schmidtmt/openmotorbridge/docs/images/cad/cvo_25_anniversary_eagle_master.png

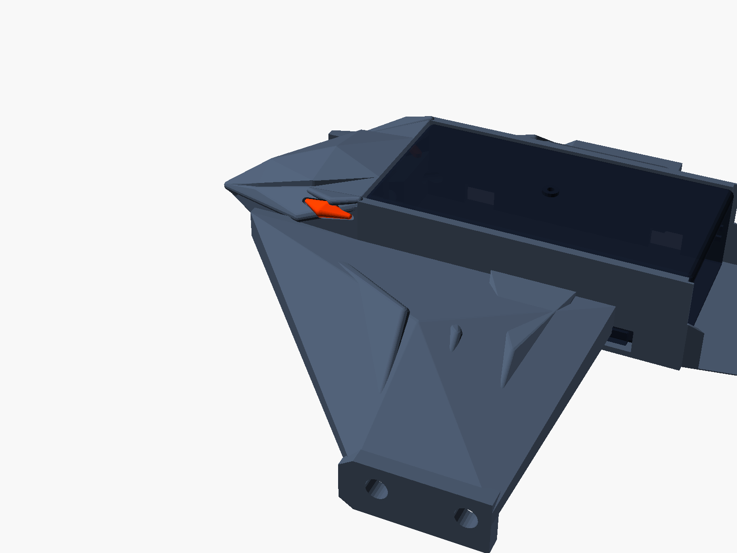
docs/images/cad/cvo_25_anniversary_eagle_master.png
