schmidtmt/openmotorbridge/docs/images/cad/cvo_st_telemetry_fin_cad.png

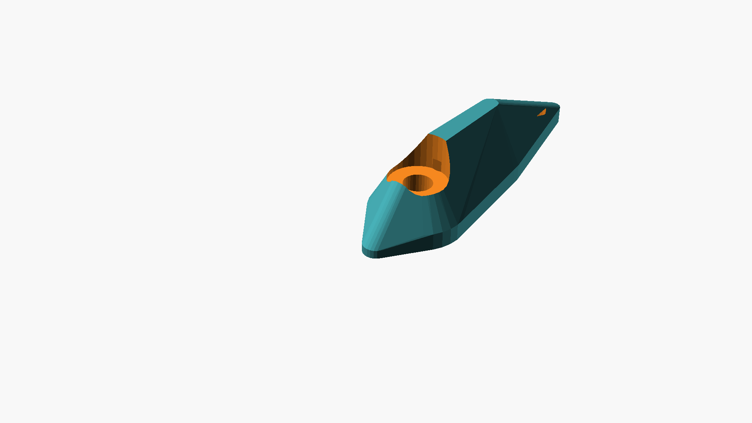
docs/images/cad/cvo_st_telemetry_fin_cad.png
