schmidtmt/openmotorbridge/docs/images/cad/cvo_st_undercowl_skeleton_dock_cad.png

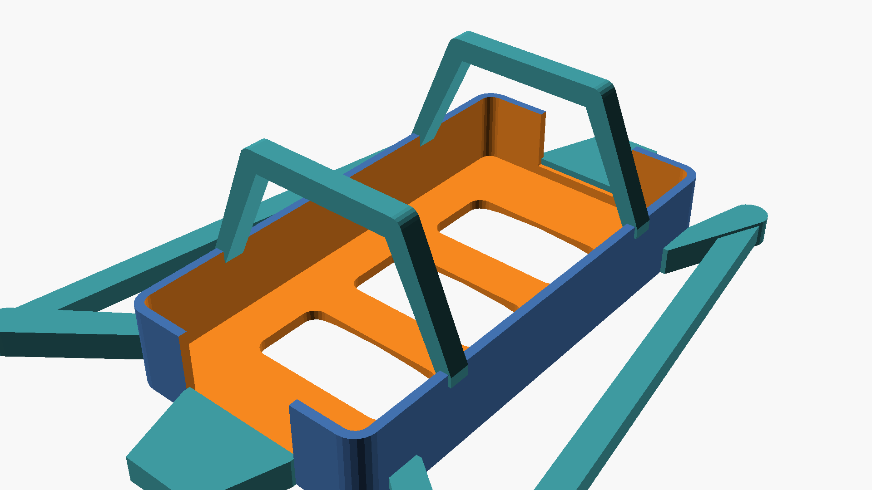
docs/images/cad/cvo_st_undercowl_skeleton_dock_cad.png
