schmidtmt/openmotorbridge/docs/images/cad/fender_curved_saddle_cad.png

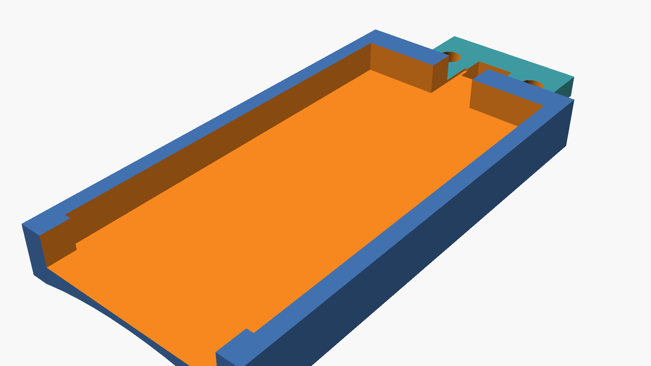
docs/images/cad/fender_curved_saddle_cad.png
