schmidtmt/openmotorbridge/docs/images/cad/front_node_3d_render_bottom.png

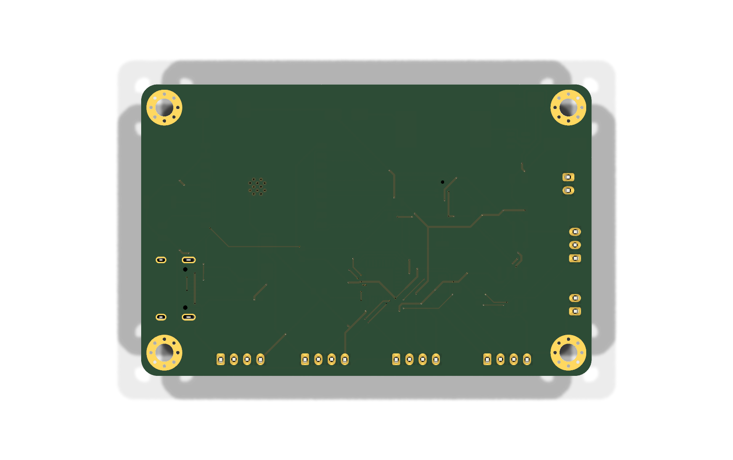
docs/images/cad/front_node_3d_render_bottom.png
