schmidtmt/openmotorbridge/docs/images/cad/front_node_3d_render_top.png

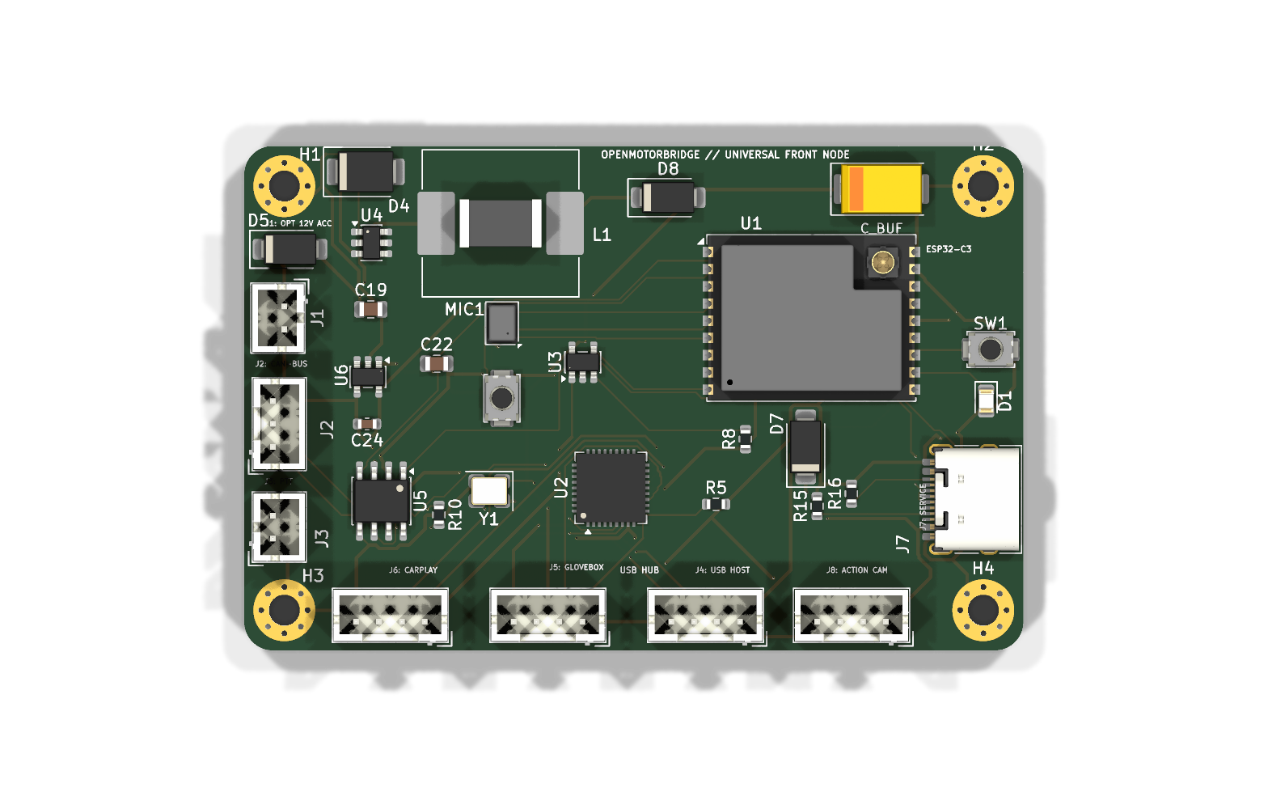
docs/images/cad/front_node_3d_render_top.png
