schmidtmt/openmotorbridge/docs/images/cad/main_board_pcb_top_down.png

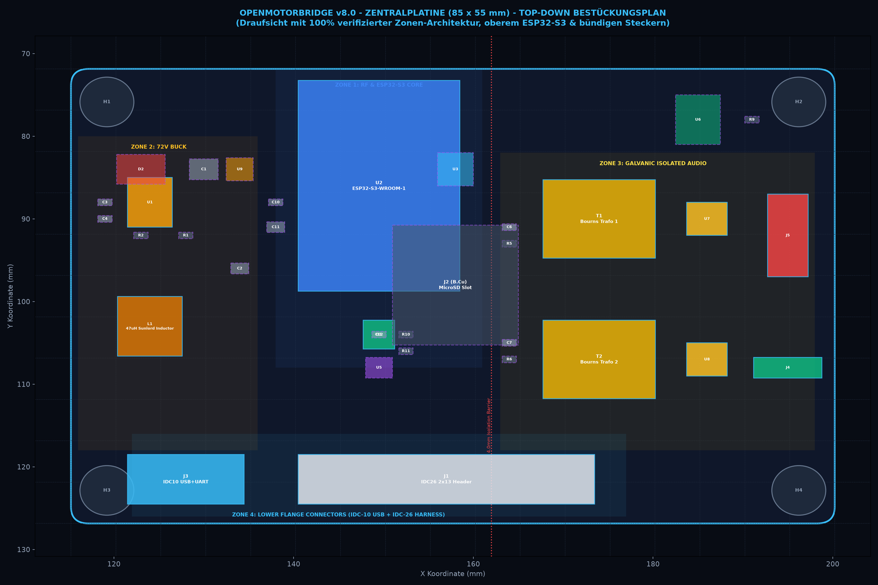
docs/images/cad/main_board_pcb_top_down.png
