schmidtmt/openmotorbridge/docs/images/cad/openmotorbridge_pod_exploded_view.png

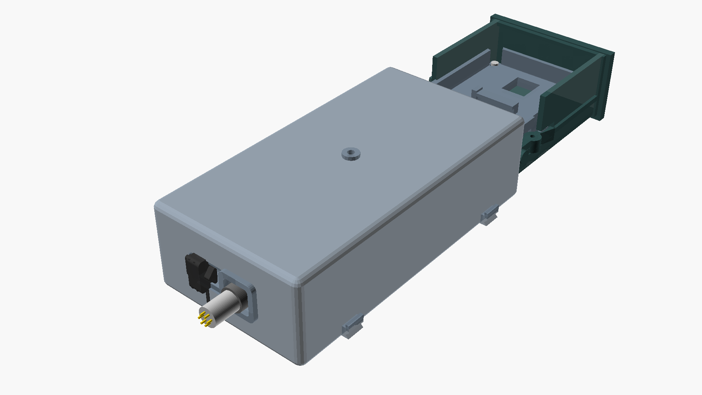
docs/images/cad/openmotorbridge_pod_exploded_view.png
