schmidtmt/openmotorbridge/docs/images/cad/pod3_fender_exploded_stack_3d.png

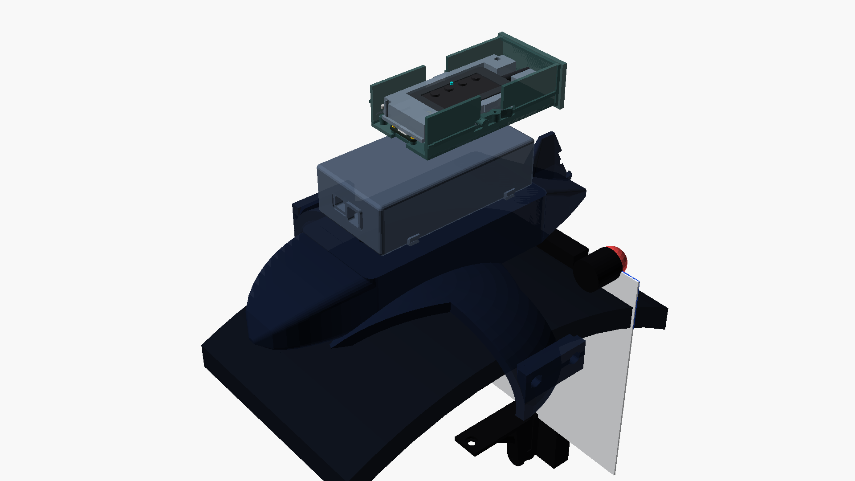
docs/images/cad/pod3_fender_exploded_stack_3d.png
