schmidtmt/openmotorbridge/docs/images/cad/pod3_radar_cutaway_3d.png

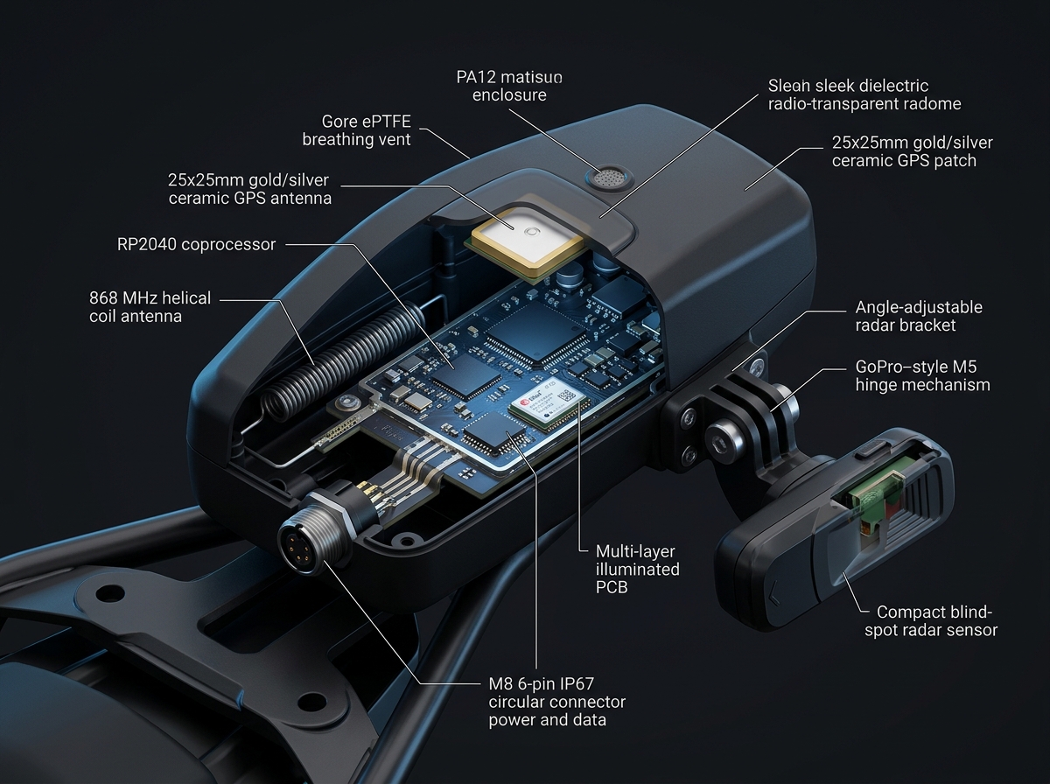
docs/images/cad/pod3_radar_cutaway_3d.png
