schmidtmt/openmotorbridge/docs/images/cad/pod3_st_aero_winglet_cad.png

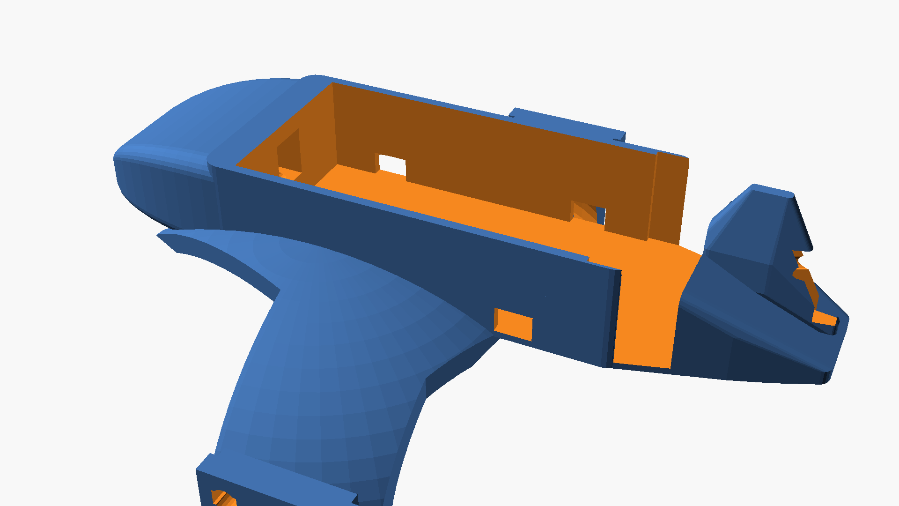
docs/images/cad/pod3_st_aero_winglet_cad.png
