schmidtmt/openmotorbridge/docs/images/cad/pod3_st_f117_stealth_nacelle.png

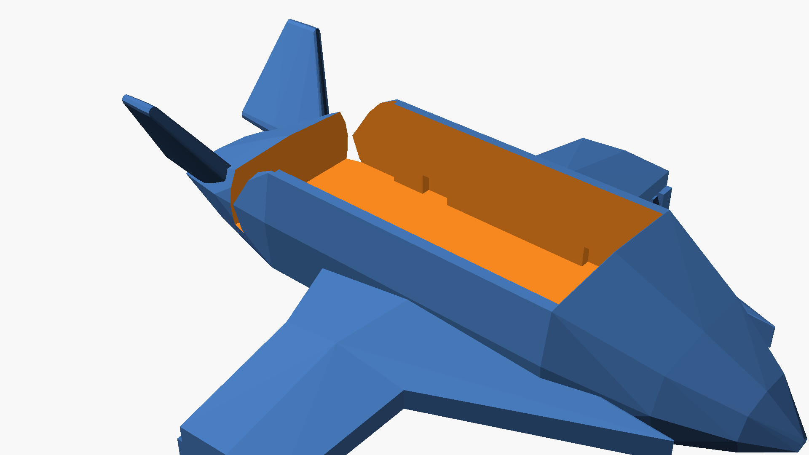
docs/images/cad/pod3_st_f117_stealth_nacelle.png
