schmidtmt/openmotorbridge/docs/images/cad/pod3_touring_fender_console.png

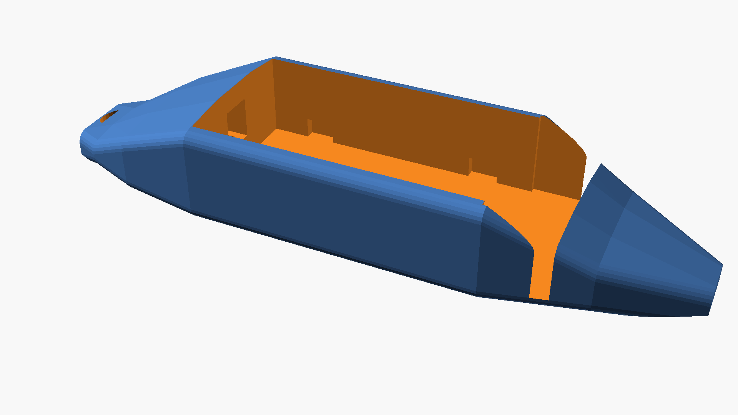
docs/images/cad/pod3_touring_fender_console.png
