schmidtmt/openmotorbridge/docs/images/cad/pod3_touring_fender_console_cad.png

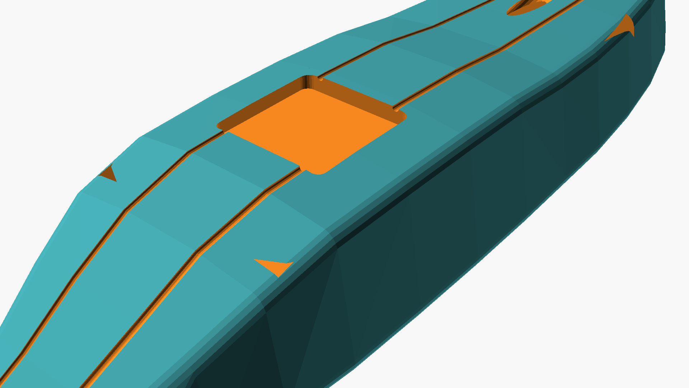
docs/images/cad/pod3_touring_fender_console_cad.png
