schmidtmt/openmotorbridge/docs/images/cad/pod3_touring_stealth_cad.png

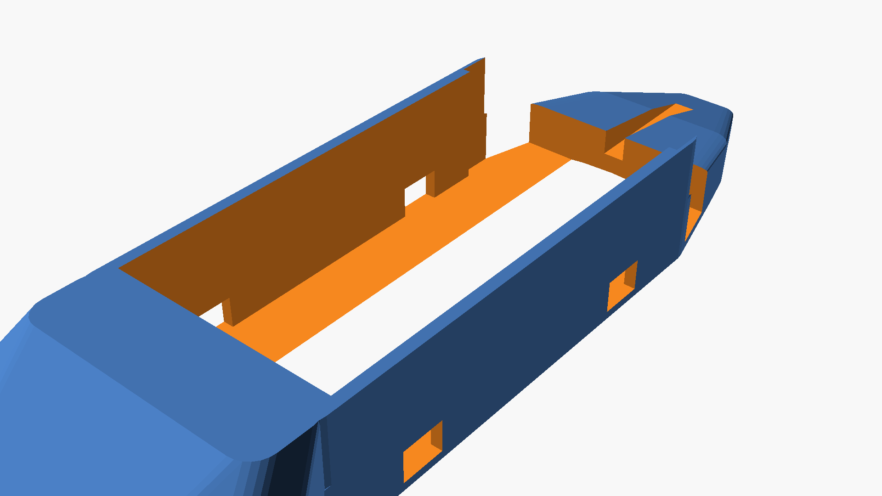
docs/images/cad/pod3_touring_stealth_cad.png
