schmidtmt/openmotorbridge/docs/images/cad/pod_base_rear_dual_port_cad.png

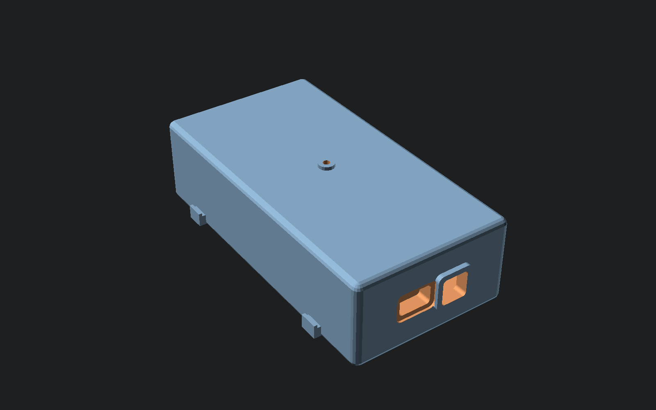
docs/images/cad/pod_base_rear_dual_port_cad.png
