schmidtmt/openmotorbridge/docs/images/cad/rack_tail_mount_cad.png

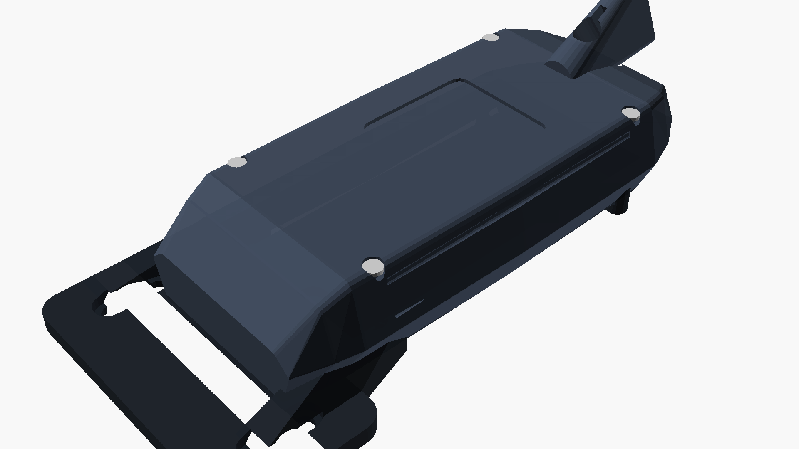
docs/images/cad/rack_tail_mount_cad.png
