schmidtmt/openmotorbridge/docs/images/cad/rack_tail_mount_side_cross_section.png

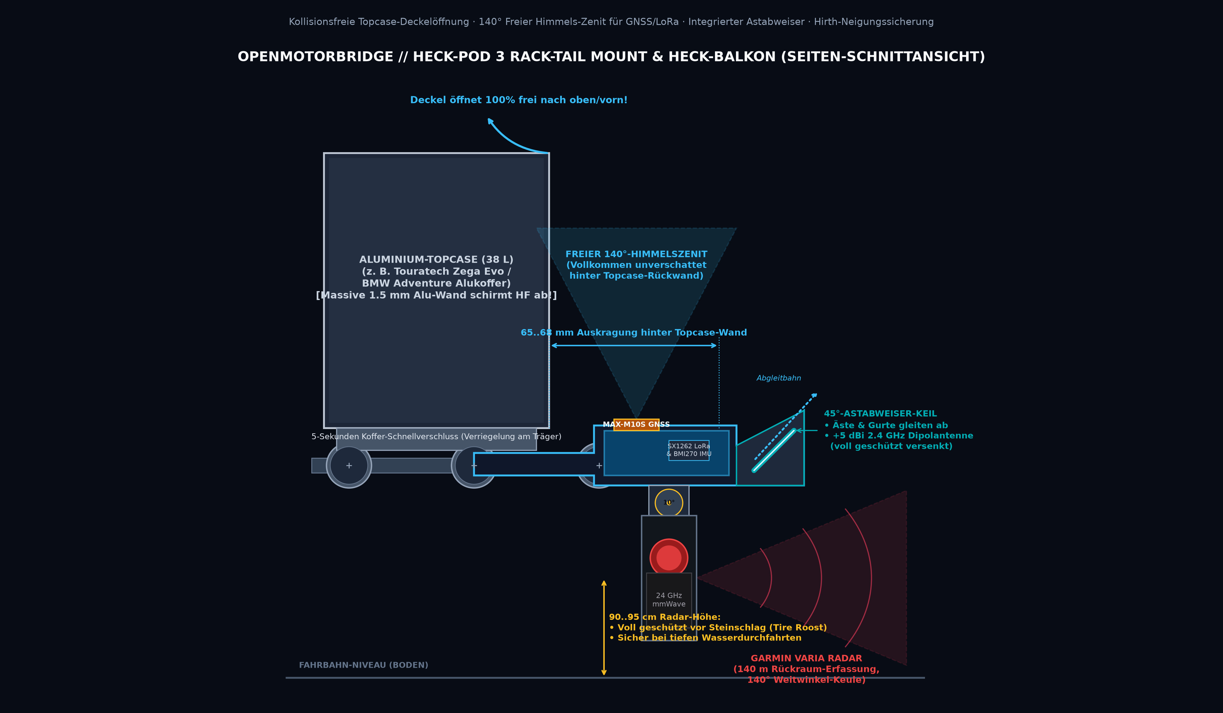
docs/images/cad/rack_tail_mount_side_cross_section.png
