schmidtmt/openmotorbridge/docs/images/cad/rack_tail_mount_top_view.png

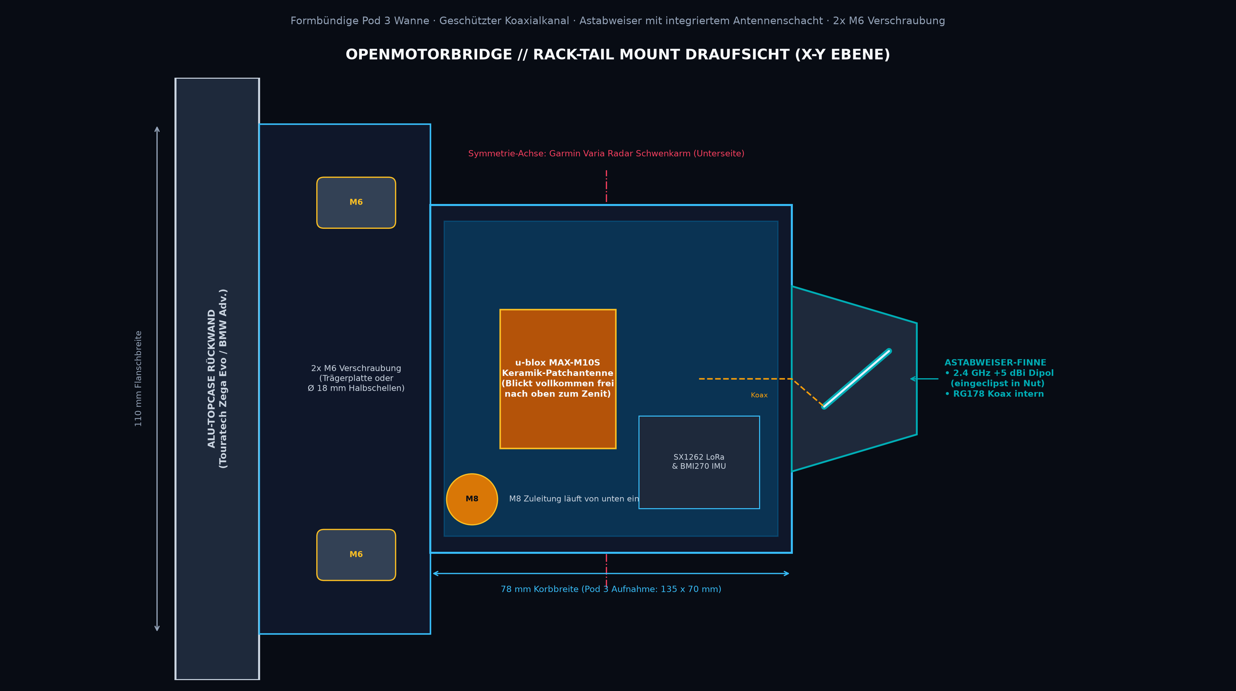
docs/images/cad/rack_tail_mount_top_view.png
