schmidtmt/openmotorbridge/docs/images/cad/radar_hirth_lock_dock_cad.png

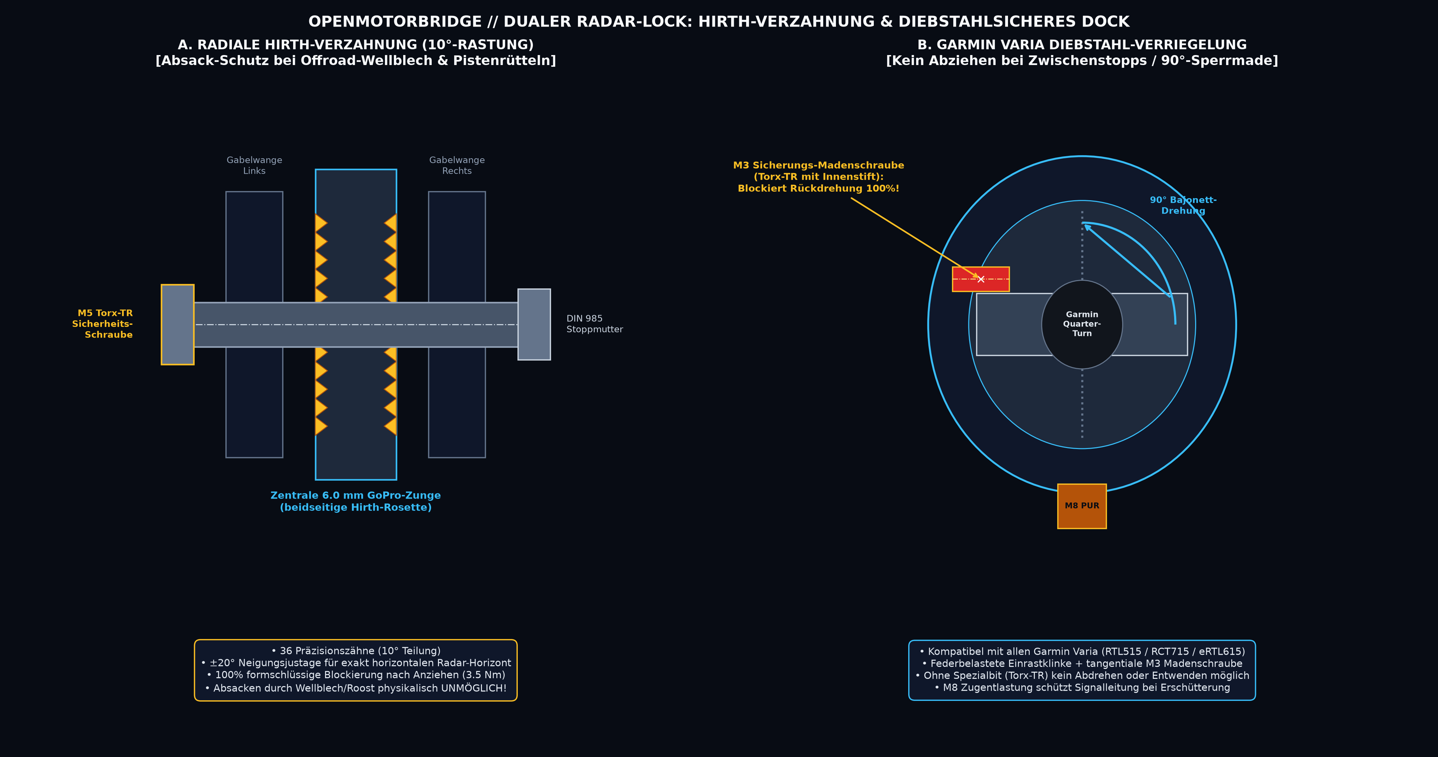
docs/images/cad/radar_hirth_lock_dock_cad.png
