schmidtmt/openmotorbridge/docs/images/pcba/pcba01_central_box_top.png

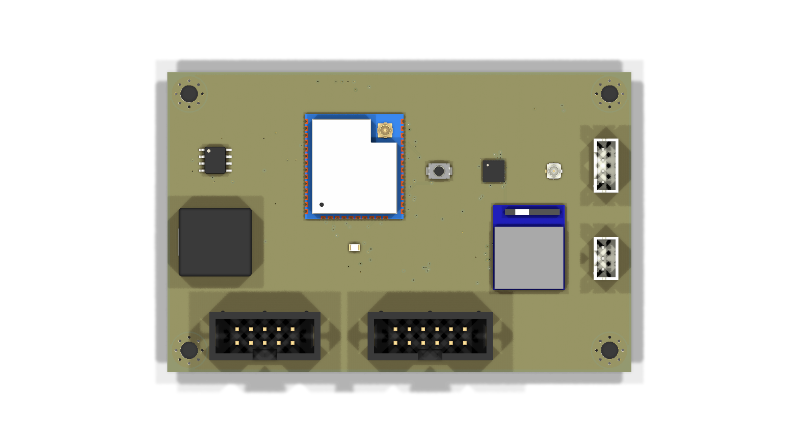
docs/images/pcba/pcba01_central_box_top.png
