schmidtmt/openmotorbridge/docs/images/pcba/pcba02_pod_base_3d.png

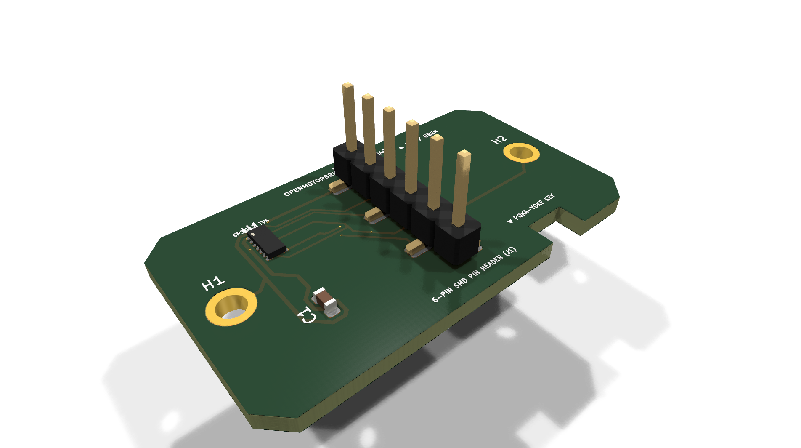
docs/images/pcba/pcba02_pod_base_3d.png
