schmidtmt/openmotorbridge/docs/images/pcba/pcba03_pod_cartridge_top.png

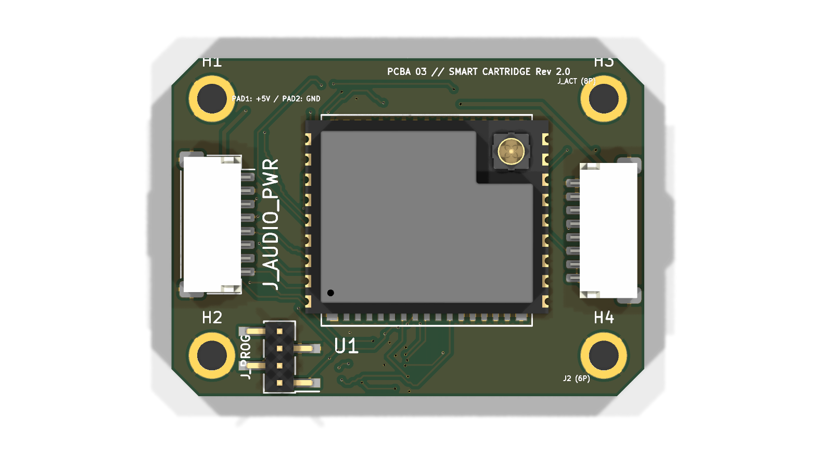
docs/images/pcba/pcba03_pod_cartridge_top.png
