schmidtmt/openmotorbridge/docs/images/pcba/pcba04_rear_pod3_3d.png

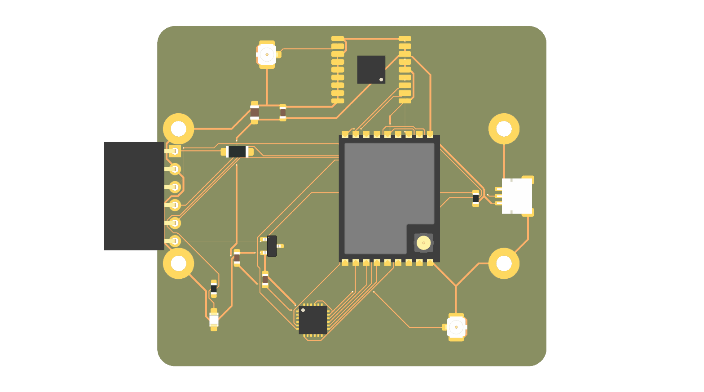
docs/images/pcba/pcba04_rear_pod3_3d.png
