schmidtmt/openmotorbridge/docs/images/pcba/pcba05_front_node_top.png

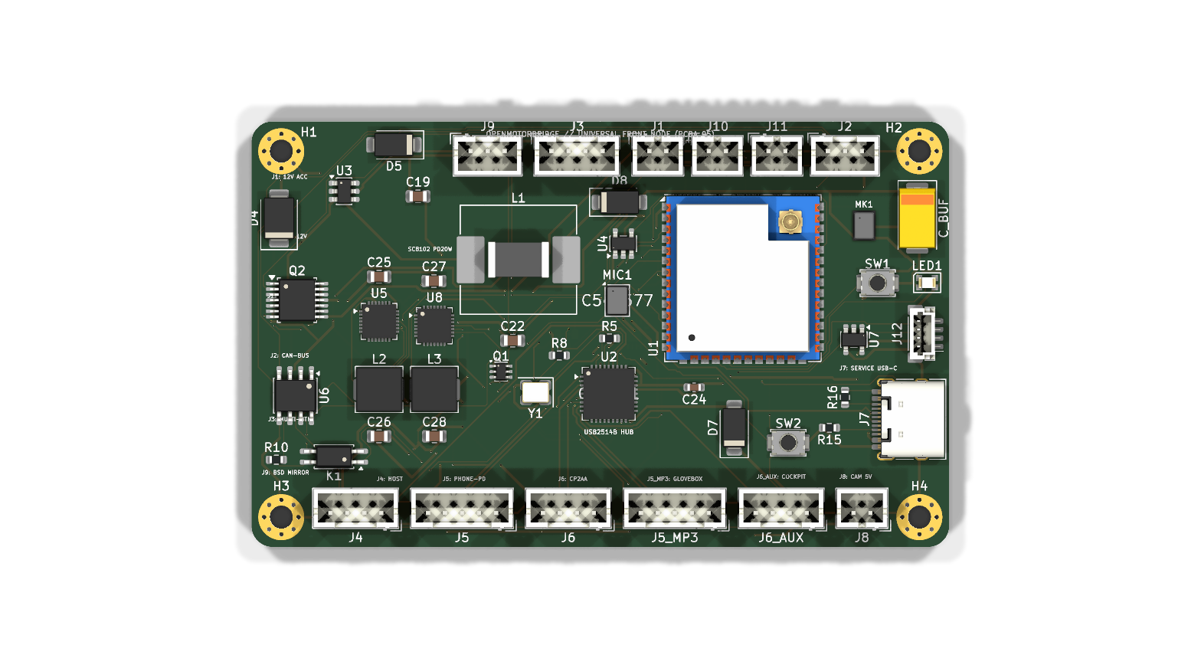
docs/images/pcba/pcba05_front_node_top.png
