schmidtmt/openmotorbridge/docs/images/pcba/pcba06_magsafe_dock_bottom_3d.png

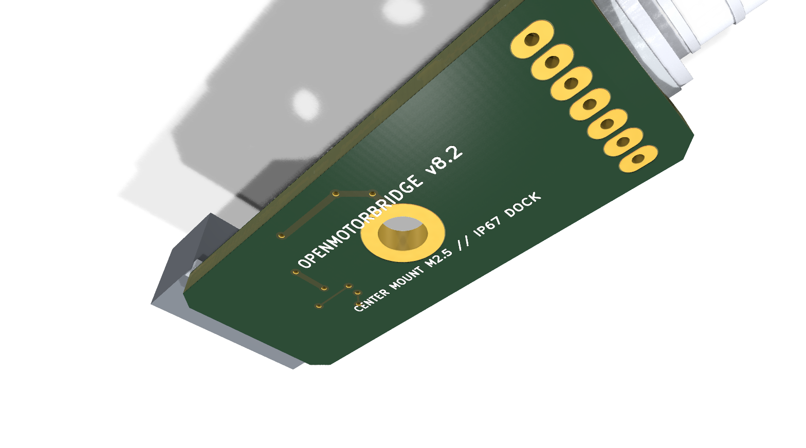
docs/images/pcba/pcba06_magsafe_dock_bottom_3d.png
