schmidtmt/openmotorbridge/docs/images/pcba/pcba06_magsafe_dock_top.png

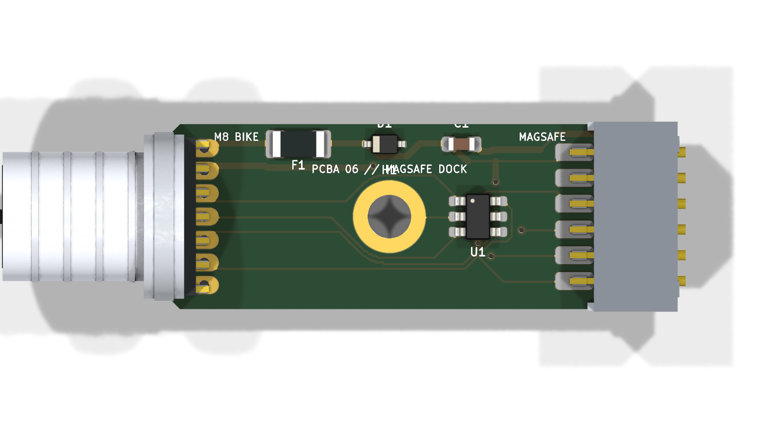
docs/images/pcba/pcba06_magsafe_dock_top.png
