schmidtmt/openmotorbridge/docs/images/pcba/pcba07_smart_keyfob_top.png

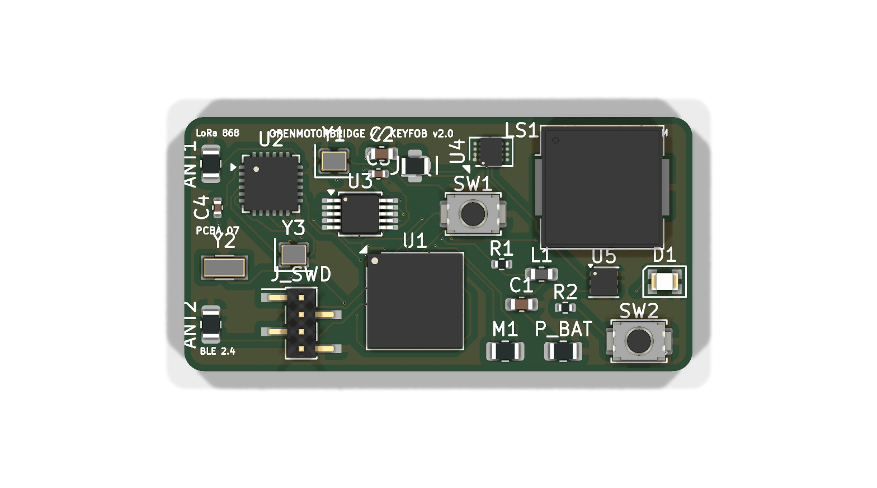
docs/images/pcba/pcba07_smart_keyfob_top.png
