schmidtmt/openmotorbridge/docs/images/pcba/pcba08_radar_submcu_bottom_3d.png

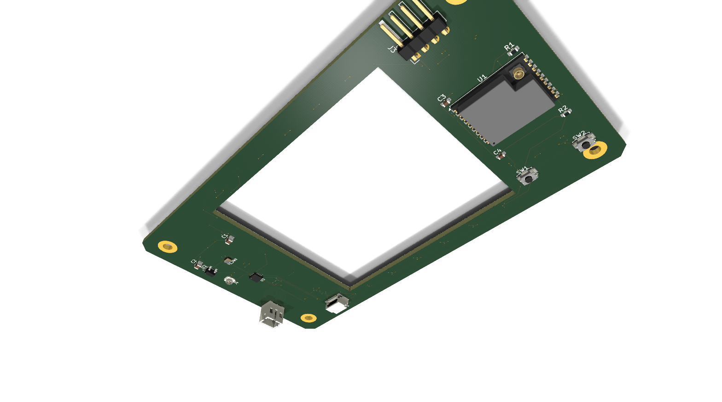
docs/images/pcba/pcba08_radar_submcu_bottom_3d.png
