schmidtmt/openmotorbridge/docs/images/pcba/pcba09_omm_intercom_bottom.png

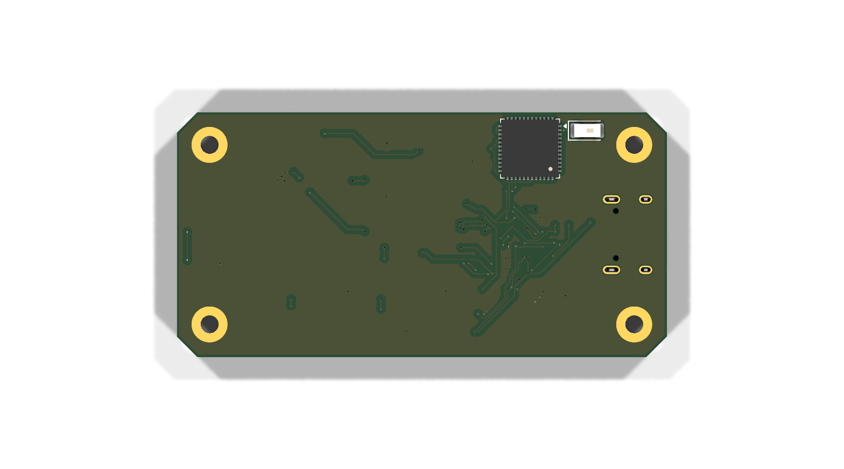
docs/images/pcba/pcba09_omm_intercom_bottom.png
