schmidtmt/openmotorbridge/docs/images/pcba/pcba09_omm_intercom_top.png

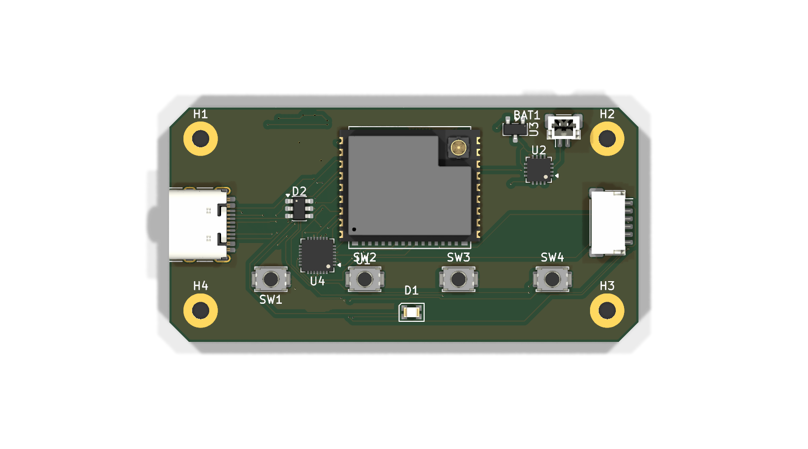
docs/images/pcba/pcba09_omm_intercom_top.png
