schmidtmt/openmotorbridge/docs/images/pcba/pcba10_omm446_intercom_bottom.png

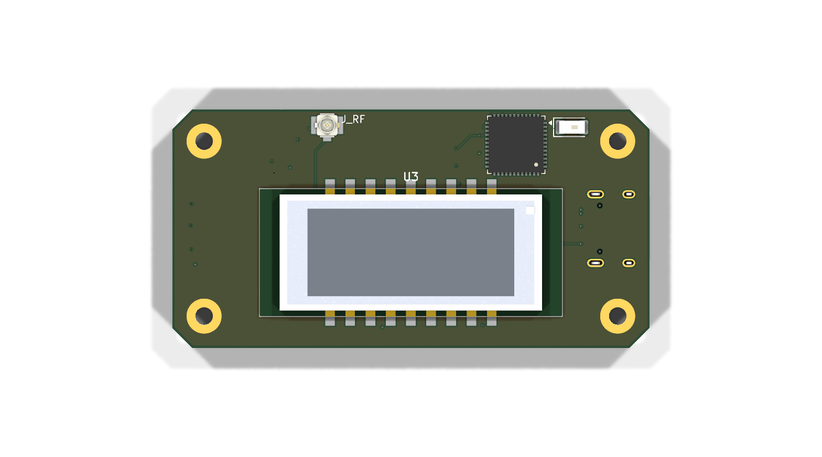
docs/images/pcba/pcba10_omm446_intercom_bottom.png
