schmidtmt/openmotorbridge/docs/images/pwa/pwa_tab1_cockpit_radar_hud.png

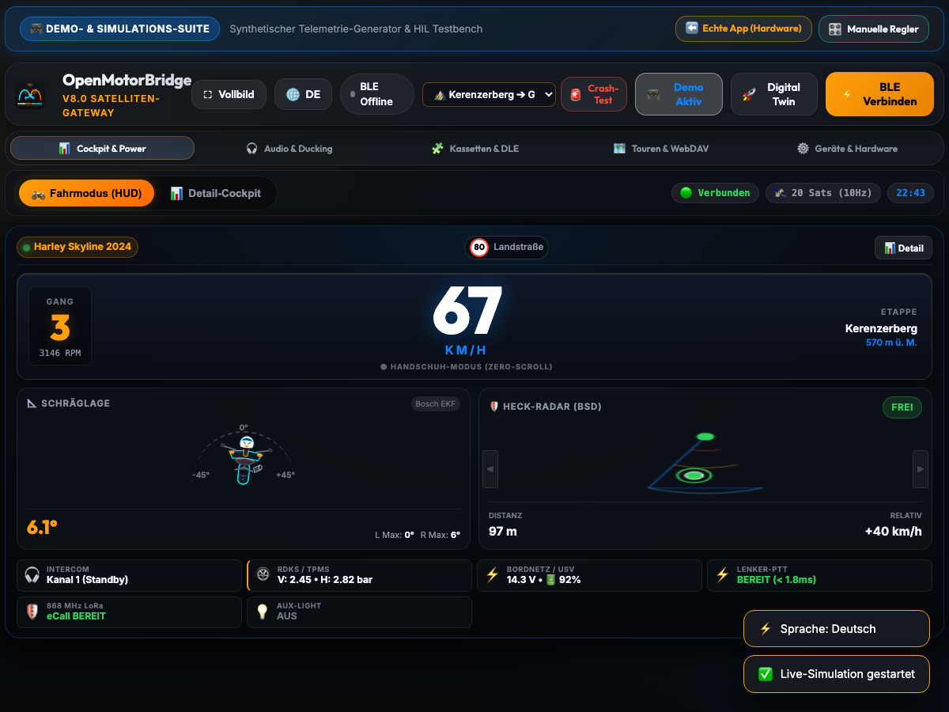
docs/images/pwa/pwa_tab1_cockpit_radar_hud.png
