schmidtmt/openmotorbridge/docs/images/pwa/pwa_tab2_audio_smart_cartridge.png

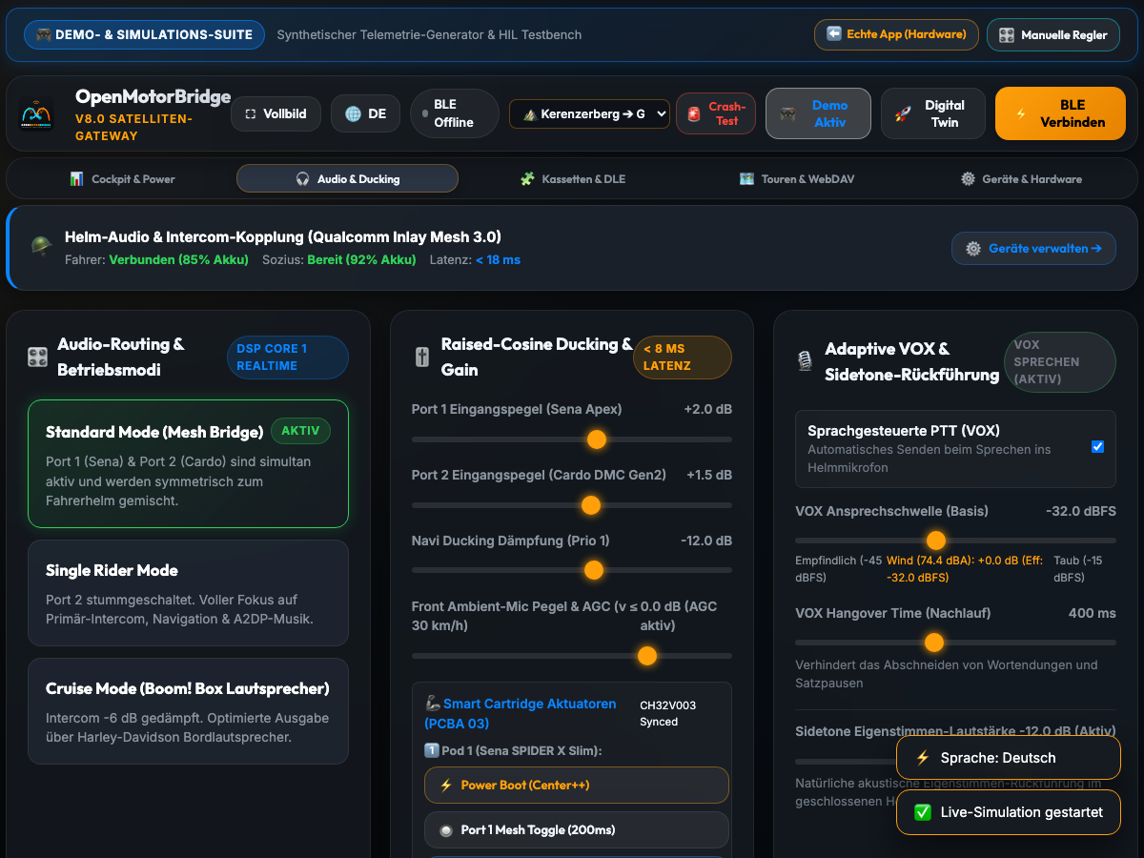
docs/images/pwa/pwa_tab2_audio_smart_cartridge.png
