schmidtmt/openmotorbridge/docs/images/pwa/pwa_tab3_cartridges_dle_status.png

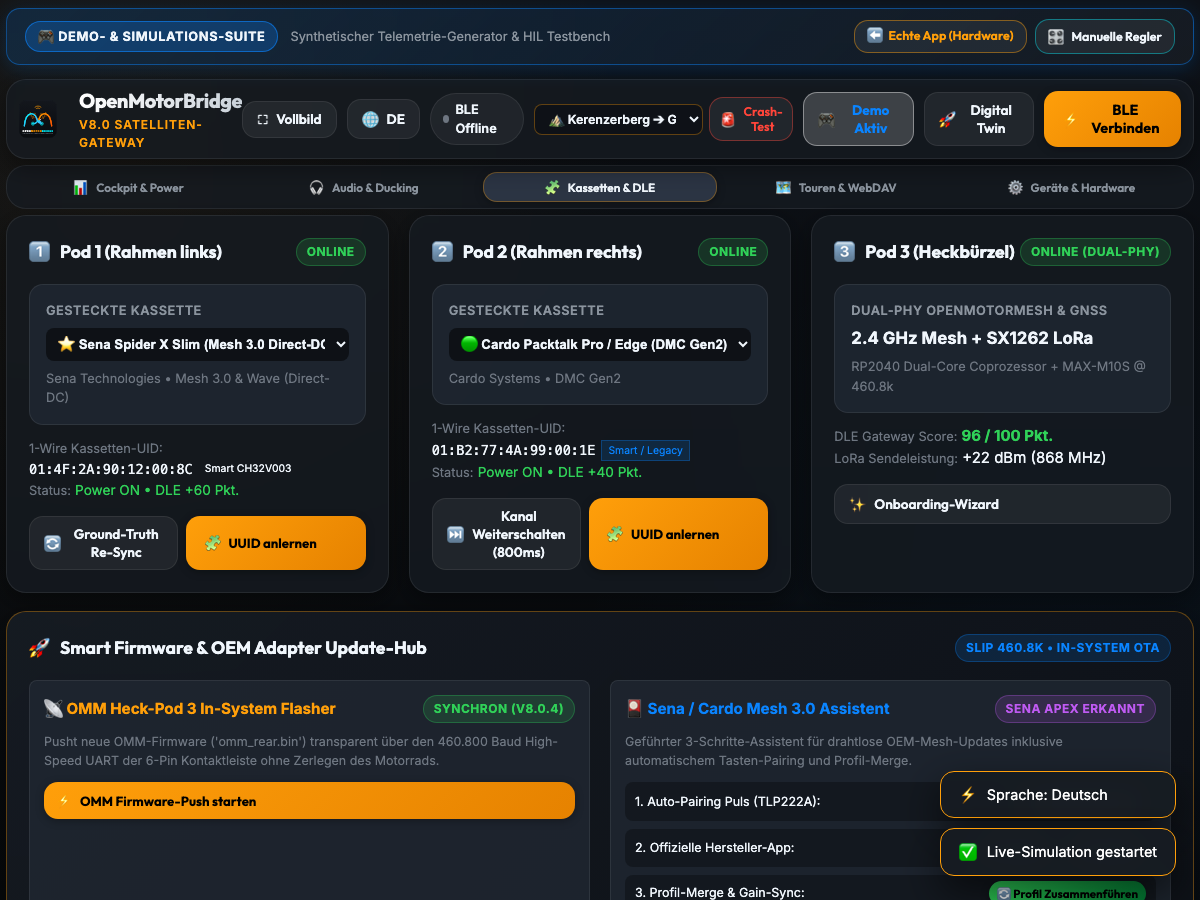
docs/images/pwa/pwa_tab3_cartridges_dle_status.png
