schmidtmt/openmotorbridge/docs/images/pwa/pwa_tab4_tours_gpx_export.png

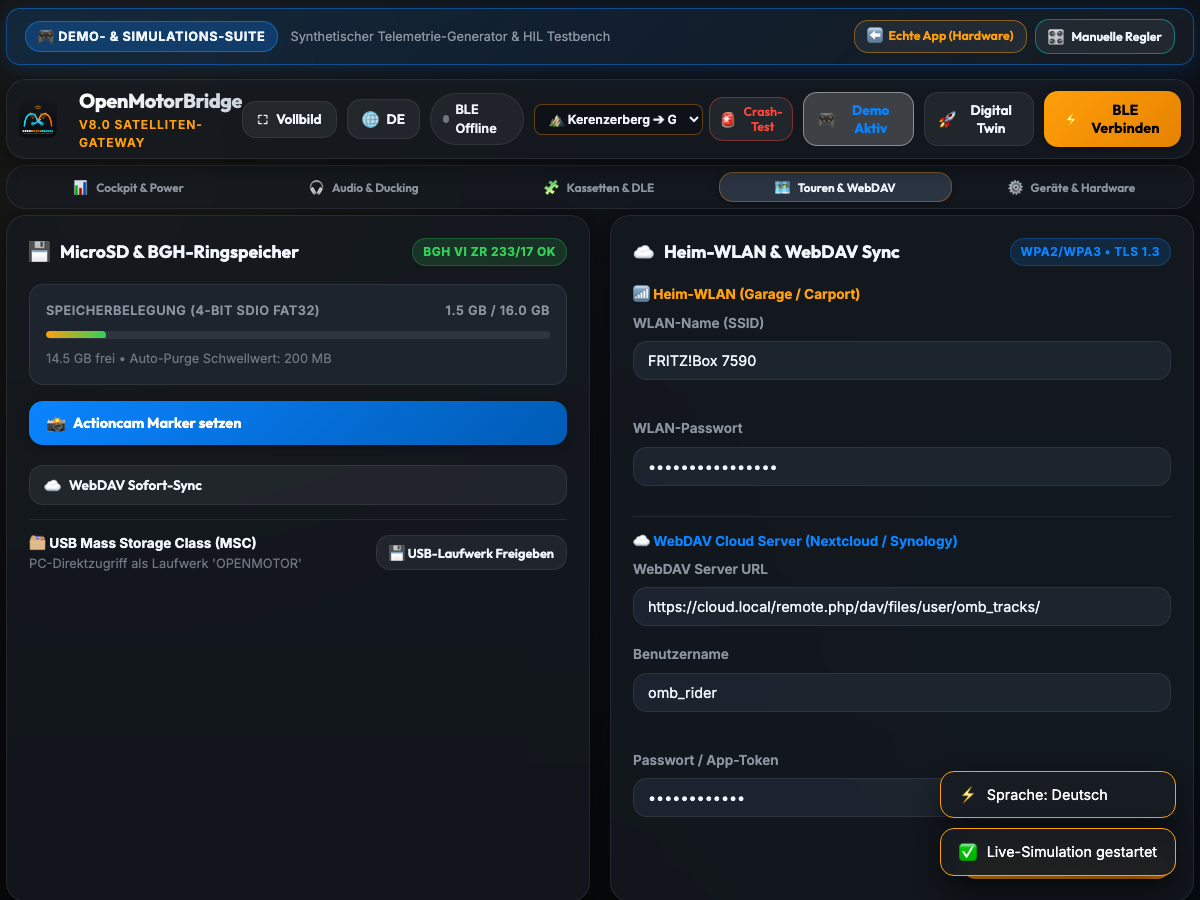
docs/images/pwa/pwa_tab4_tours_gpx_export.png
