schmidtmt/openmotorbridge/docs/images/pwa/pwa_tab5_device_hub_keyfob.png

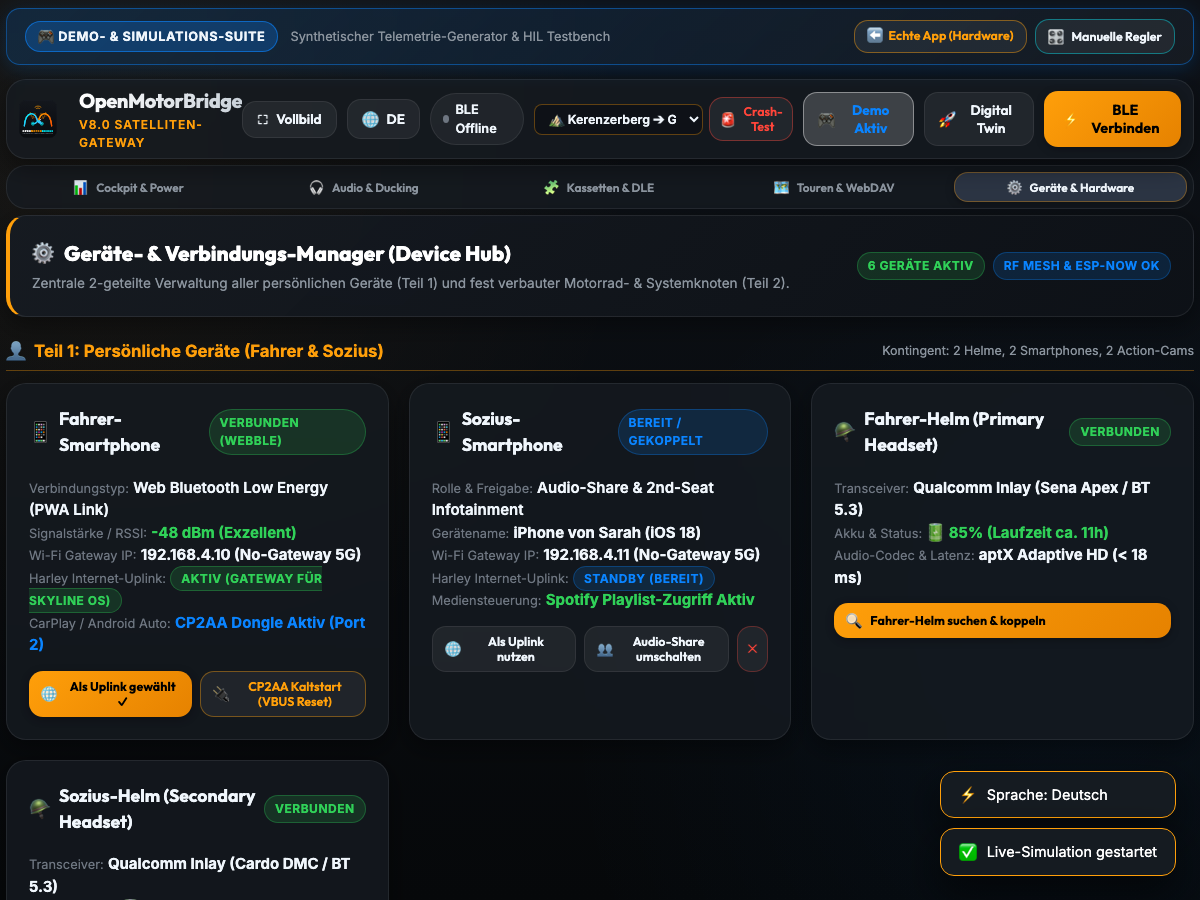
docs/images/pwa/pwa_tab5_device_hub_keyfob.png
