schmidtmt/openmotorbridge/hardware/cad/cartridge_variants_trio.png

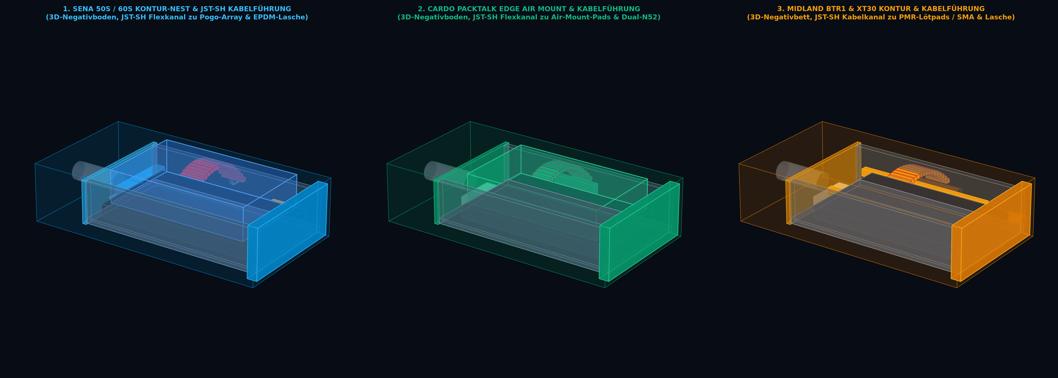
hardware/cad/cartridge_variants_trio.png
