schmidtmt/openmotorbridge/hardware/cad/dummy_cartridge_cad.png

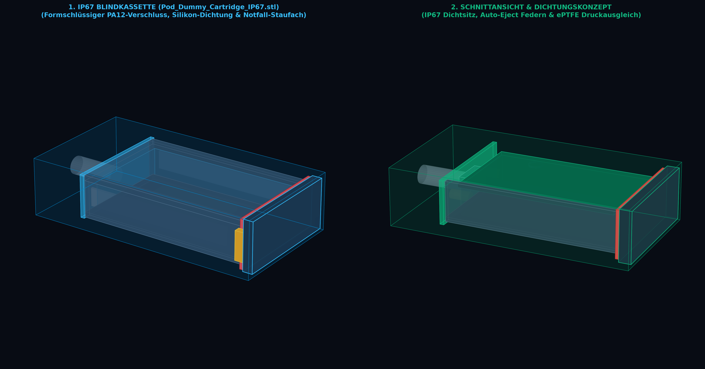
hardware/cad/dummy_cartridge_cad.png
