schmidtmt/openmotorbridge/hardware/cad/pod3_st_aero_winglet_cad.png

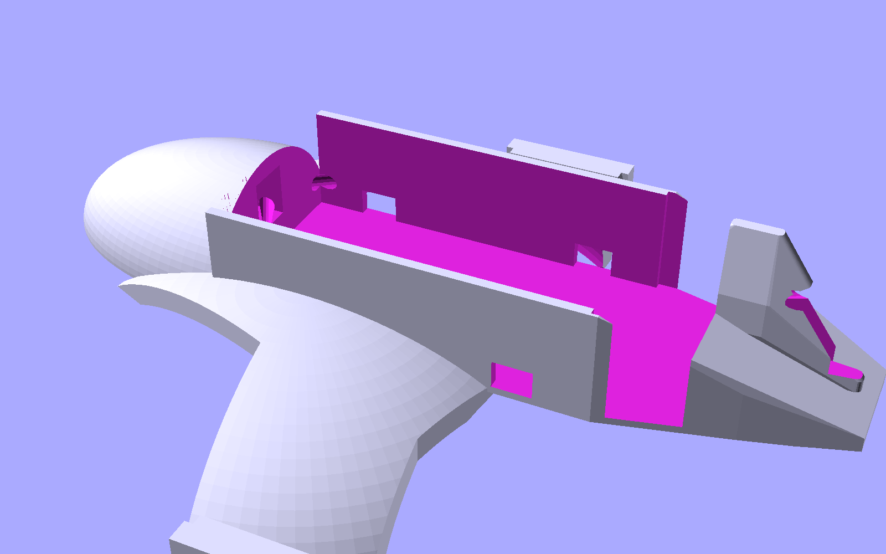
hardware/cad/pod3_st_aero_winglet_cad.png
