schmidtmt/openmotorbridge/hardware/kicad_pod_base/kicad_3d_render.png

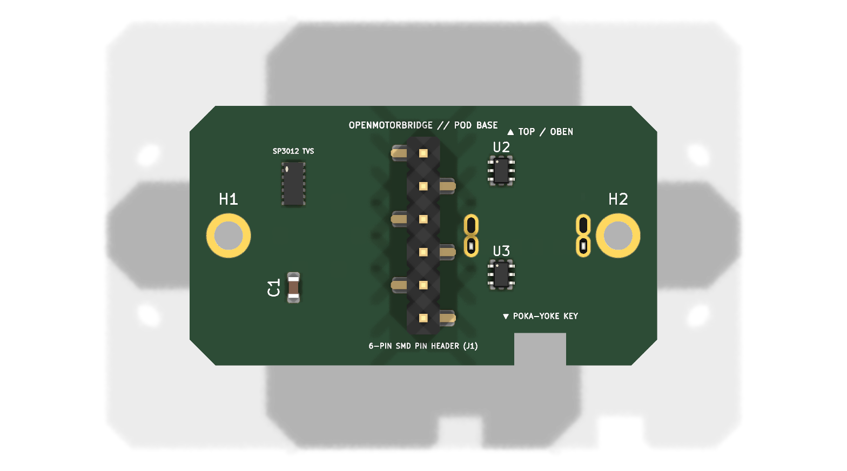
hardware/kicad_pod_base/kicad_3d_render.png
