schmidtmt/openmotorbridge/hardware/kicad_pod_base/kicad_3d_render_bottom.png

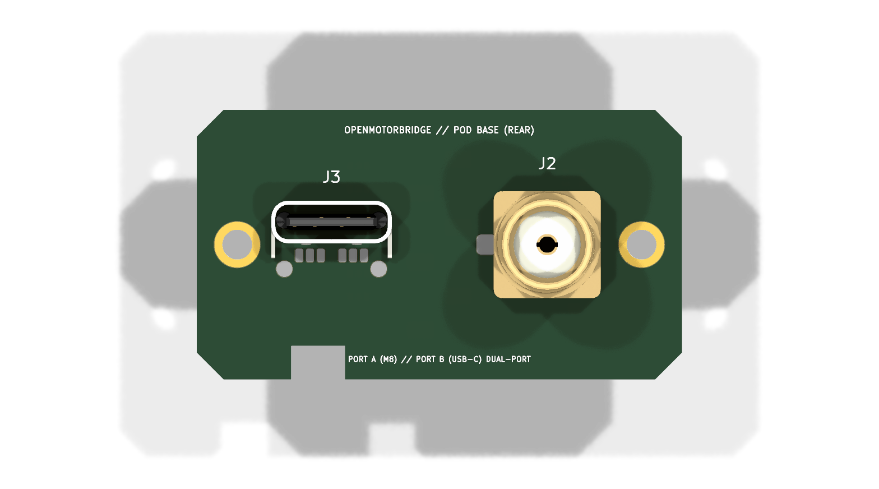
hardware/kicad_pod_base/kicad_3d_render_bottom.png
