schmidtmt/openmotorbridge/hardware/kicad_pod_base/pod_base_3d_iso_bottom.png

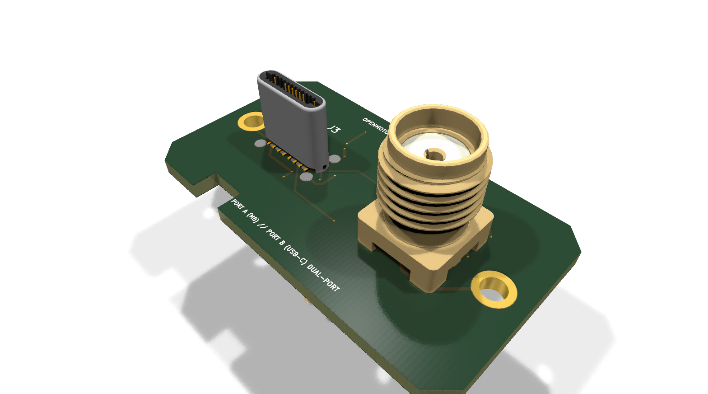
hardware/kicad_pod_base/pod_base_3d_iso_bottom.png
