schmidtmt/openmotorbridge/hardware/kicad_pod_base/pod_base_3d_render_top.png

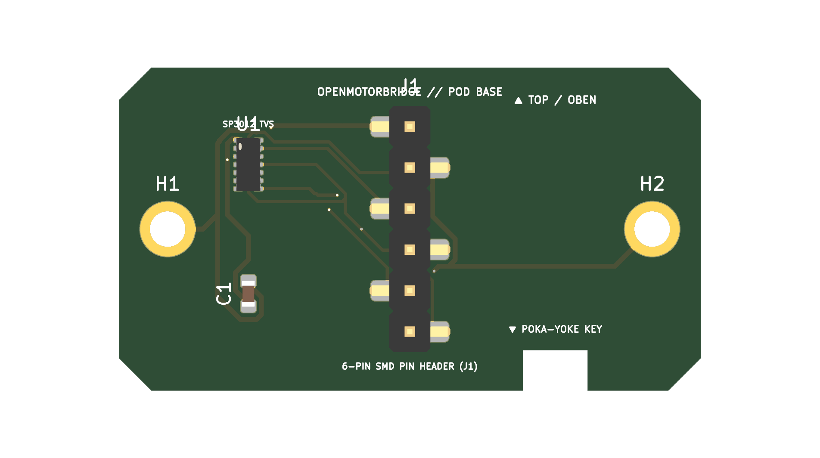
hardware/kicad_pod_base/pod_base_3d_render_top.png
