schmidtmt/openmotorbridge/hardware/kicad_pod_base/pod_base_smd_render_bottom.png

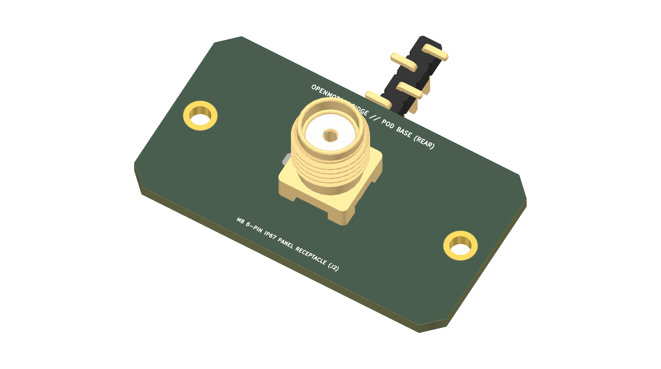
hardware/kicad_pod_base/pod_base_smd_render_bottom.png
