schmidtmt/openmotorbridge/hardware/kicad_pod_base/pod_base_vertical_bottom.png

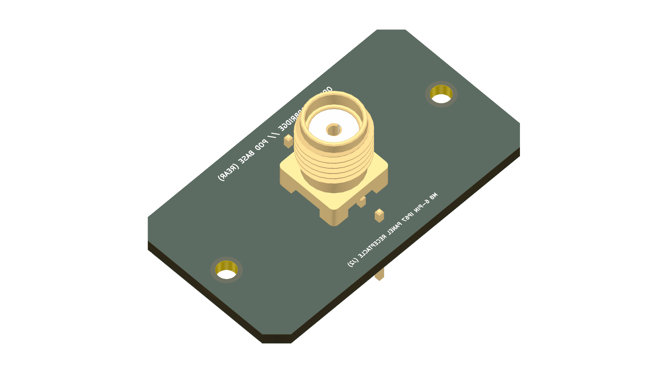
hardware/kicad_pod_base/pod_base_vertical_bottom.png
