schmidtmt/openmotorbridge/hardware/kicad_pod_base/pod_base_vertical_top.png

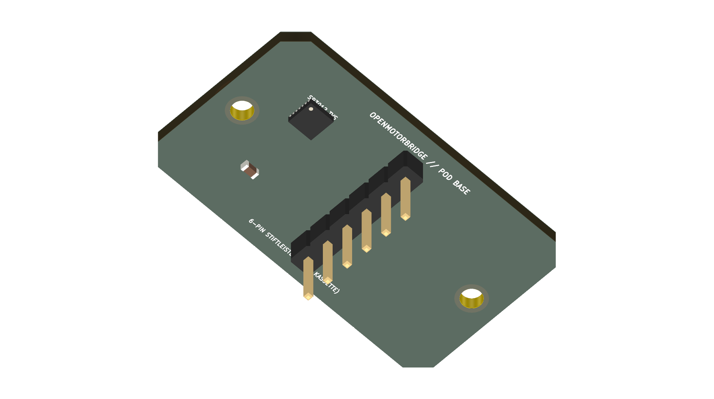
hardware/kicad_pod_base/pod_base_vertical_top.png
