schmidtmt/openmotorbridge/hardware/kicad_rear_pod3/kicad_3d_render.png

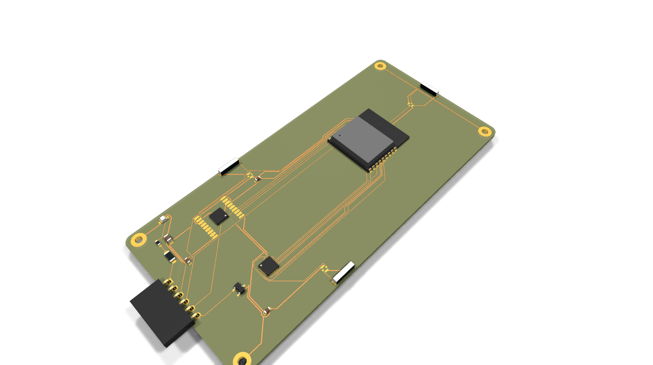
hardware/kicad_rear_pod3/kicad_3d_render.png
