schmidtmt/openmotorbridge/hardware/kicad_rear_pod3/rear_pod3_3d_render_bottom.png

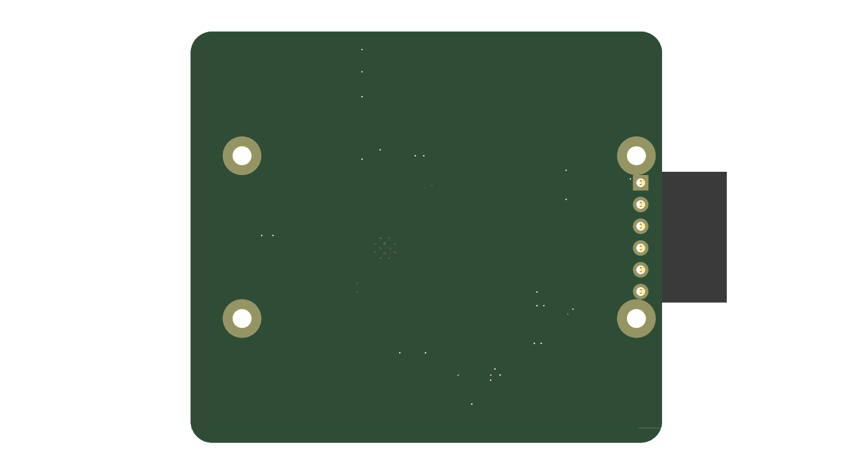
hardware/kicad_rear_pod3/rear_pod3_3d_render_bottom.png
