schmidtmt/openmotorbridge/hardware/kicad_rear_pod3/rear_pod3_final_routed_bottom.png

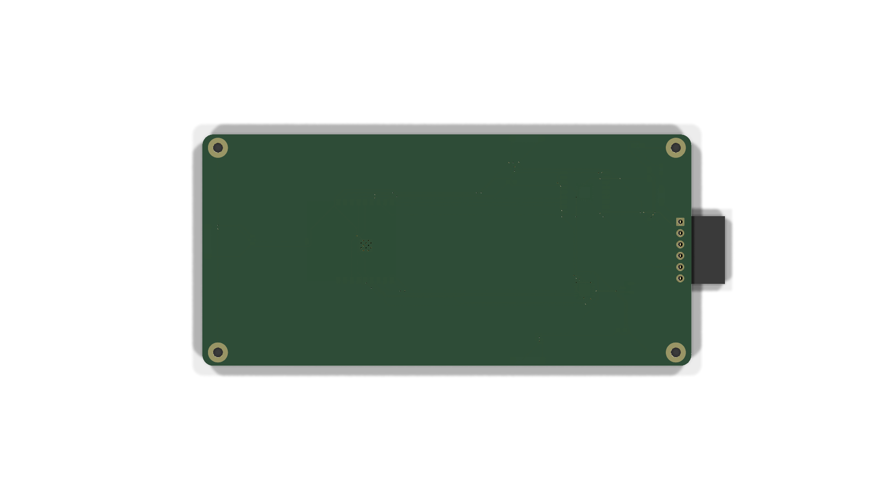
hardware/kicad_rear_pod3/rear_pod3_final_routed_bottom.png
