schmidtmt/openmotorbridge/hardware/kicad_rear_pod3/rear_pod3_final_routed_top.png

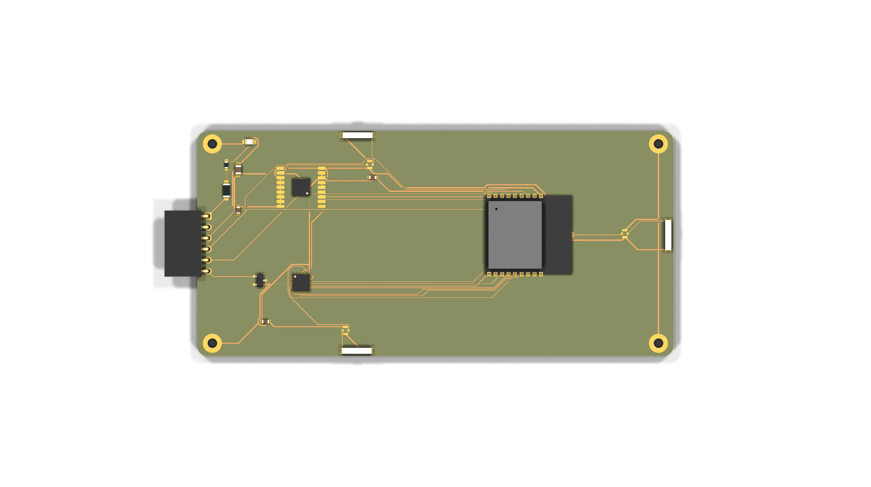
hardware/kicad_rear_pod3/rear_pod3_final_routed_top.png
