schmidtmt/openmotorbridge/hardware/jlcpcb_bom_cpl/BOM_Main_Box_JLCPCB.csv

Designator | Comment | Footprint | LCSC Part # | Quantity
ANT1 | Taoglas_FXP895_868MHz_Lid | U.FL_Hirose_U.FL-R-SMT-1_Vertical | C2834595 | 1
ANT2 | Taoglas_FXUWB10_6.5GHz_Ch5_Floor | U.FL_Hirose_U.FL-R-SMT-1_Vertical | C2834595 | 1
C1 | 10uF_100V | Capacitor_SMD:C_0805_2012Metric |  | 1
C10 | 100nF_MCU | Capacitor_SMD:C_0603_1608Metric |  | 1
C11 | 10uF_MCU | Capacitor_SMD:C_0805_2012Metric |  | 1
C12 | 100nF_IMU | Capacitor_SMD:C_0603_1608Metric |  | 1
C2 | 22uF_16V | Capacitor_SMD:C_0805_2012Metric |  | 1
C3 | 100nF_BST | Capacitor_SMD:C_0603_1608Metric |  | 1
C4 | 100nF_VCC | Capacitor_SMD:C_0603_1608Metric |  | 1
C6 | 1uF_POD1 | Capacitor_SMD:C_0603_1608Metric |  | 1
C7 | 1uF_POD2 | Capacitor_SMD:C_0603_1608Metric |  | 1
D1 | WS2812B_RGB | LED_SMD:LED_WS2812B-2020 |  | 1
D2 | SMBJ33CA_TVS | Diode_SMD:D_SMB |  | 1
H1, H2, H3, H4 |  | MountingHole:MountingHole_3.2mm_M3_Pad_Via |  | 4
J1 | DEUTSCH_DTM12_HEADER | Connector_IDC:IDC-Header_2x13_P2.54mm_Vertical | C2934175 | 1
J2 | MicroSD_Card | Connector_Card:microSD_HC_Molex_47571-0001 |  | 1
J3 | USB2_IDC_HEADER_9PIN | Connector_IDC:IDC-Header_2x05_P2.54mm_Vertical |  | 1
J4 | RGB_LED_3PIN | Connector_JST:JST_PH_B3B-PH-K_1x03_P2.00mm_Vertical |  | 1
J5 | PWR_BAT_NTC_4PIN | Connector_JST:JST_PH_B4B-PH-K_1x04_P2.00mm_Vertical |  | 1
L1 | 47uH_Inductor | Inductor_SMD:L_Sunlord_MWSA1206S-470 |  | 1
R1 | 100k_EN | Resistor_SMD:R_0603_1608Metric |  | 1
R10 | 4k7_SDA | Resistor_SMD:R_0603_1608Metric |  | 1
R11 | 4k7_SCL | Resistor_SMD:R_0603_1608Metric |  | 1
R2 | 10k_EN | Resistor_SMD:R_0603_1608Metric |  | 1
R5 | 600R_POD1 | Resistor_SMD:R_0603_1608Metric |  | 1
R6 | 600R_POD2 | Resistor_SMD:R_0603_1608Metric |  | 1
R9 | 120R_CAN | Resistor_SMD:R_0603_1608Metric |  | 1
SW1 | SW_PAIR_RESET | SW_Push_SPST_NO_Alps_SKRK | C318884 | 1
U1 | LM5164-Q1 | Package_SO:SOIC-8-1EP_3.9x4.9mm_P1.27mm_EP2.41x3.3mm |  | 1
U2 | ESP32-S3-WROOM-1U-N16R8 | ESP32-S3-WROOM-1U |  | 1
U3 | ES8388_Codec | Package_DFN_QFN:QFN-28-1EP_4x4mm_P0.4mm_EP2.4x2.4mm |  | 1
U5 | BMI270_IMU | Package_LGA:LGA-14_2.5x3mm_P0.5mm |  | 1
U6 | TCAN334G | Package_SO:SOIC-8_3.9x4.9mm_P1.27mm |  | 1
U7 | SX1262IMLTRT | QFN-24-1EP_4x4mm_P0.5mm_EP2.8x2.8mm | C190184 | 1
U8 | DW3110 | QFN-16-1EP_3x3mm_P0.5mm_EP1.7x1.7mm_ThermalVias | C2934600 | 1
U9 | TPS7A0533_LDO | Package_TO_SOT_SMD:SOT-23-5 |  | 1
