schmidtmt/openmotorbridge/hardware/production_packages/10_omm446_ucs_pcba/10_omm446_ucs_pcba_bom_jlcpcb.csv

Designator | Comment | Footprint | LCSC Part # | Quantity
ANT1 | 2.45GHz_Chip_Antenna | RF_Antenna:Johanson_2450AT18x100 | C2909988 | 1
BAT1 | JST_2P_LiPo_600mAh | JST_SH_BM02B-SRSS-TB_1x02-1MP_P1.00mm_Vertical | C2902341 | 1
D1 | WS2812B-2020 | LED_WS2812B-2020_PLCC4_2.0x2.0mm | C2843785 | 1
D2 | USBLC6-2SC6 | SOT-23-6 | C7519 | 1
J1 | TYPE-C-31-M-12_IP67 | USB_C_Receptacle_HRO_TYPE-C-31-M-12 | C2765186 | 1
J_HELMET | HELMET_AUDIO_6P | JST_SH_SM06B-SRSS-TB_1x06-1MP_P1.00mm_Horizontal | C136657 | 1
J_RF | U.FL-R-SMT-1 | U.FL_Hirose_U.FL-R-SMT-1_Vertical | C14899 | 1
PAD_ANT | Contact_Spring_Helix | TestPoint_Pad_D3.0mm |  | 1
SW1 | BTN_PTT | SW_Push_SPST_NO_Alps_SKRK | C318884 | 1
SW2 | BTN_MODE | SW_Push_SPST_NO_Alps_SKRK | C318884 | 1
SW3 | BTN_CH_UP | SW_Push_SPST_NO_Alps_SKRK | C318884 | 1
SW4 | BTN_CH_DOWN | SW_Push_SPST_NO_Alps_SKRK | C318884 | 1
U1 | ESP32-C6-MINI-1U | ESP32-S2-MINI-1U | C5267233 | 1
U2 | BQ24075RGTR | VQFN-16-1EP_3x3mm_P0.5mm_EP1.8x1.8mm | C96825 | 1
U3 | SA818-DMR | NiceRF_SA818-DMR_SMD_38x16mm | C2839211 | 1
U4 | ES8388 | QFN-28-1EP_4x4mm_P0.4mm_EP2.4x2.4mm | C365736 | 1
U5 | ME6211C33M5G | SOT-23 | C82942 | 1
U6 | ESP32-PICO-V3-02 | Package_DFN_QFN:QFN-48-1EP_7x7mm_P0.5mm_EP5.3x5.3mm | C2686884 | 1
