schmidtmt/openmotorbridge/hardware/production_packages/02_pod_base_pcba/02_pod_base_pcba_bom_jlcpcb.csv

Designator | Comment | Footprint | LCSC Part # | Quantity
C1 | 100nF_50V | Capacitor_SMD:C_0603_1608Metric |  | 1
H1, H2 | M2_MountingHole | MountingHole:MountingHole_2.2mm_M2_Pad |  | 2
J1 | MILL_MAX_824_SMD_6P | Connector_PinHeader_2.54mm:PinHeader_1x06_P2.54mm_Vertical_SMD_Pin1Left |  | 1
J2 | PORT_A_M8_6PIN | Connector_M8:M8_6Pin_IP67_Receptacle_Socketed |  | 1
J3 | PORT_B_USBC_VERTICAL | Connector_USB:USB_C_Receptacle_Vertical_6P |  | 1
U1 | SP3012-06UTG | Package_DFN_QFN:DFN-14_1.35x3.5mm_P0.5mm |  | 1
U2 | LM66100_PORTA | Package_TO_SOT_SMD:SOT-363_SC-70-6 |  | 1
U3 | LM66100_PORTB | Package_TO_SOT_SMD:SOT-363_SC-70-6 |  | 1
