schmidtmt/openmotorbridge/hardware/kicad_pod_base/openmotorbridge_pod_base.step

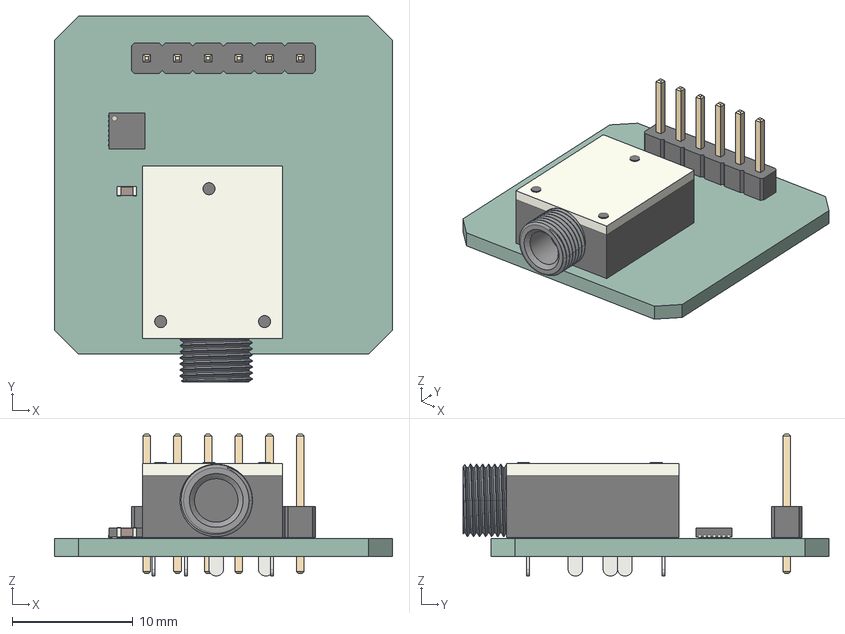
[picture p127: CAD file, 2026-08-24]
hardware/kicad_pod_base/openmotorbridge_pod_base.step
28.0 x 30.3 x 11.7 mm
DFN_14_1EP_3x3mm_Pitch04mm
Jack_3.5mm_Ledino_KB3SPRS_Horizontal
PinHeader_1x06_P254mm_Vertical
C_0603_1608Metric
openmotorbridge_pod_base_PCB
