schmidtmt/openmotorbridge/hardware/kicad_pod_cartridge/openmotorbridge_pod_cartridge.step

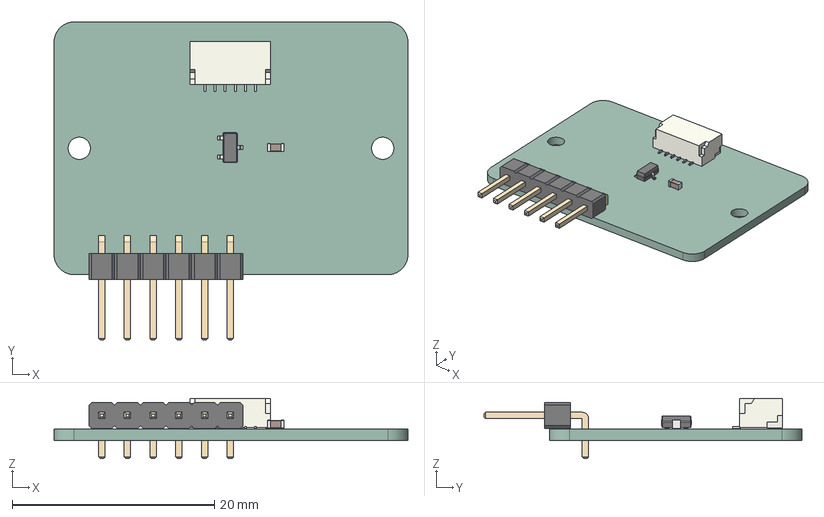
[picture p128: CAD file, 2026-08-24]
hardware/kicad_pod_cartridge/openmotorbridge_pod_cartridge.step
35.0 x 31.5 x 5.96 mm
C_0603_1608Metric
PinHeader_1x06_P254mm_Horizontal
JST_SH_SM06B-SRSS-TB_1x06-1MP_P1.00mm_Horizontal
SOT-23
openmotorbridge_pod_cartridge_PCB
