schmidtmt/openmotorbridge/hardware/cad/stl/02_pod_base/components/cots_magnetic_frame_dock_body.stl

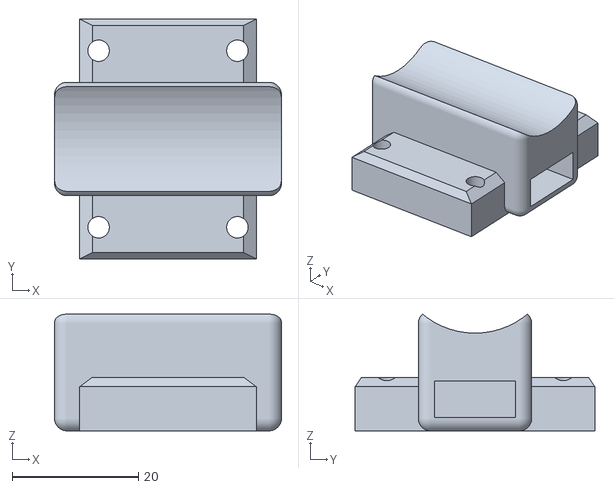
[picture p130: CAD file, 2026-10-10]
hardware/cad/stl/02_pod_base/components/cots_magnetic_frame_dock_body.stl
36.0 x 38.0 x 18.5
