schmidtmt/openmotorbridge/hardware/cad/stl/02_pod_base/design_studies/pod3_touring_stealth_console.stl

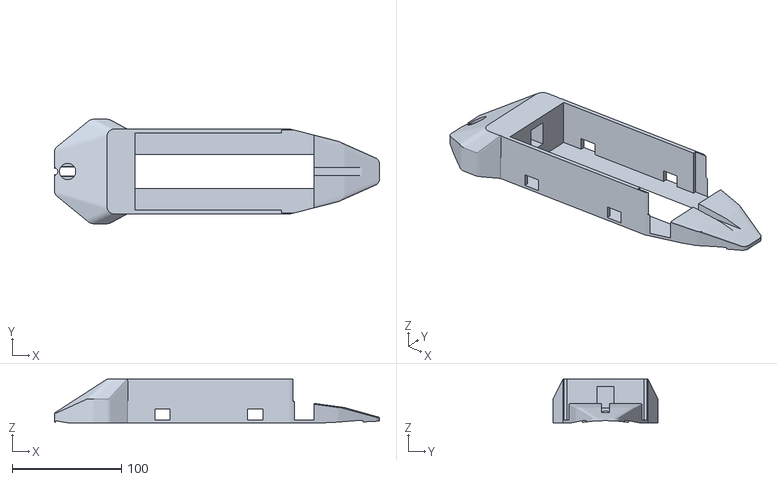
[picture p131: CAD file, 2026-09-05]
hardware/cad/stl/02_pod_base/design_studies/pod3_touring_stealth_console.stl
298.0 x 96.0 x 40.0
