schmidtmt/openmotorbridge/hardware/cad/stl/02_pod_base/pod_base_housing.stl

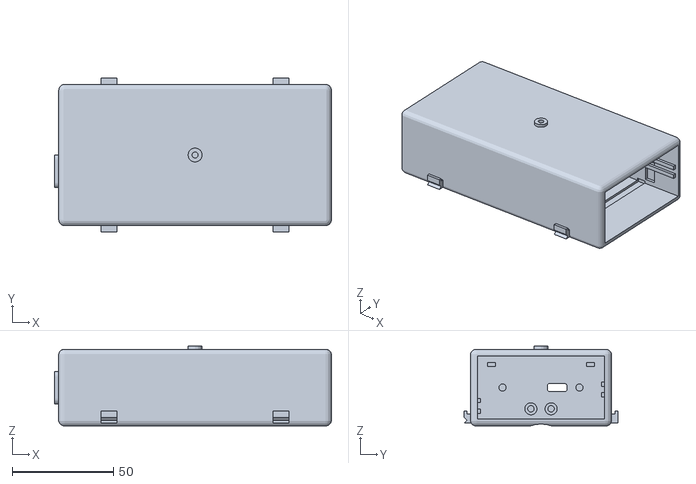
[picture p132: CAD file, 2026-10-01]
hardware/cad/stl/02_pod_base/pod_base_housing.stl
136.9 x 76.0 x 39.4
