schmidtmt/openmotorbridge/hardware/cad/stl/03_pod_cartridges/components/dummy_omm_transceiver_pcb.stl

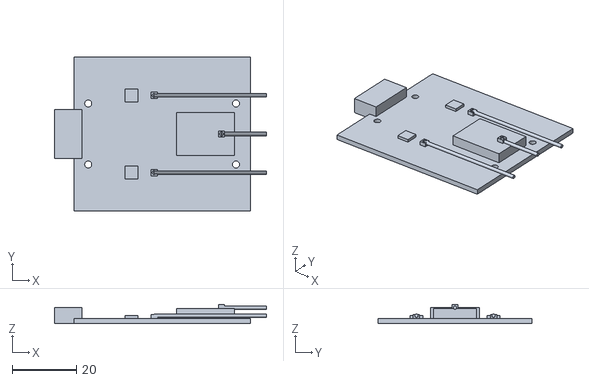
[picture p133: CAD file, 2026-09-06]
hardware/cad/stl/03_pod_cartridges/components/dummy_omm_transceiver_pcb.stl
66.0 x 48.0 x 6.03
