schmidtmt/openmotorbridge/hardware/cad/stl/03_pod_cartridges/omm_ucs_top_shell.stl

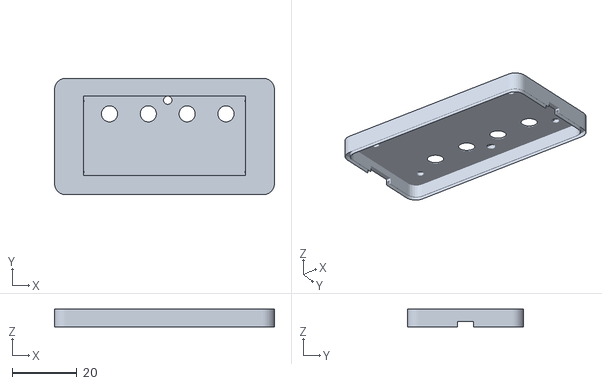
[picture p134: CAD file, 2026-10-09]
hardware/cad/stl/03_pod_cartridges/omm_ucs_top_shell.stl
68.0 x 36.0 x 5.50
