schmidtmt/openmotorbridge/hardware/cad/stl/04_front_node/components/02_pcb_standoffs.stl

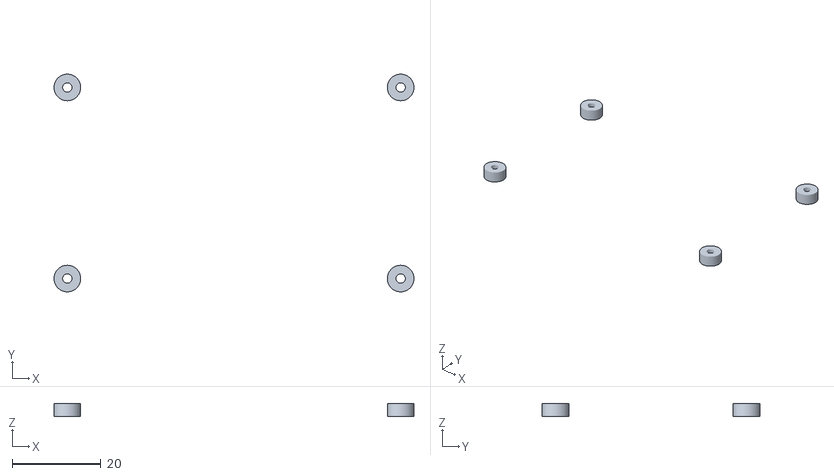
[picture p135: CAD file, 2026-09-16]
hardware/cad/stl/04_front_node/components/02_pcb_standoffs.stl
81.0 x 49.0 x 3.00
