schmidtmt/openmotorbridge/hardware/cad/stl/04_front_node/front_node_fairing_tube_clamp.stl

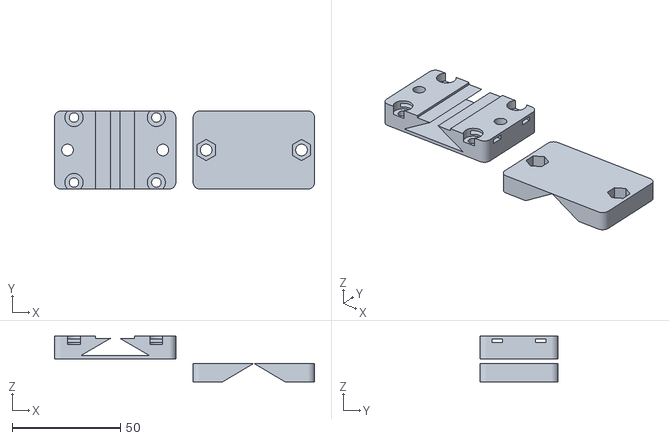
[picture p136: CAD file, 2026-10-09]
hardware/cad/stl/04_front_node/front_node_fairing_tube_clamp.stl
120.0 x 36.0 x 21.0
