schmidtmt/openmotorbridge/hardware/cad/stl/05_accessories/car_dashboard_wedge_dock.stl

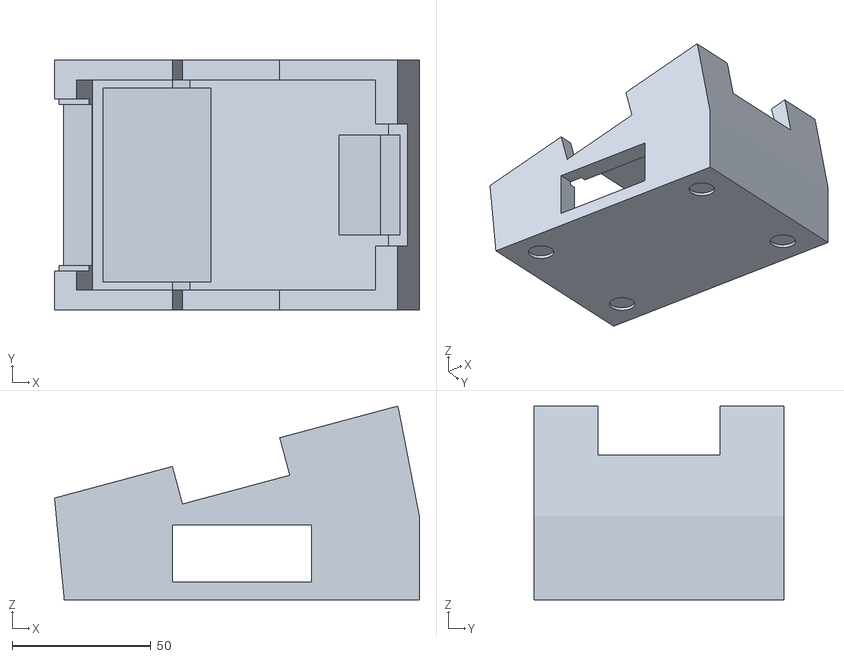
[picture p137: CAD file, 2026-10-01]
hardware/cad/stl/05_accessories/car_dashboard_wedge_dock.stl
131.5 x 90.0 x 69.8
