schmidtmt/openmotorbridge/hardware/kicad_rear_pod3/openmotorbridge_rear_pod3_board.step

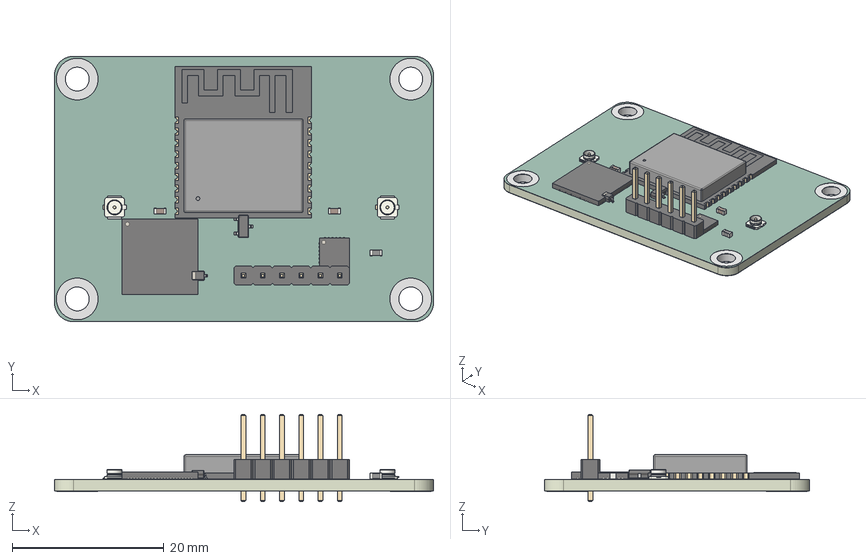
[picture p139: CAD file, 2026-08-24]
hardware/kicad_rear_pod3/openmotorbridge_rear_pod3_board.step
50.0 x 35.0 x 11.5 mm
ESP32-C3-WROOM-02
L_0603_1608Metric
U.FL_Hirose_U.FL-R-SMT-1_Vertical x 2
C_0603_1608Metric x 3
ArtInChip_QFN-88-1EP_10x10mm_P0.4mm_EP6.74x6.74mm
SOT-23
D_SOD-323
C_0805_2012Metric
QFN-24-1EP_4x4mm_Pitch0.5mm
PinHeader_1x06_P254mm_Vertical
openmotorbridge_rear_pod3_pad
openmotorbridge_rear_pod3_soldermask x 2
openmotorbridge_rear_pod3_PCB
