schmidtmt/openmotorbridge/hardware/cad/stl/02_pod_base/components/cots_magnetic_frame_clamp.stl

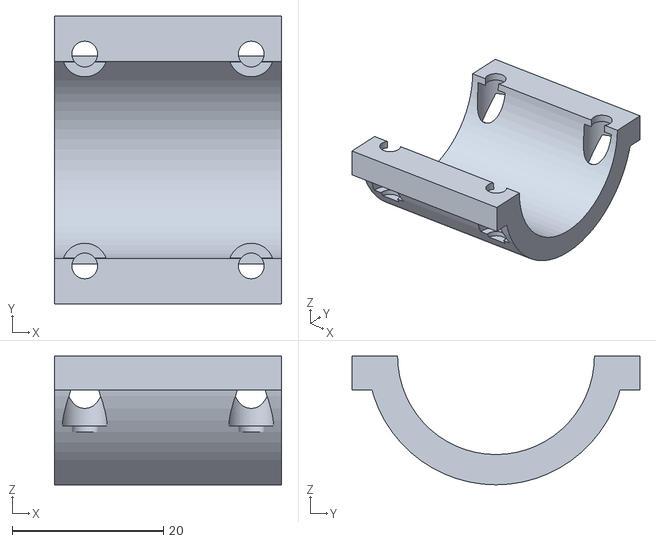
[picture p140: CAD file, 2026-10-09]
hardware/cad/stl/02_pod_base/components/cots_magnetic_frame_clamp.stl
30.0 x 38.0 x 17.0
