schmidtmt/openmotorbridge/hardware/cad/stl/02_pod_base/design_studies/pod3_st_performance_heatsink.stl

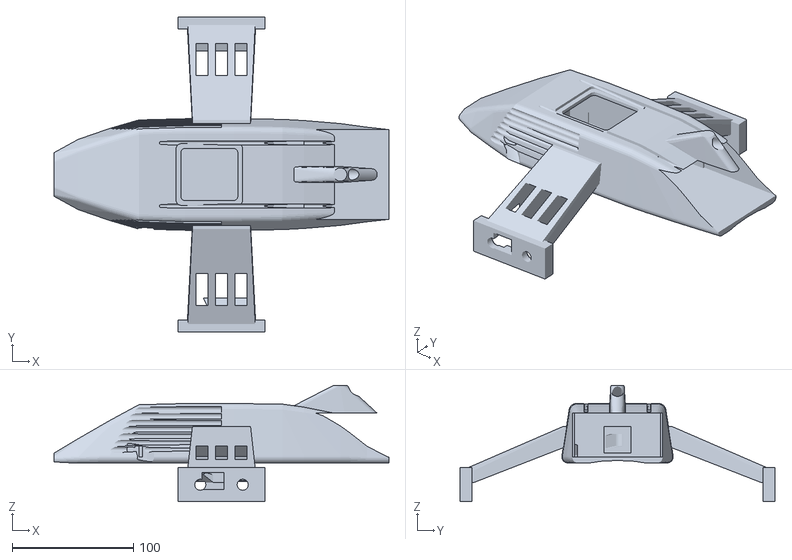
[picture p141: CAD file, 2026-09-05]
hardware/cad/stl/02_pod_base/design_studies/pod3_st_performance_heatsink.stl
276.4 x 260.0 x 96.0
