schmidtmt/openmotorbridge/hardware/cad/stl/02_pod_base/radar_license_plate_bracket.stl

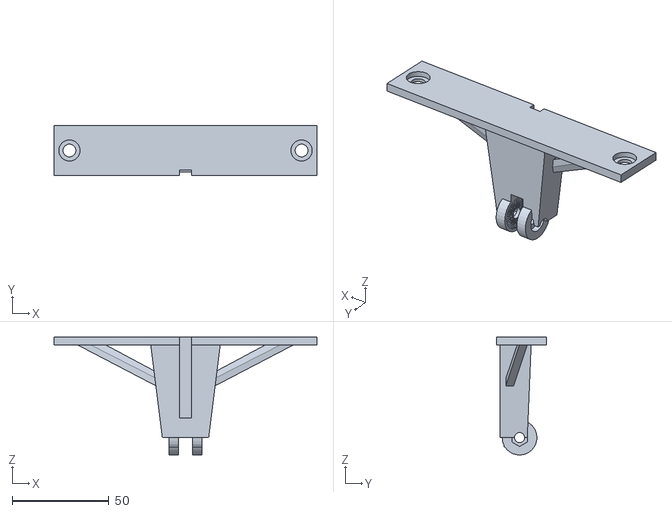
[picture p142: CAD file, 2026-10-01]
hardware/cad/stl/02_pod_base/radar_license_plate_bracket.stl
136.0 x 26.0 x 61.0
