schmidtmt/openmotorbridge/hardware/cad/stl/03_pod_cartridges/omm_ucs_silicone_keypad.stl

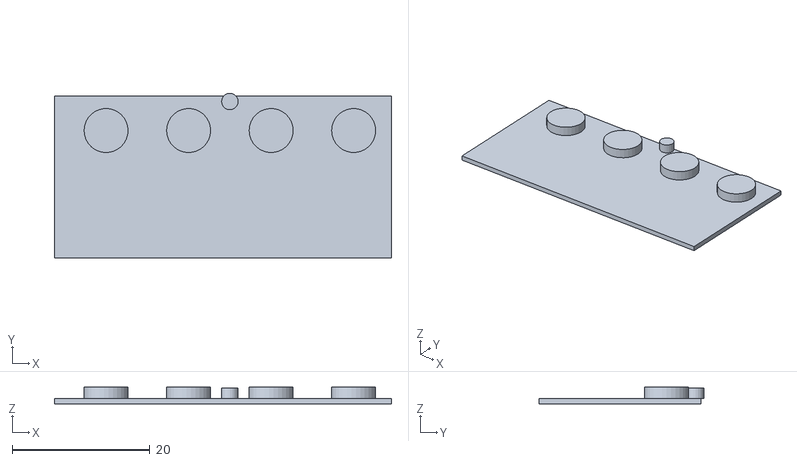
[picture p143: CAD file, 2026-10-09]
hardware/cad/stl/03_pod_cartridges/omm_ucs_silicone_keypad.stl
49.0 x 23.9 x 2.40
