schmidtmt/openmotorbridge/hardware/cad/stl/04_front_node/components/03_mounting_ears.stl

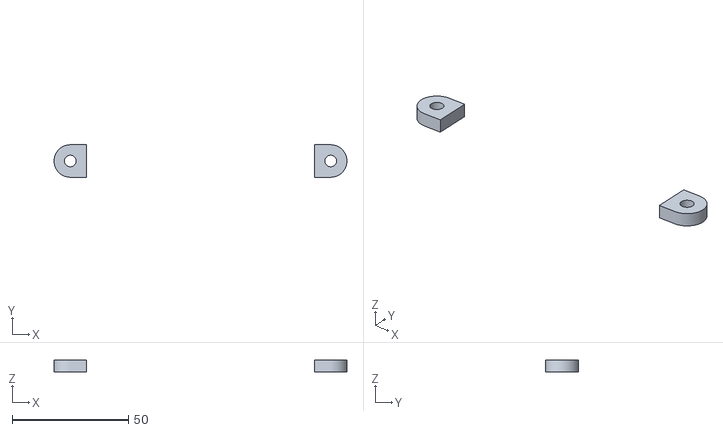
[picture p144: CAD file, 2026-09-13]
hardware/cad/stl/04_front_node/components/03_mounting_ears.stl
126.0 x 14.0 x 5.00
