schmidtmt/openmotorbridge/hardware/cad/stl/04_front_node/front_node_lower_tub.stl

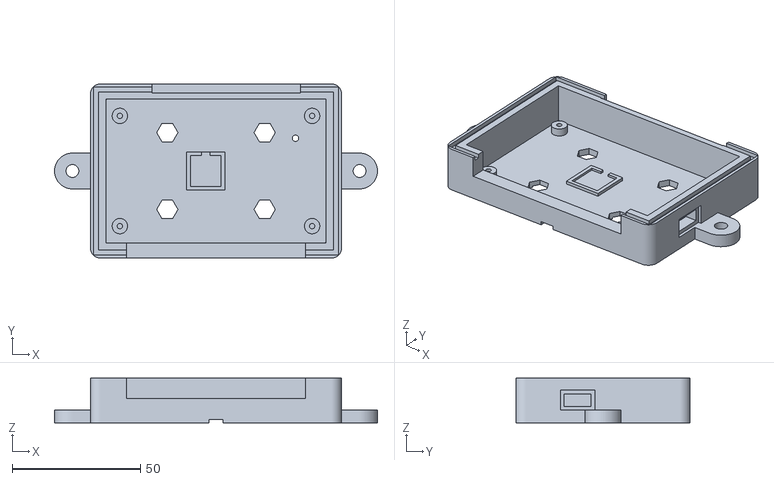
[picture p145: CAD file, 2026-10-09]
hardware/cad/stl/04_front_node/front_node_lower_tub.stl
126.0 x 68.0 x 17.5
