schmidtmt/openmotorbridge/hardware/cad/stl/05_accessories/radar_mr20_radome.stl

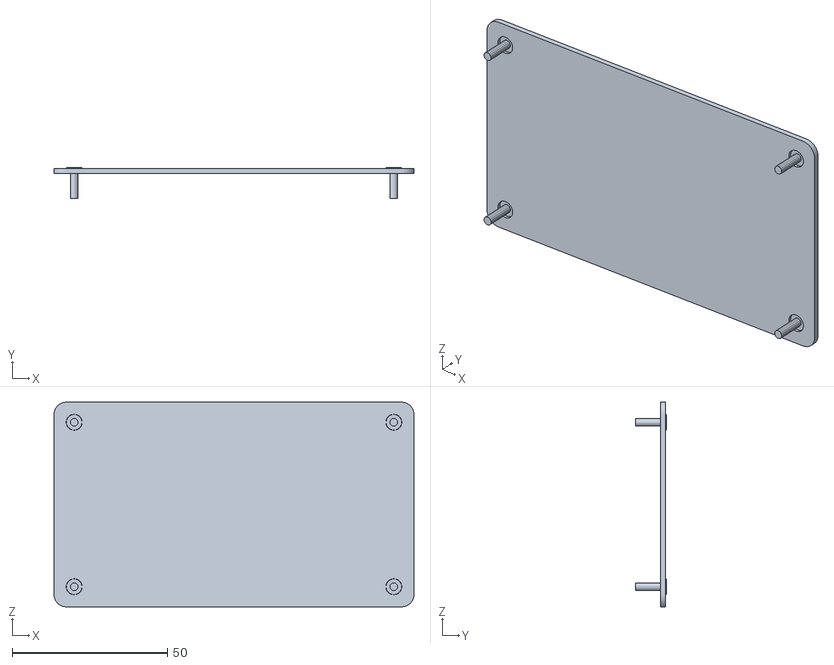
[picture p146: CAD file, 2026-10-01]
hardware/cad/stl/05_accessories/radar_mr20_radome.stl
116.0 x 10.00 x 66.0
