schmidtmt/openmotorbridge/hardware/cad/stl/02_pod_base/components/03_pod_bulkhead_partition.stl

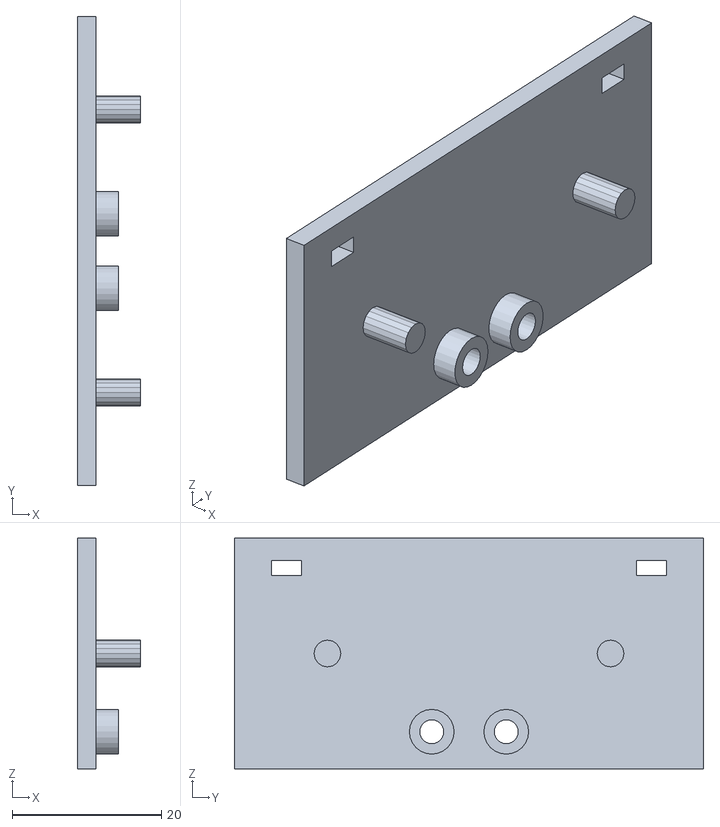
[picture p147: CAD file, 2026-10-01]
hardware/cad/stl/02_pod_base/components/03_pod_bulkhead_partition.stl
8.50 x 63.0 x 31.0
