schmidtmt/openmotorbridge/hardware/cad/stl/02_pod_base/design_studies/pod3_st_aero_winglet_football_ascii.stl

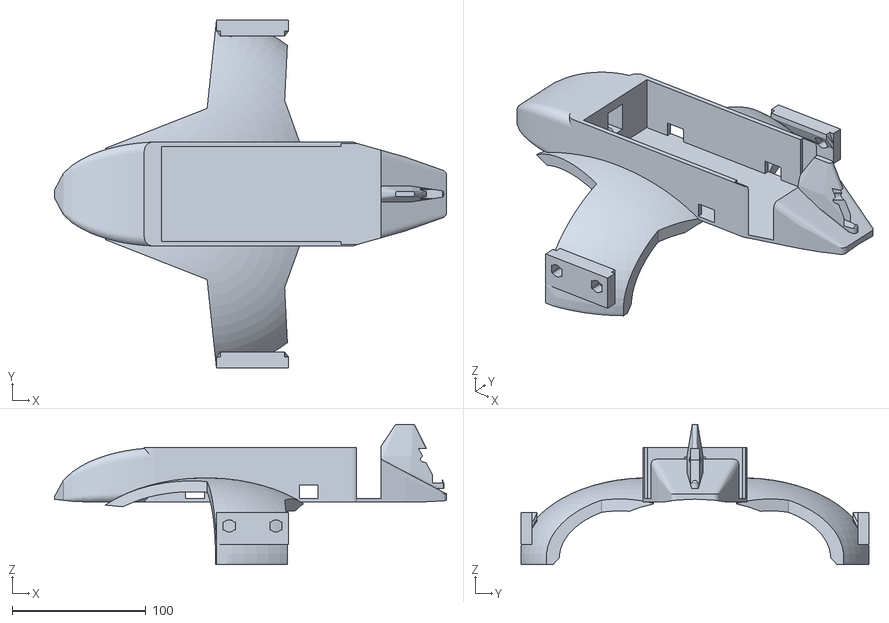
[picture p148: CAD file, 2026-09-05]
hardware/cad/stl/02_pod_base/design_studies/pod3_st_aero_winglet_football_ascii.stl
293.1 x 260.0 x 105.0
