schmidtmt/openmotorbridge/hardware/cad/stl/02_pod_base/saddlebag_lid_dock.stl

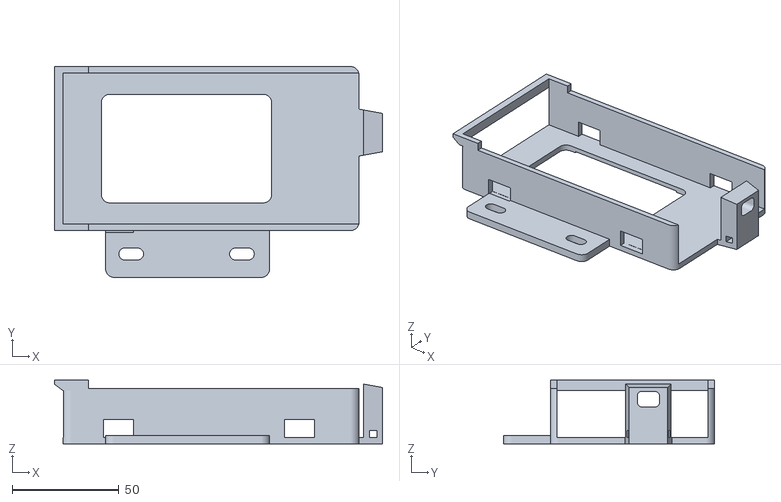
[picture p149: CAD file, 2026-10-01]
hardware/cad/stl/02_pod_base/saddlebag_lid_dock.stl
154.0 x 99.0 x 30.0
