schmidtmt/openmotorbridge/hardware/cad/stl/03_pod_cartridges/cartridge_universal_actuator_rails.stl

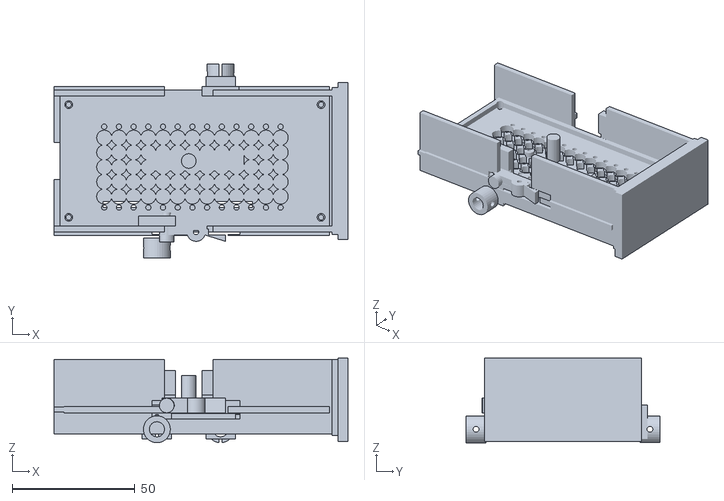
[picture p150: CAD file, 2026-10-01]
hardware/cad/stl/03_pod_cartridges/cartridge_universal_actuator_rails.stl
120.0 x 79.0 x 34.5
