schmidtmt/openmotorbridge/hardware/cad/stl/04_front_node/components/01_front_node_base_tub.stl

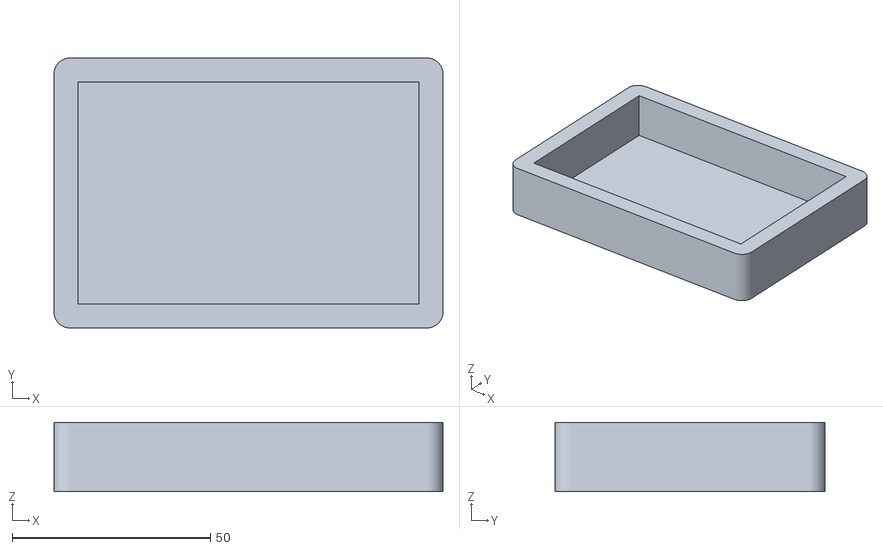
[picture p151: CAD file, 2026-09-13]
hardware/cad/stl/04_front_node/components/01_front_node_base_tub.stl
98.0 x 68.0 x 17.5
