schmidtmt/openmotorbridge/hardware/cad/stl/04_front_node/front_node_fairing_tube_clamp_cap.stl

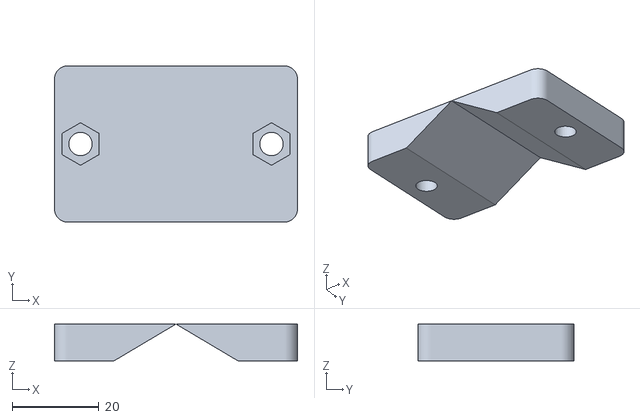
[picture p152: CAD file, 2026-10-09]
hardware/cad/stl/04_front_node/front_node_fairing_tube_clamp_cap.stl
56.0 x 36.0 x 8.50
