schmidtmt/openmotorbridge/hardware/cad/stl/05_accessories/radar_mr20_housing.stl

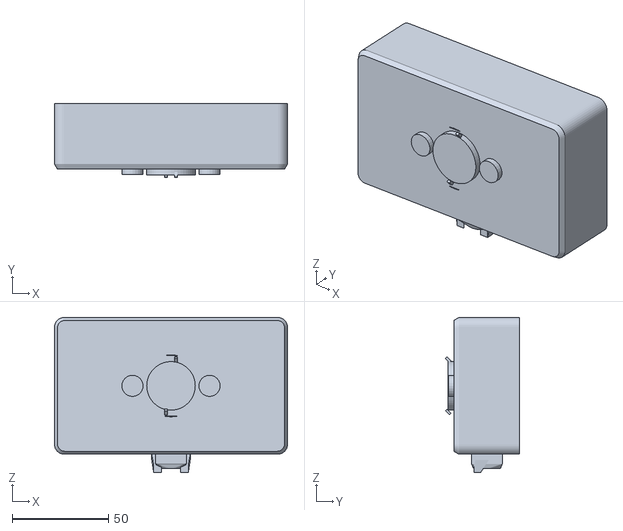
[picture p153: CAD file, 2026-10-01]
hardware/cad/stl/05_accessories/radar_mr20_housing.stl
121.0 x 38.6 x 80.5
