schmidtmt/openmotorbridge/hardware/cad/stl/01_main_box/components/07_mid_partition_floor.stl

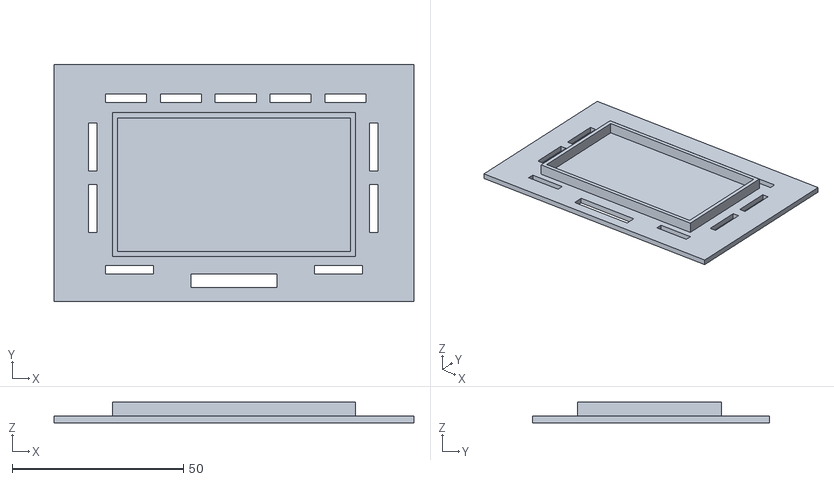
[picture p154: CAD file, 2026-09-15]
hardware/cad/stl/01_main_box/components/07_mid_partition_floor.stl
105.0 x 69.0 x 6.00
