schmidtmt/openmotorbridge/hardware/cad/stl/02_pod_base/components/010_saddlebag_hole_grommet_split.stl

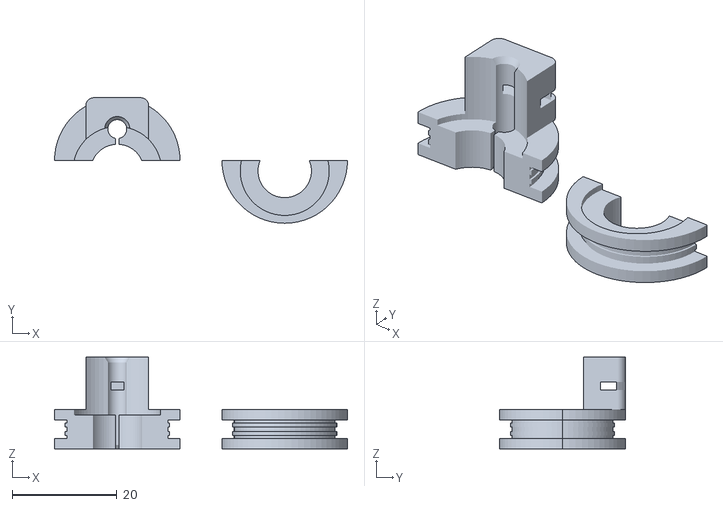
[picture p156: CAD file, 2026-10-01]
hardware/cad/stl/02_pod_base/components/010_saddlebag_hole_grommet_split.stl
56.0 x 24.0 x 17.5
