schmidtmt/openmotorbridge/hardware/cad/stl/02_pod_base/design_studies/pod3_st_performance_hybrid_wing_covers.stl

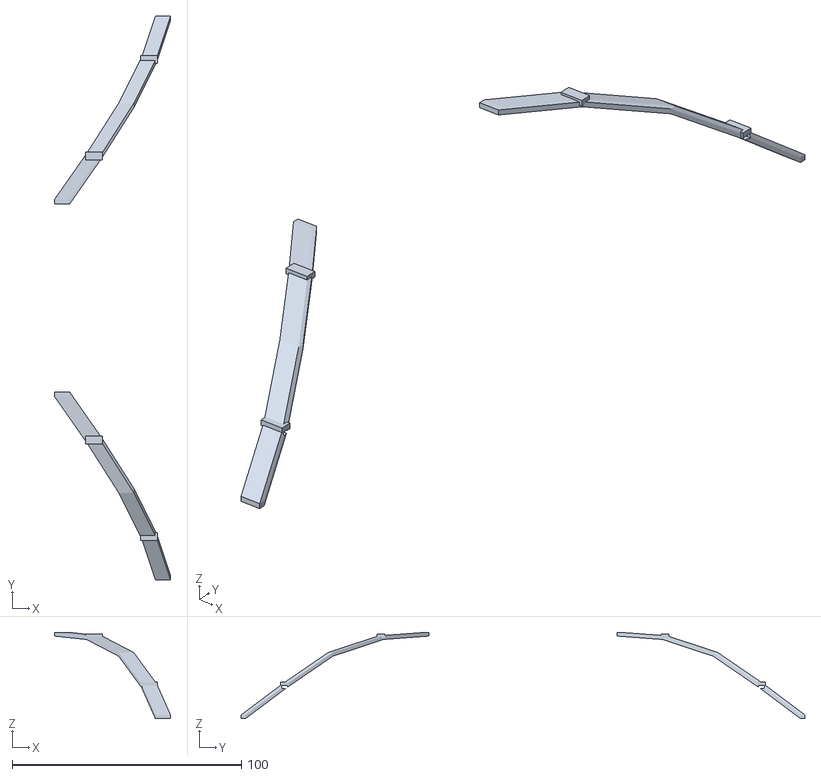
[picture p157: CAD file, 2026-09-05]
hardware/cad/stl/02_pod_base/design_studies/pod3_st_performance_hybrid_wing_covers.stl
50.6 x 246.0 x 37.6
