schmidtmt/openmotorbridge/hardware/cad/stl/03_pod_cartridges/cartridge_antenna_bracket_omm.stl

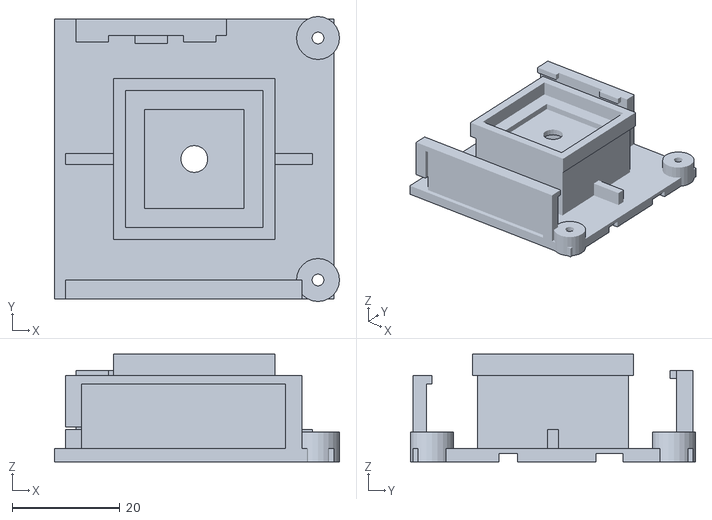
[picture p158: CAD file, 2026-10-01]
hardware/cad/stl/03_pod_cartridges/cartridge_antenna_bracket_omm.stl
53.0 x 53.0 x 20.0
