schmidtmt/openmotorbridge/hardware/cad/stl/04_front_node/front_node_cable_glands_tpu.stl

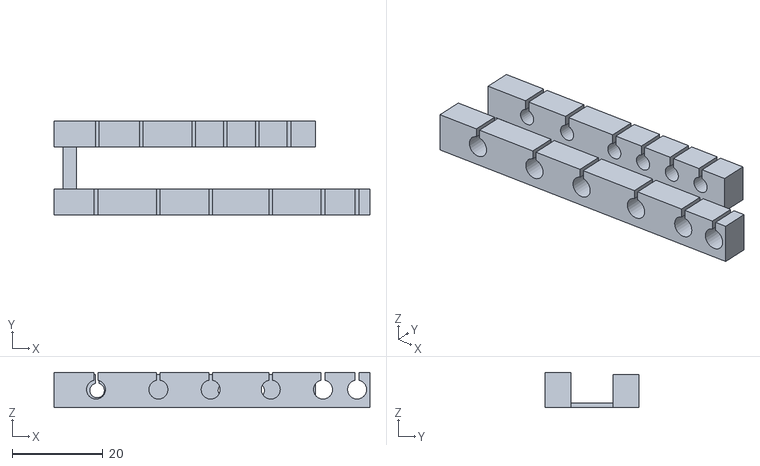
[picture p159: CAD file, 2026-09-13]
hardware/cad/stl/04_front_node/front_node_cable_glands_tpu.stl
69.6 x 20.7 x 7.80
