schmidtmt/openmotorbridge/hardware/cad/stl/05_accessories/car_sun_visor_pod3_clip.stl

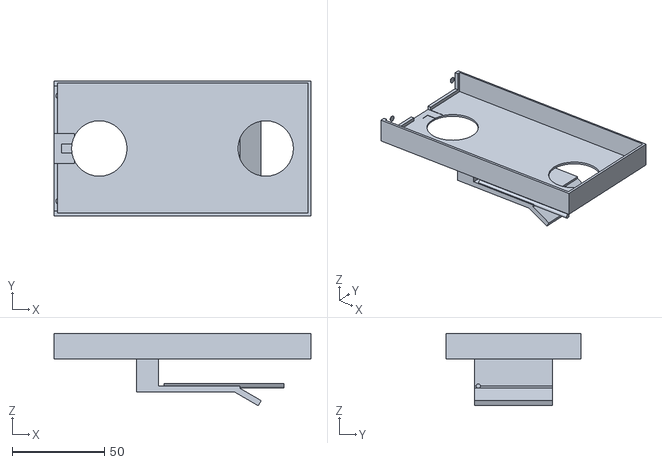
[picture p160: CAD file, 2026-10-01]
hardware/cad/stl/05_accessories/car_sun_visor_pod3_clip.stl
139.0 x 73.0 x 39.2
