schmidtmt/openmotorbridge/hardware/cad/stl/01_main_box/components/dummy_lipo_battery.stl

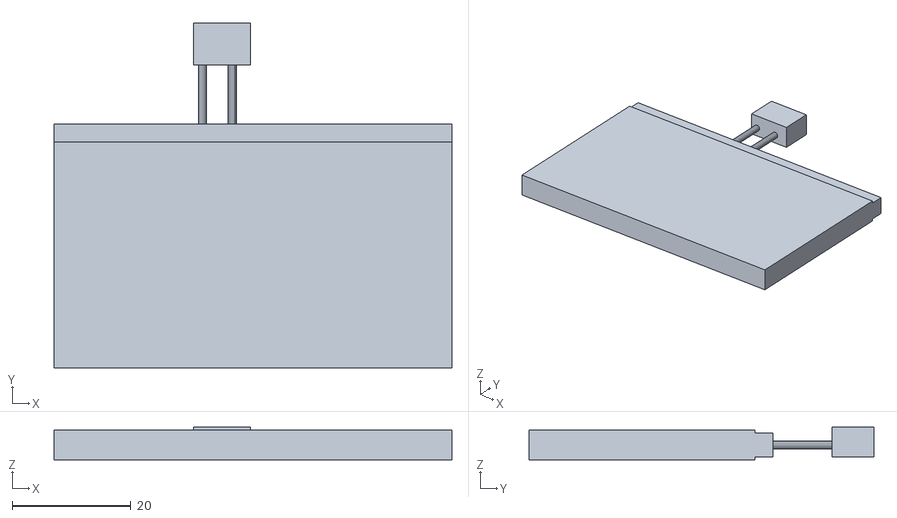
[picture p161: CAD file, 2026-09-15]
hardware/cad/stl/01_main_box/components/dummy_lipo_battery.stl
67.0 x 58.0 x 5.50
