schmidtmt/openmotorbridge/hardware/cad/stl/02_pod_base/components/009_magsafe_frame_dock.stl

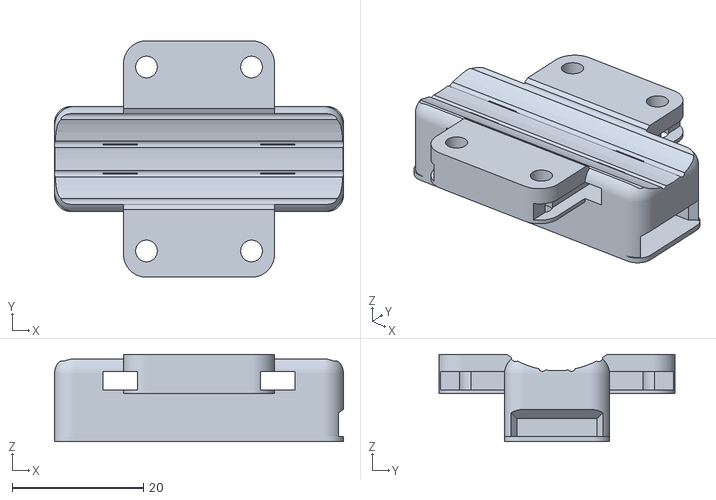
[picture p162: CAD file, 2026-09-16]
hardware/cad/stl/02_pod_base/components/009_magsafe_frame_dock.stl
44.0 x 36.0 x 13.3
