schmidtmt/openmotorbridge/hardware/cad/stl/02_pod_base/design_studies/pod3_st_f117_stealth_nacelle.stl

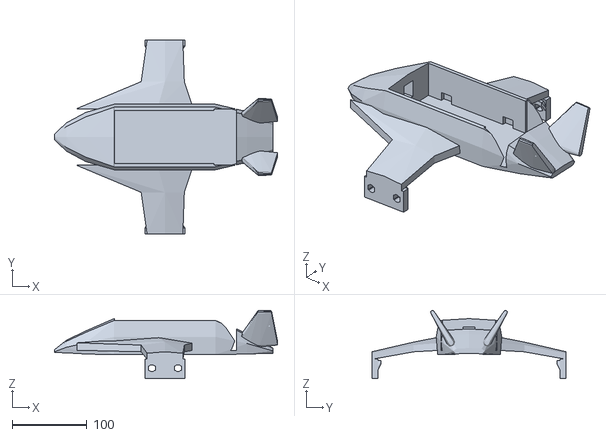
[picture p163: CAD file, 2026-09-05]
hardware/cad/stl/02_pod_base/design_studies/pod3_st_f117_stealth_nacelle.stl
299.2 x 260.5 x 91.5
