schmidtmt/openmotorbridge/hardware/cad/stl/02_pod_base/pod3_touring_fender_console.stl

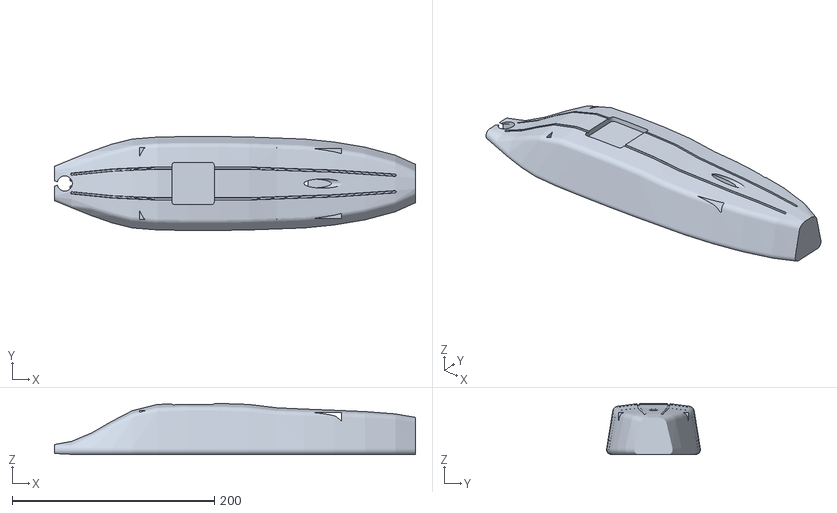
[picture p164: CAD file, 2026-10-01]
hardware/cad/stl/02_pod_base/pod3_touring_fender_console.stl
357.4 x 93.0 x 50.7
