schmidtmt/openmotorbridge/hardware/cad/stl/03_pod_cartridges/cartridge_base_sled.stl

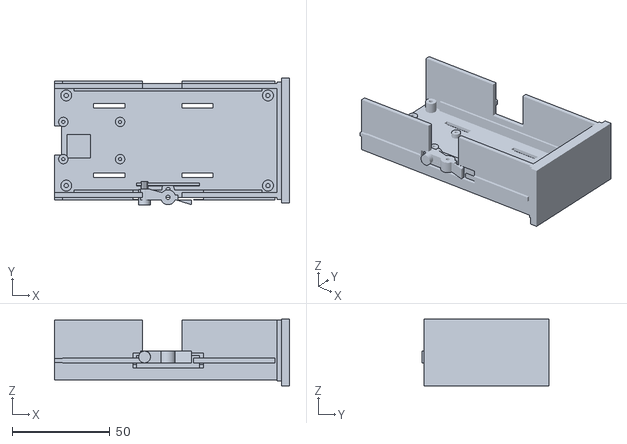
[picture p165: CAD file, 2026-10-01]
hardware/cad/stl/03_pod_cartridges/cartridge_base_sled.stl
120.0 x 65.0 x 34.0
