schmidtmt/openmotorbridge/hardware/cad/stl/04_front_node/front_node_upper_lid.stl

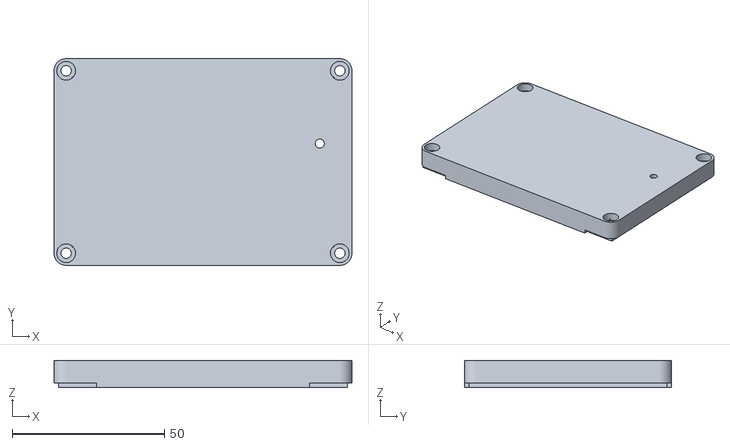
[picture p166: CAD file, 2026-09-13]
hardware/cad/stl/04_front_node/front_node_upper_lid.stl
98.0 x 68.0 x 9.00
