schmidtmt/openmotorbridge/hardware/cad/stl/05_accessories/road_glide_inductive_cam_dock.stl

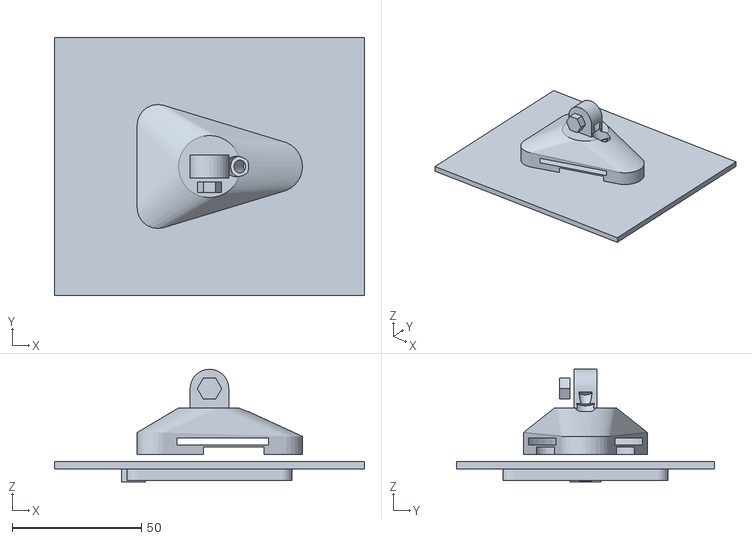
[picture p167: CAD file, 2026-09-23]
hardware/cad/stl/05_accessories/road_glide_inductive_cam_dock.stl
120.0 x 100.0 x 43.6
