schmidtmt/openmotorbridge/hardware/cad/stl/01_main_box/components/05_sealing_groove.stl

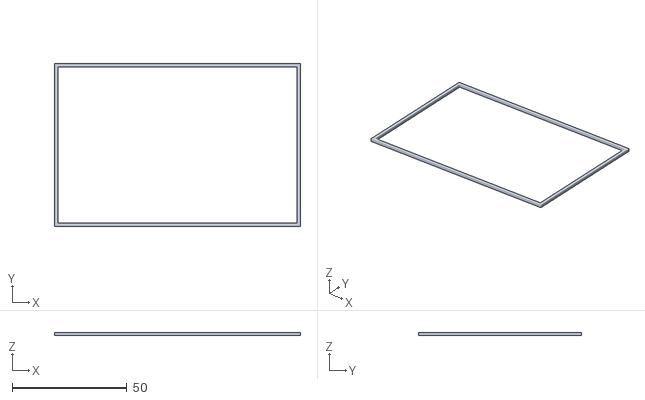
[picture p168: CAD file, 2026-09-06]
hardware/cad/stl/01_main_box/components/05_sealing_groove.stl
107.2 x 71.2 x 1.50
