schmidtmt/openmotorbridge/hardware/cad/stl/02_pod_base/adventure_gsa_clamp_cap.stl

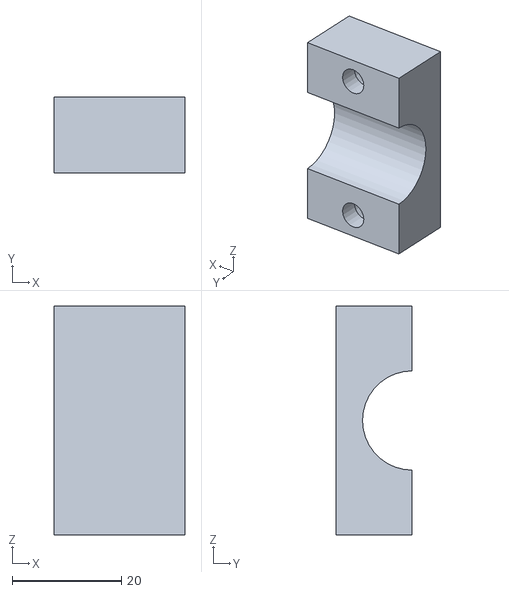
[picture p169: CAD file, 2026-10-01]
hardware/cad/stl/02_pod_base/adventure_gsa_clamp_cap.stl
24.0 x 14.0 x 42.0
