schmidtmt/openmotorbridge/hardware/cad/stl/02_pod_base/components/011_gopro_hirth_lock.stl

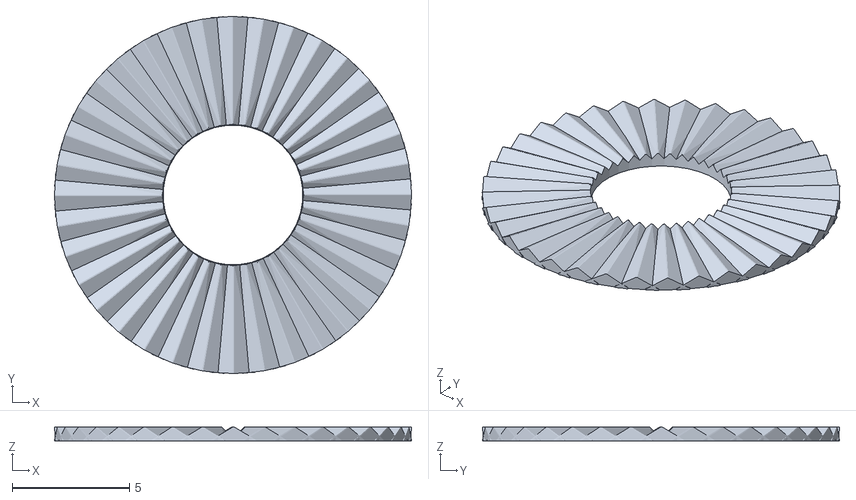
[picture p170: CAD file, 2026-09-10]
hardware/cad/stl/02_pod_base/components/011_gopro_hirth_lock.stl
15.2 x 15.2 x 0.6
