schmidtmt/openmotorbridge/hardware/cad/stl/02_pod_base/design_studies/pod3_st_performance_hybrid_cradle.stl

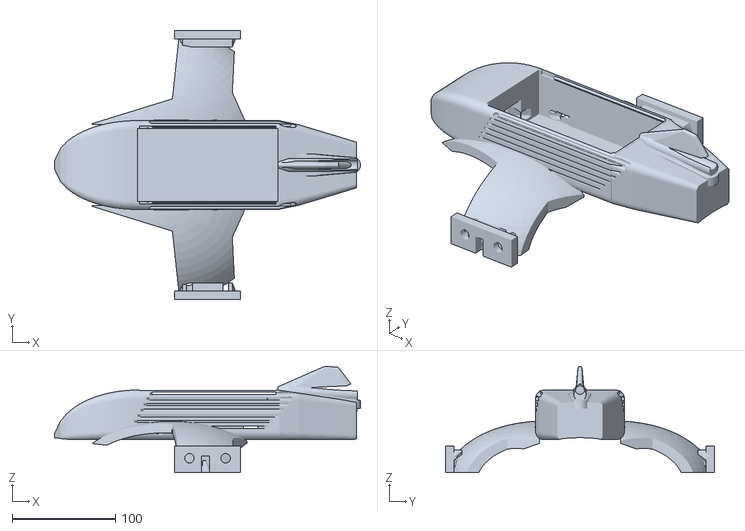
[picture p171: CAD file, 2026-09-05]
hardware/cad/stl/02_pod_base/design_studies/pod3_st_performance_hybrid_cradle.stl
296.1 x 260.0 x 103.0
