schmidtmt/openmotorbridge/hardware/cad/stl/03_pod_cartridges/cartridge_insert_omm_ucs.stl

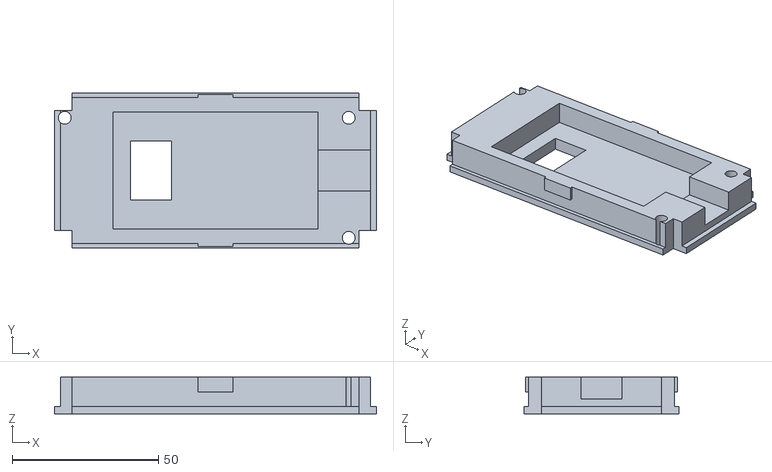
[picture p172: CAD file, 2026-10-01]
hardware/cad/stl/03_pod_cartridges/cartridge_insert_omm_ucs.stl
110.0 x 53.0 x 12.5
