schmidtmt/openmotorbridge/hardware/cad/stl/04_front_node/front_node_usbc_cap_tpu.stl

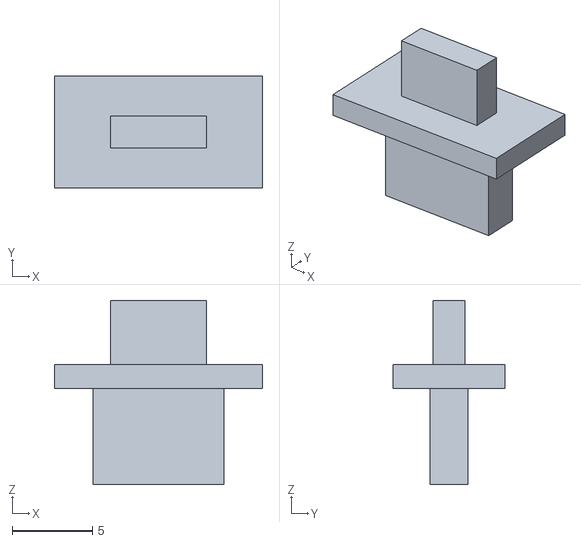
[picture p173: CAD file, 2026-09-06]
hardware/cad/stl/04_front_node/front_node_usbc_cap_tpu.stl
13.0 x 7.00 x 11.5
