schmidtmt/openmotorbridge/hardware/cad/stl/05_accessories/bsd_mirror_lower_clamp.stl

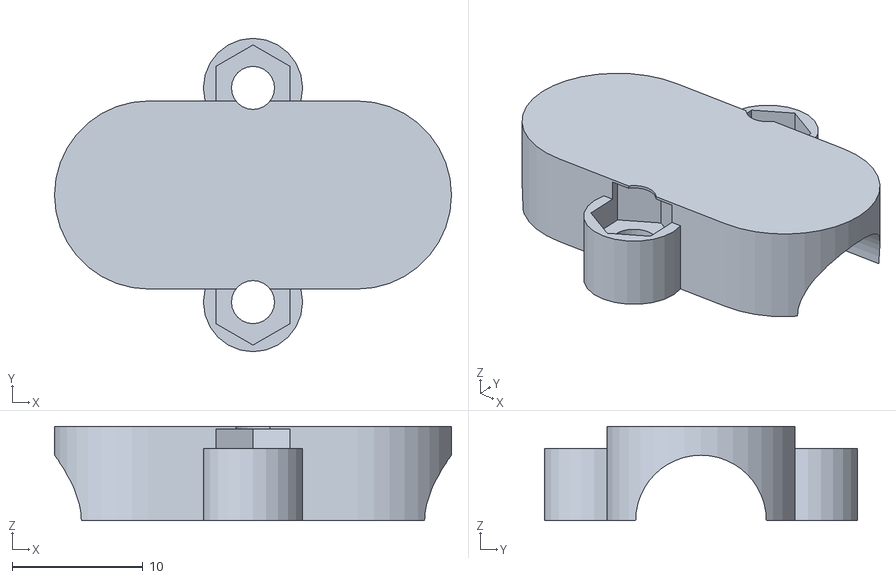
[picture p174: CAD file, 2026-09-17]
hardware/cad/stl/05_accessories/bsd_mirror_lower_clamp.stl
30.4 x 24.0 x 7.20
