schmidtmt/openmotorbridge/hardware/cad/stl/01_main_box/components/01_lower_tub_empty.stl

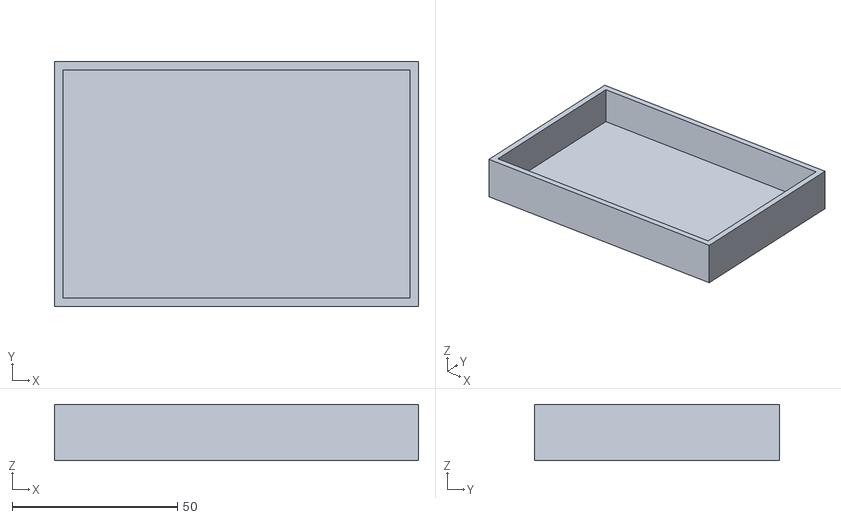
[picture p175: CAD file, 2026-09-06]
hardware/cad/stl/01_main_box/components/01_lower_tub_empty.stl
110.0 x 74.0 x 17.0
