schmidtmt/openmotorbridge/hardware/cad/stl/02_pod_base/components/06_fender_curved_saddle.stl

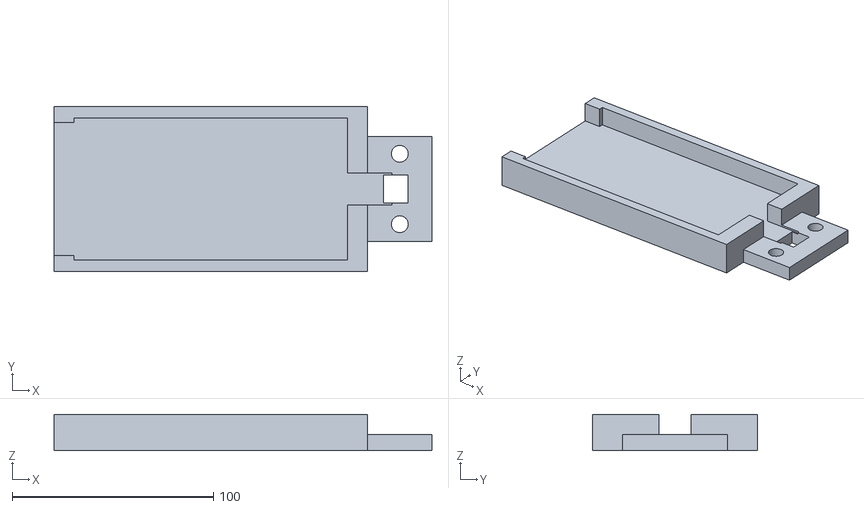
[picture p176: CAD file, 2026-09-06]
hardware/cad/stl/02_pod_base/components/06_fender_curved_saddle.stl
188.0 x 82.0 x 18.0
