schmidtmt/openmotorbridge/hardware/cad/stl/02_pod_base/radar_swivel_tilt_cradle.stl

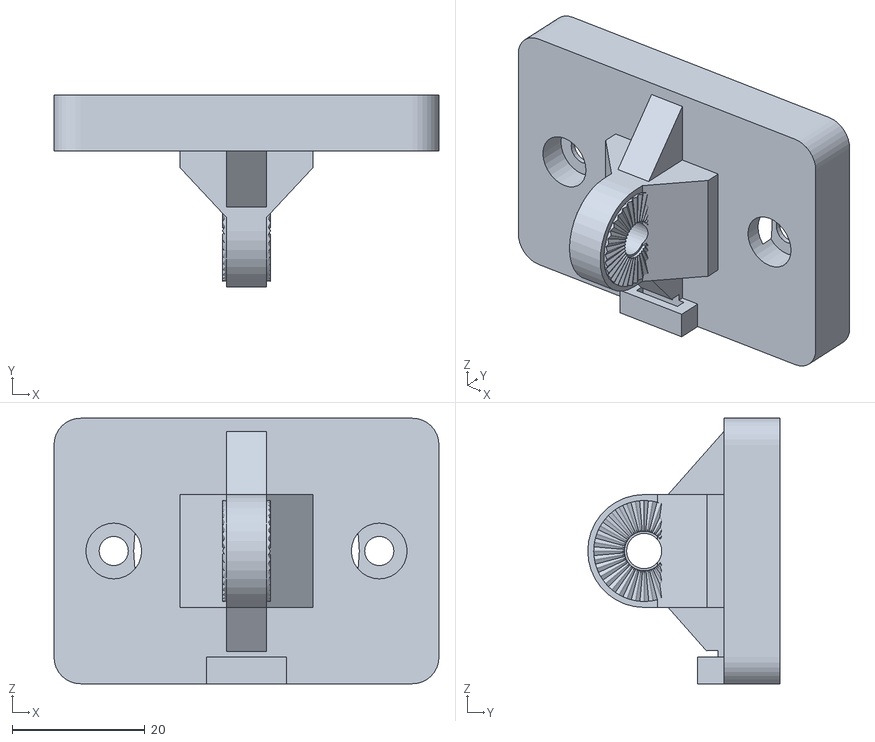
[picture p177: CAD file, 2026-10-01]
hardware/cad/stl/02_pod_base/radar_swivel_tilt_cradle.stl
58.0 x 29.0 x 40.0
