schmidtmt/openmotorbridge/hardware/cad/stl/03_pod_cartridges/cartridge_magnetic_lock_latch.stl

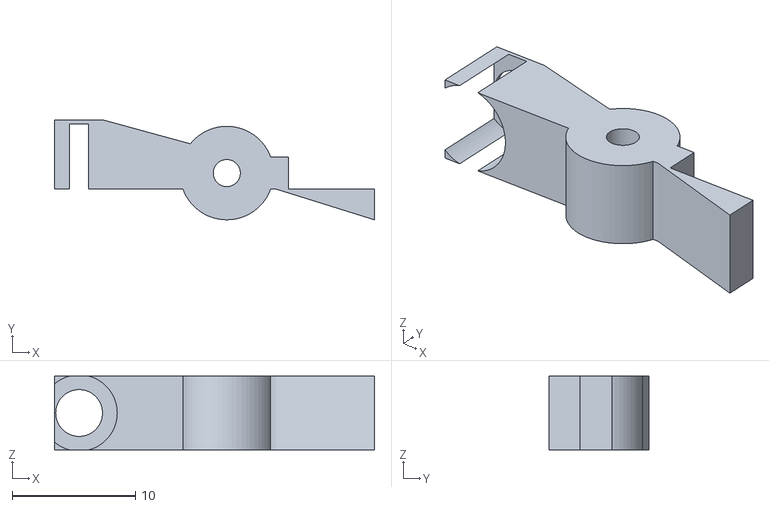
[picture p178: CAD file, 2026-09-10]
hardware/cad/stl/03_pod_cartridges/cartridge_magnetic_lock_latch.stl
26.0 x 8.10 x 6.00
