schmidtmt/openmotorbridge/hardware/cad/stl/05_accessories/under_perch_mirror_plate.stl

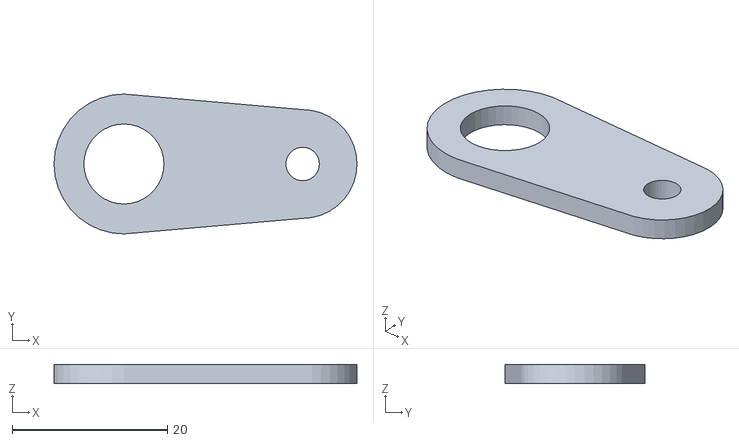
[picture p179: CAD file, 2026-09-17]
hardware/cad/stl/05_accessories/under_perch_mirror_plate.stl
39.0 x 18.0 x 2.50
