schmidtmt/openmotorbridge/hardware/cad/stl/01_main_box/components/06_mid_tray_frame.stl

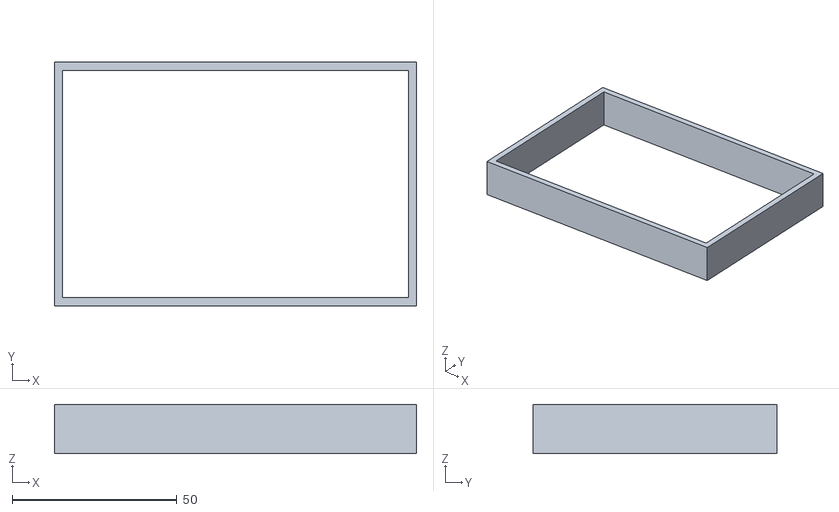
[picture p180: CAD file, 2026-09-06]
hardware/cad/stl/01_main_box/components/06_mid_tray_frame.stl
110.0 x 74.0 x 15.0
