schmidtmt/openmotorbridge/hardware/cad/stl/02_pod_base/adventure_transition_dock_base.stl

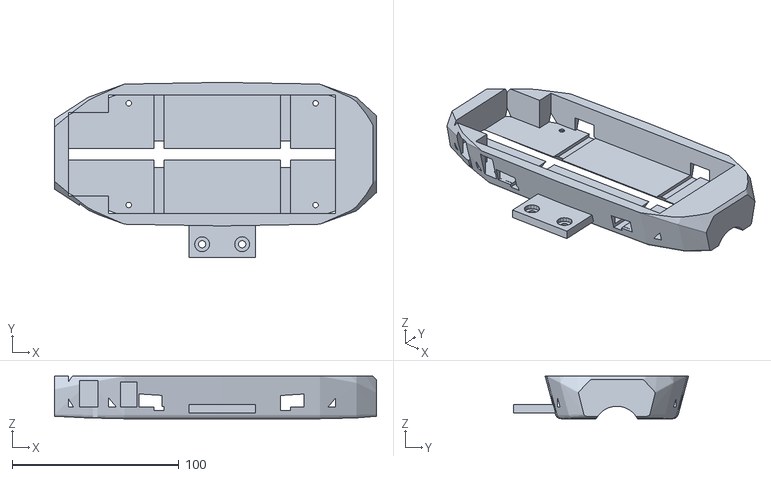
[picture p181: CAD file, 2026-10-01]
hardware/cad/stl/02_pod_base/adventure_transition_dock_base.stl
193.0 x 105.0 x 25.5
