schmidtmt/openmotorbridge/hardware/cad/stl/02_pod_base/components/009_magsafe_frame_clamp.stl

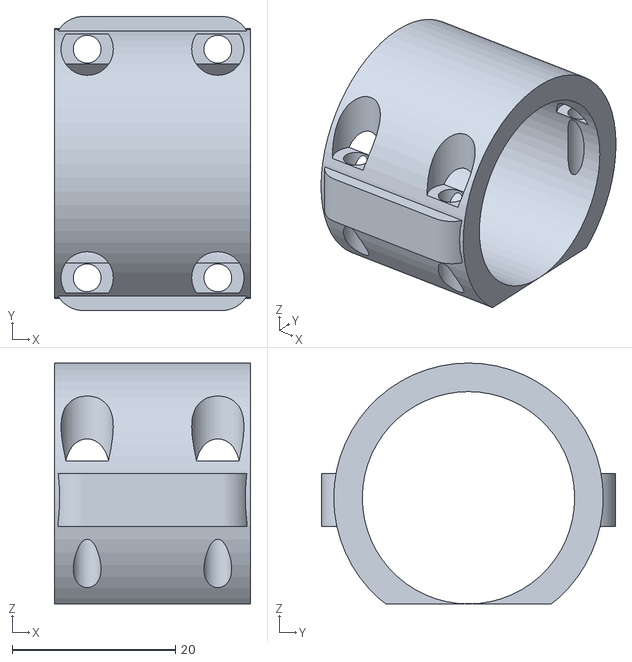
[picture p182: CAD file, 2026-09-06]
hardware/cad/stl/02_pod_base/components/009_magsafe_frame_clamp.stl
24.0 x 36.0 x 29.5
