schmidtmt/openmotorbridge/hardware/cad/stl/03_pod_cartridges/cartridge_insert_cardo.stl

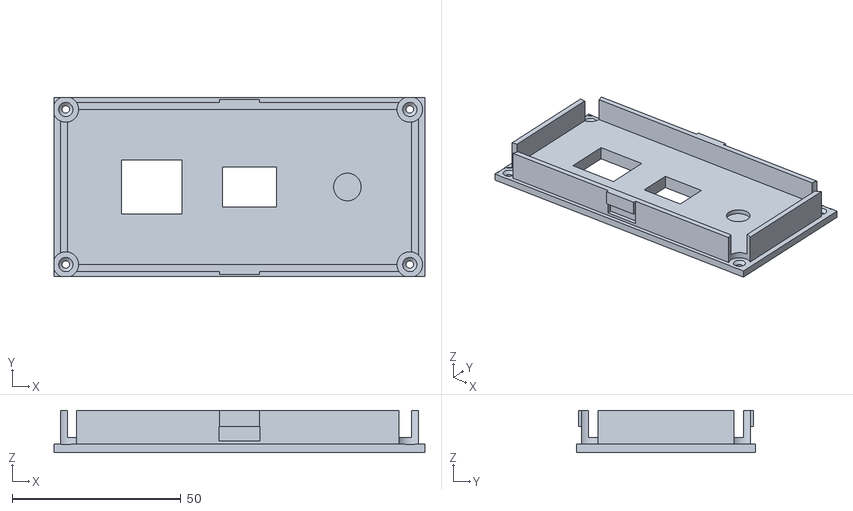
[picture p183: CAD file, 2026-09-06]
hardware/cad/stl/03_pod_cartridges/cartridge_insert_cardo.stl
110.0 x 53.0 x 12.5
