schmidtmt/openmotorbridge/hardware/cad/stl/05_accessories/under_perch_switch_bracket.stl

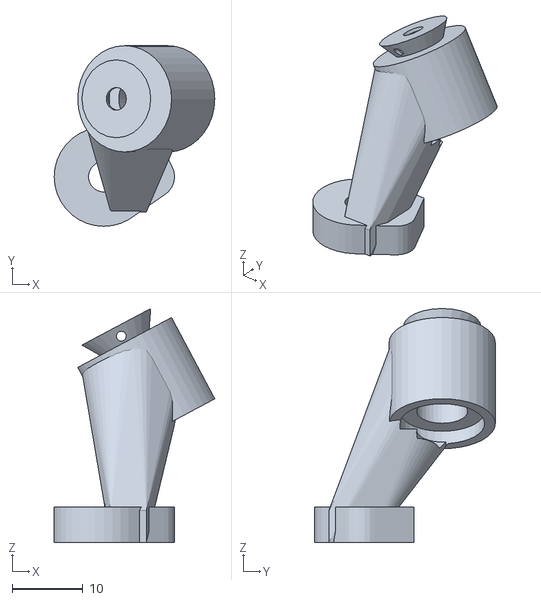
[picture p184: CAD file, 2026-09-17]
hardware/cad/stl/05_accessories/under_perch_switch_bracket.stl
22.7 x 25.5 x 33.0
