schmidtmt/openmotorbridge/hardware/cad/stl/01_main_box/components/04_mounting_ears.stl

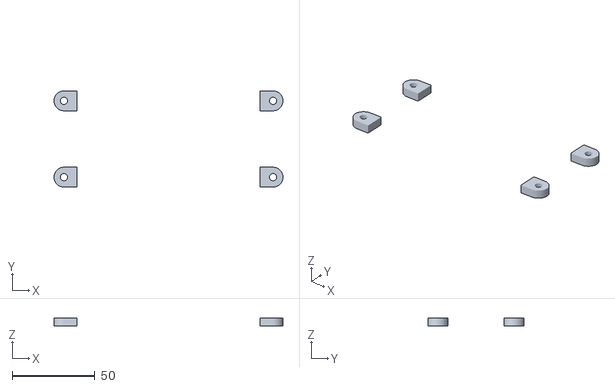
[picture p185: CAD file, 2026-09-06]
hardware/cad/stl/01_main_box/components/04_mounting_ears.stl
138.0 x 58.0 x 5.00
