schmidtmt/openmotorbridge/hardware/cad/stl/02_pod_base/adventure_rack_radar_clamp_cap.stl

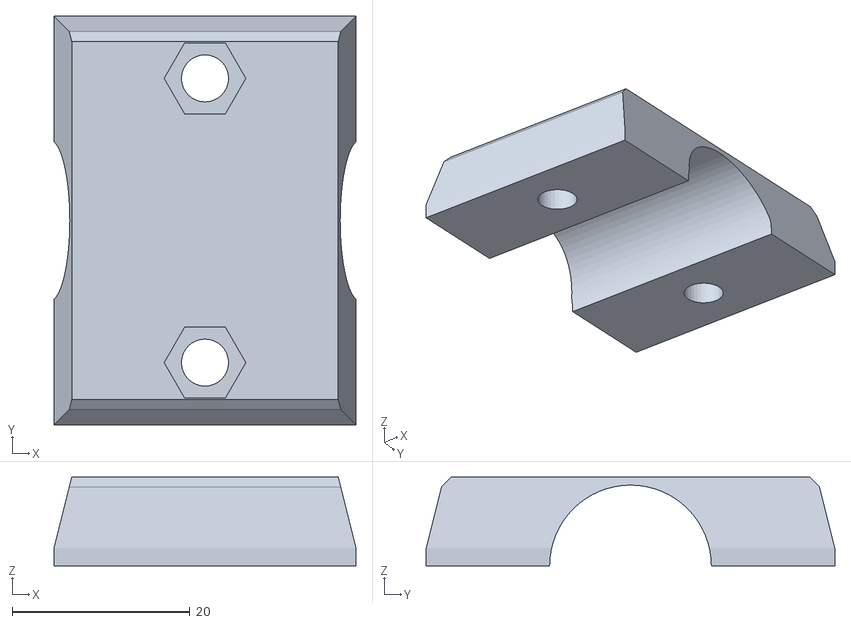
[picture p186: CAD file, 2026-10-01]
hardware/cad/stl/02_pod_base/adventure_rack_radar_clamp_cap.stl
34.0 x 46.0 x 10.0
