schmidtmt/openmotorbridge/hardware/cad/stl/02_pod_base/components/07_pod_slide_dock_core.stl

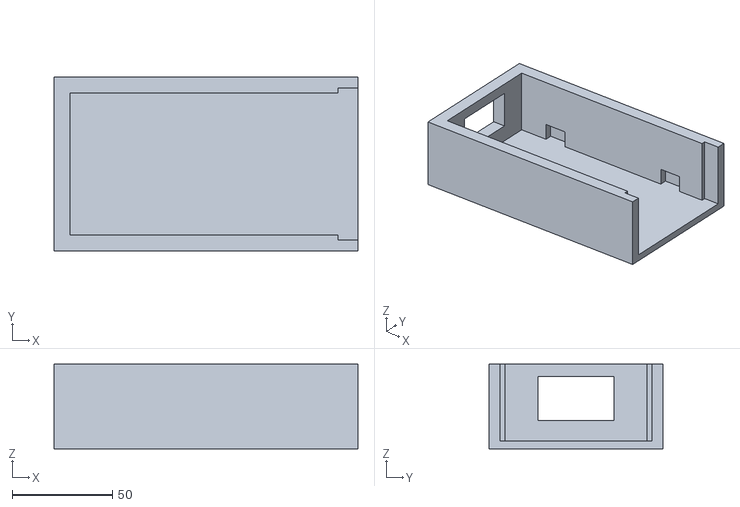
[picture p187: CAD file, 2026-09-06]
hardware/cad/stl/02_pod_base/components/07_pod_slide_dock_core.stl
151.6 x 86.6 x 42.2
