schmidtmt/openmotorbridge/hardware/cad/stl/03_pod_cartridges/cartridge_insert_blindkassette.stl

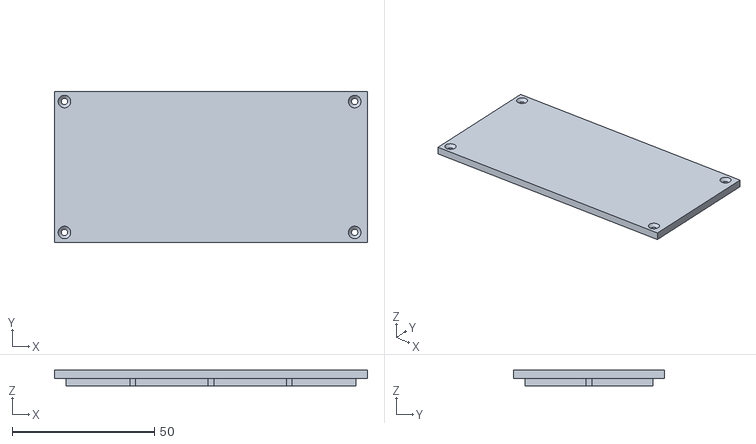
[picture p188: CAD file, 2026-09-06]
hardware/cad/stl/03_pod_cartridges/cartridge_insert_blindkassette.stl
110.0 x 53.0 x 5.50
