schmidtmt/openmotorbridge/hardware/cad/stl/05_accessories/bsd_mirror_upper_pod.stl

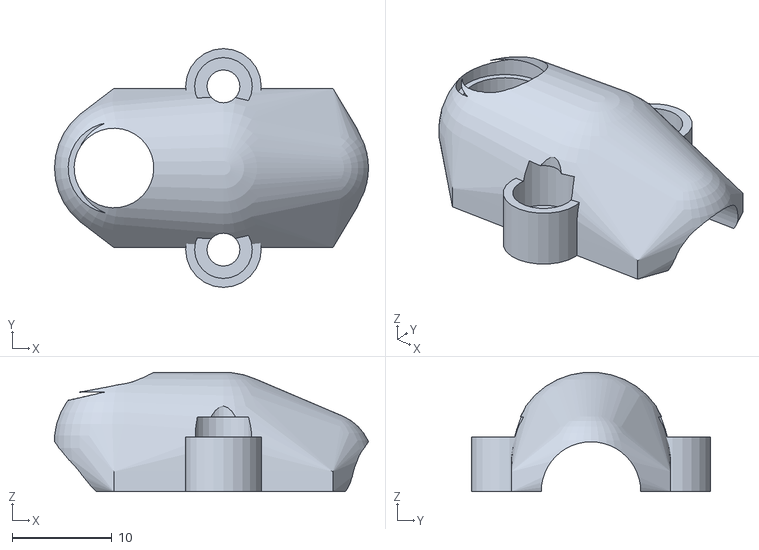
[picture p189: CAD file, 2026-09-17]
hardware/cad/stl/05_accessories/bsd_mirror_upper_pod.stl
31.5 x 24.0 x 12.0
