schmidtmt/openmotorbridge/hardware/cad/stl/02_pod_base/adventure_gsa_cage_dock_body.stl

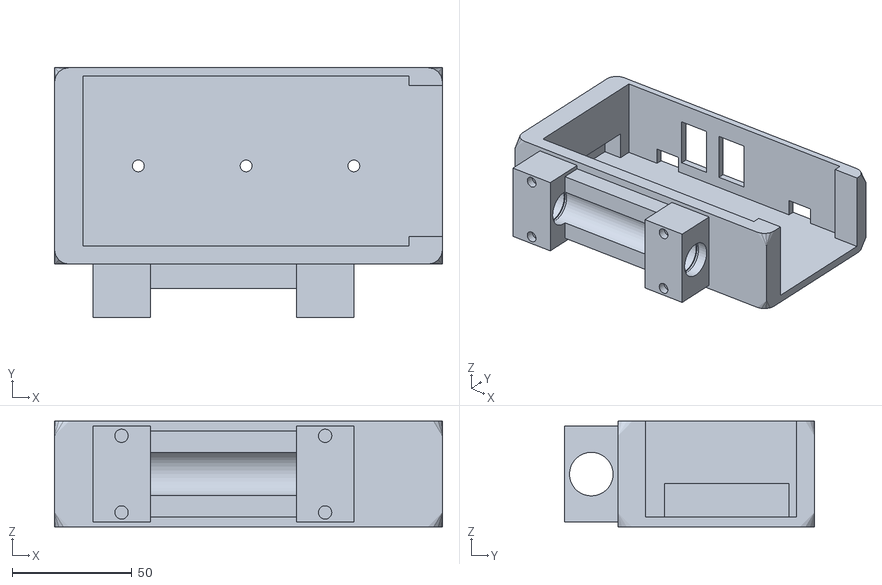
[picture p190: CAD file, 2026-10-01]
hardware/cad/stl/02_pod_base/adventure_gsa_cage_dock_body.stl
162.0 x 104.2 x 44.1
