schmidtmt/openmotorbridge/hardware/cad/stl/02_pod_base/components/dummy_m8_connector.stl

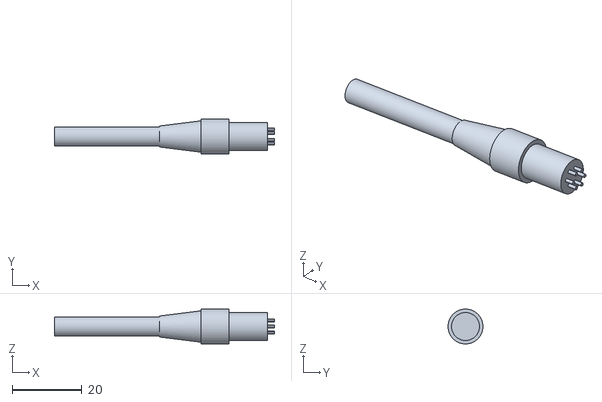
[picture p191: CAD file, 2026-09-06]
hardware/cad/stl/02_pod_base/components/dummy_m8_connector.stl
63.0 x 10.0 x 10.0
