schmidtmt/openmotorbridge/hardware/cad/stl/02_pod_base/design_studies/pod3_st_performance_hybrid_c.stl

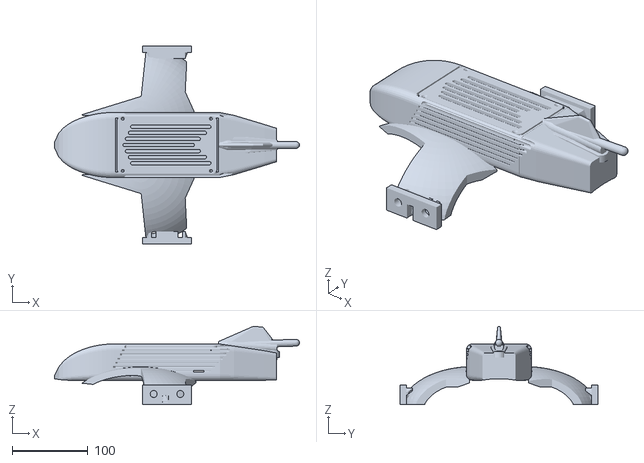
[picture p192: CAD file, 2026-09-05]
hardware/cad/stl/02_pod_base/design_studies/pod3_st_performance_hybrid_c.stl
322.5 x 260.0 x 103.0
