schmidtmt/openmotorbridge/hardware/cad/stl/05_accessories/bsd_mirror_lens.stl

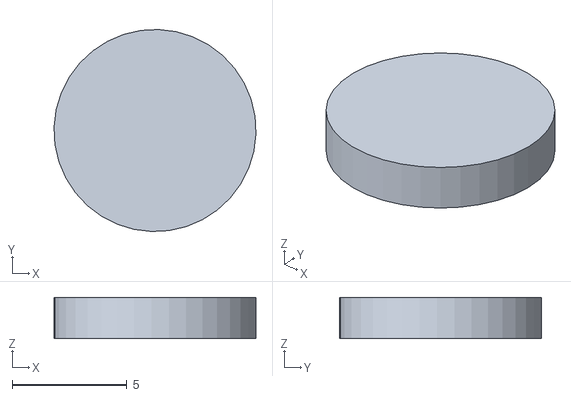
[picture p193: CAD file, 2026-09-17]
hardware/cad/stl/05_accessories/bsd_mirror_lens.stl
8.79 x 8.79 x 1.80
