schmidtmt/openmotorbridge/hardware/cad/stl/02_pod_base/components/01_pod_tunnel_base.stl

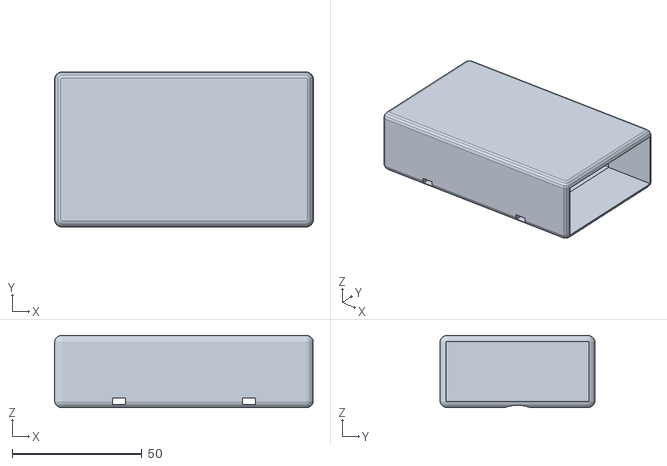
[picture p194: CAD file, 2026-09-06]
hardware/cad/stl/02_pod_base/components/01_pod_tunnel_base.stl
99.9 x 59.9 x 27.9
