schmidtmt/openmotorbridge/hardware/cad/stl/02_pod_base/design_studies/pod3_st_performance_hybrid_c_ascii.stl

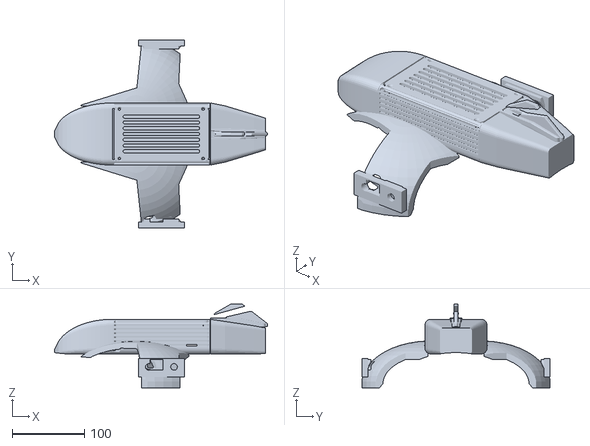
[picture p195: CAD file, 2026-09-05]
hardware/cad/stl/02_pod_base/design_studies/pod3_st_performance_hybrid_c_ascii.stl
295.1 x 260.0 x 116.0
