schmidtmt/openmotorbridge/hardware/cad/stl/02_pod_base/radar_center_underfender_mount.stl

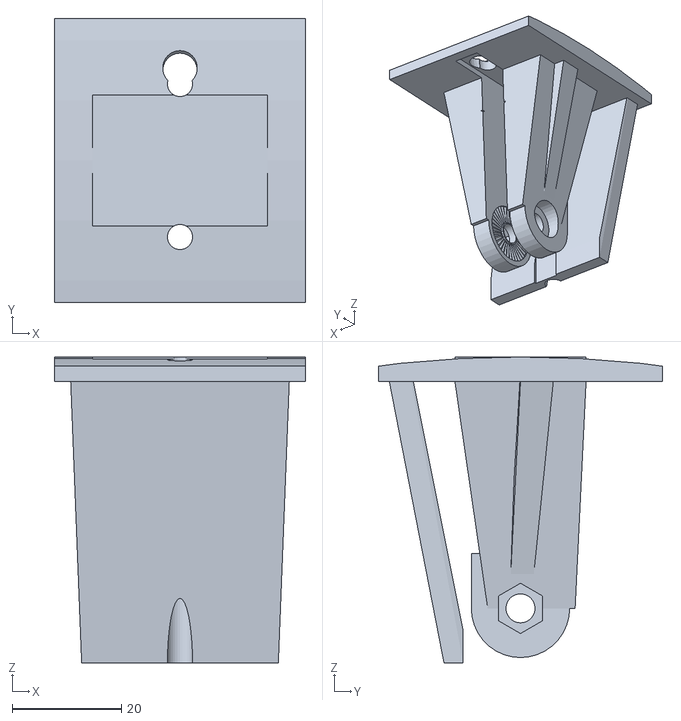
[picture p196: CAD file, 2026-10-01]
hardware/cad/stl/02_pod_base/radar_center_underfender_mount.stl
46.0 x 52.0 x 56.0
