schmidtmt/openmotorbridge/hardware/cad/stl/05_accessories/smart_keyfob_lower_shell.stl

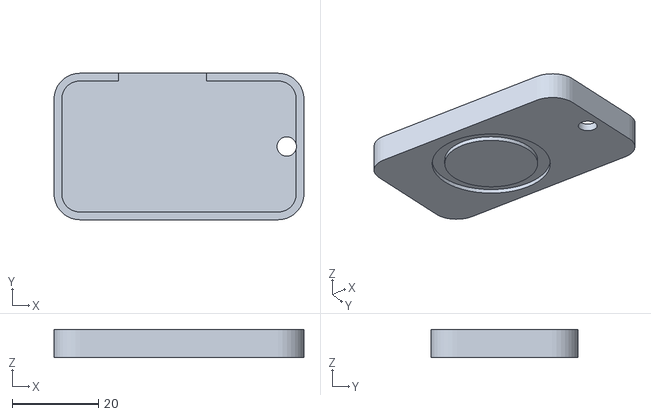
[picture p197: CAD file, 2026-09-15]
hardware/cad/stl/05_accessories/smart_keyfob_lower_shell.stl
58.0 x 34.0 x 6.50
