schmidtmt/openmotorbridge/hardware/cad/stl/02_pod_base/adventure_rack_tail_cowl.stl

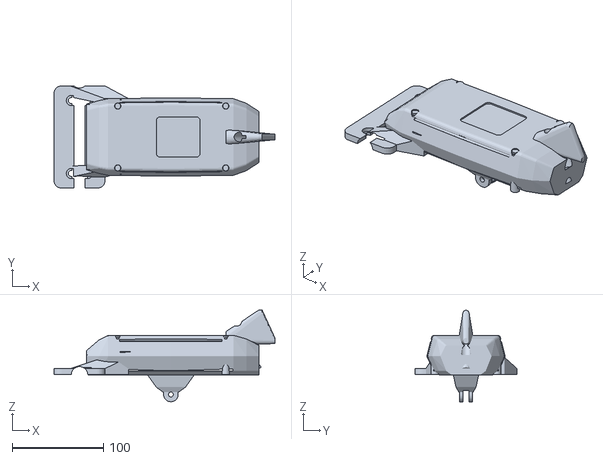
[picture p198: CAD file, 2026-09-17]
hardware/cad/stl/02_pod_base/adventure_rack_tail_cowl.stl
242.5 x 112.0 x 100.5
