schmidtmt/openmotorbridge/hardware/cad/stl/02_pod_base/components/02_pod_rear_m8_gland.stl

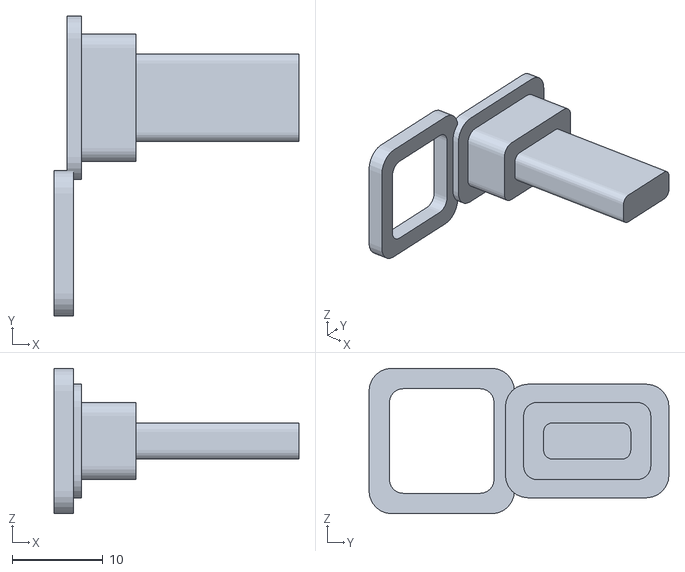
[picture p199: CAD file, 2026-09-06]
hardware/cad/stl/02_pod_base/components/02_pod_rear_m8_gland.stl
26.9 x 33.0 x 16.0
