schmidtmt/openmotorbridge/hardware/cad/stl/05_accessories/smart_keyfob_upper_shell.stl

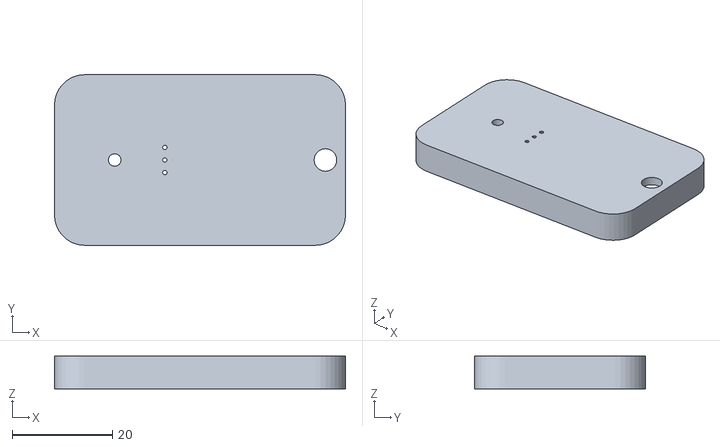
[picture p200: CAD file, 2026-09-14]
hardware/cad/stl/05_accessories/smart_keyfob_upper_shell.stl
58.0 x 34.0 x 6.50
