schmidtmt/openmotorbridge/hardware/cad/stl/02_pod_base/components/04_pod_guide_grooves.stl

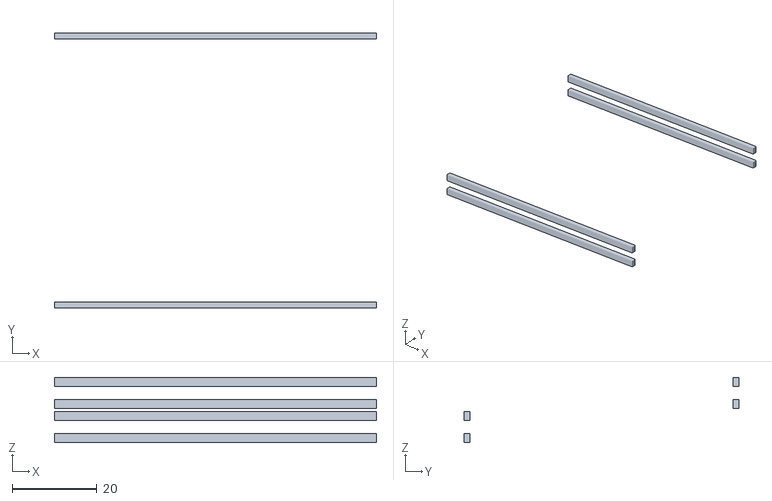
[picture p201: CAD file, 2026-09-06]
hardware/cad/stl/02_pod_base/components/04_pod_guide_grooves.stl
76.0 x 65.0 x 15.4
