schmidtmt/openmotorbridge/hardware/cad/stl/02_pod_base/components/05_pod_strap_hooks.stl

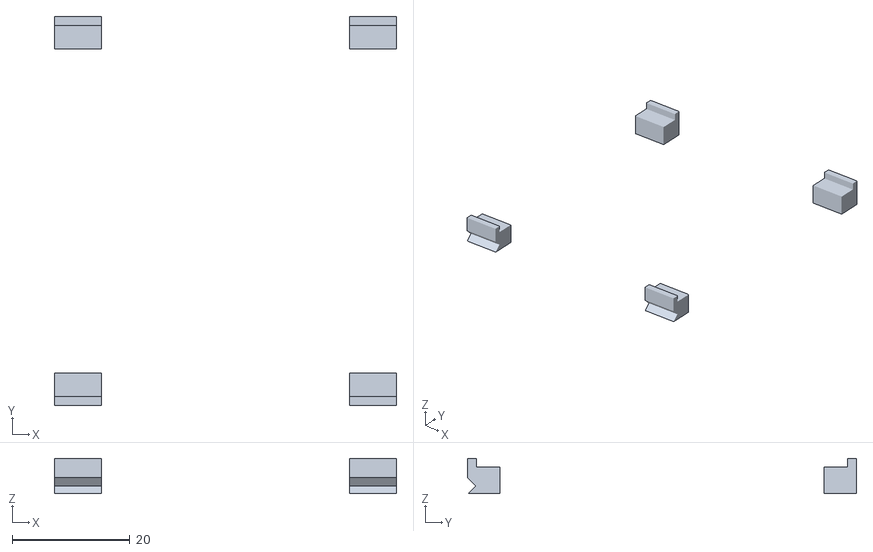
[picture p202: CAD file, 2026-09-06]
hardware/cad/stl/02_pod_base/components/05_pod_strap_hooks.stl
58.0 x 66.0 x 6.00
