schmidtmt/openmotorbridge/hardware/cad/stl/02_pod_base/adventure_underseat_cross_rail.stl

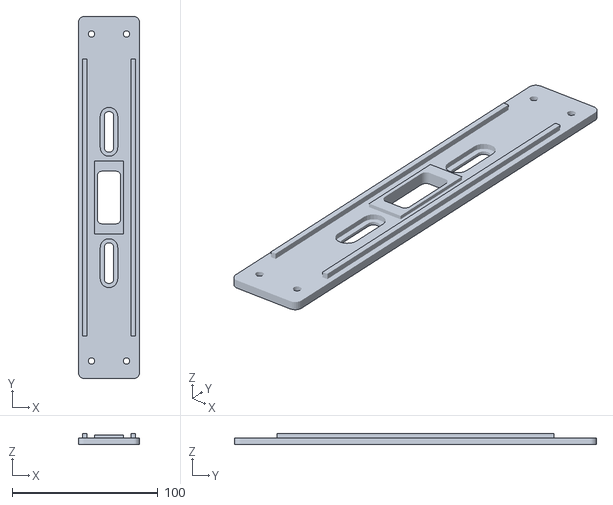
[picture p203: CAD file, 2026-09-17]
hardware/cad/stl/02_pod_base/adventure_underseat_cross_rail.stl
42.0 x 248.0 x 7.50
