schmidtmt/openmotorbridge/hardware/cad/stl/02_pod_base/adventure_pannier_rack_clamp_base.stl

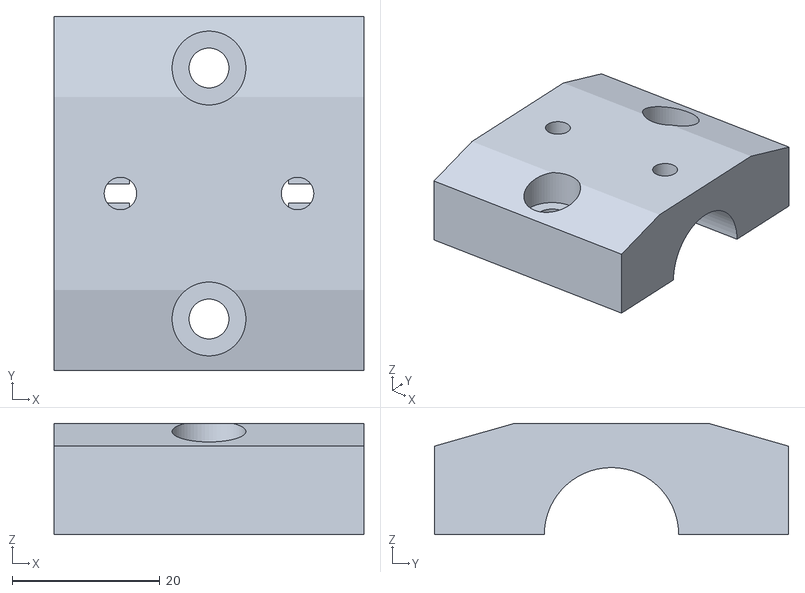
[picture p204: CAD file, 2026-09-16]
hardware/cad/stl/02_pod_base/adventure_pannier_rack_clamp_base.stl
42.0 x 48.0 x 15.1
