schmidtmt/openmotorbridge/hardware/cad/stl/02_pod_base/adventure_transition_dock.stl

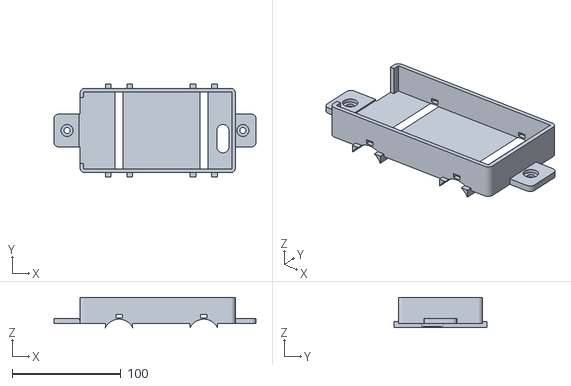
[picture p205: CAD file, 2026-09-10]
hardware/cad/stl/02_pod_base/adventure_transition_dock.stl
185.4 x 85.4 x 27.7
