schmidtmt/openmotorbridge/hardware/cad/stl/02_pod_base/radar_varia_gopro_lock_dock.stl

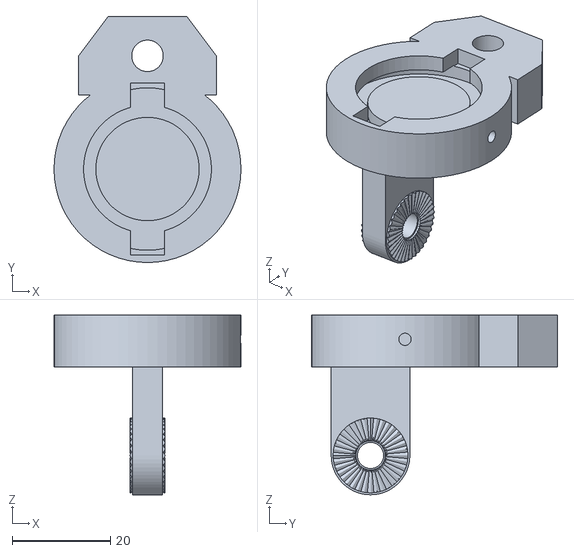
[picture p206: CAD file, 2026-09-10]
hardware/cad/stl/02_pod_base/radar_varia_gopro_lock_dock.stl
38.0 x 50.0 x 36.5
