schmidtmt/openmotorbridge/hardware/cad/stl/02_pod_base/adventure_pannier_rack_clamp_cap.stl

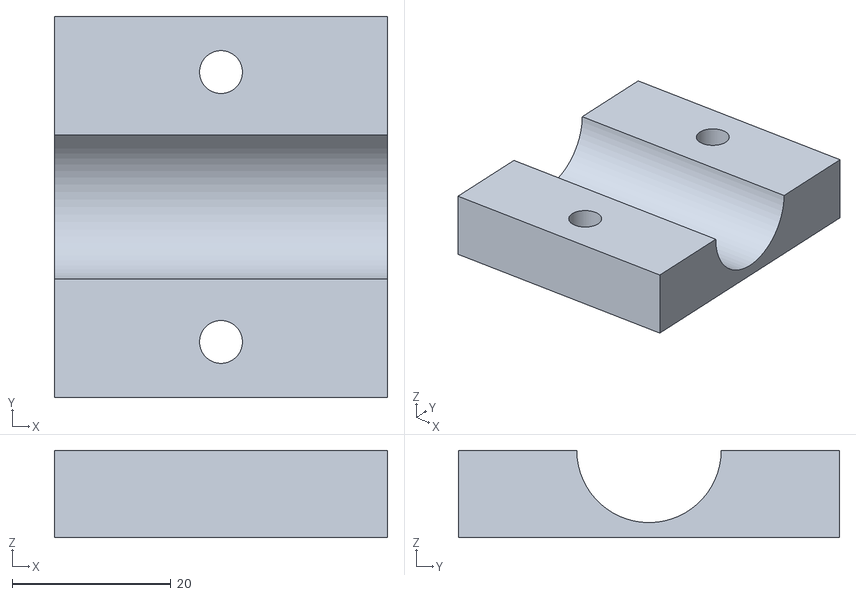
[picture p207: CAD file, 2026-09-10]
hardware/cad/stl/02_pod_base/adventure_pannier_rack_clamp_cap.stl
42.0 x 48.0 x 11.0
