schmidtmt/openmotorbridge/hardware/cad/stl/02_pod_base/cvo_st_telemetry_fin.stl

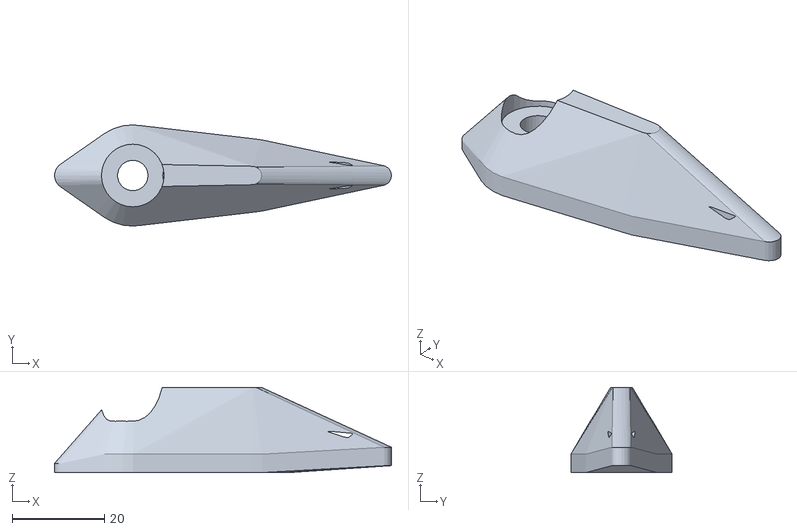
[picture p208: CAD file, 2026-09-06]
hardware/cad/stl/02_pod_base/cvo_st_telemetry_fin.stl
73.2 x 22.0 x 18.5
