schmidtmt/openmotorbridge/hardware/cad/stl/02_pod_base/cvo_st_undercowl_skeleton_dock.stl

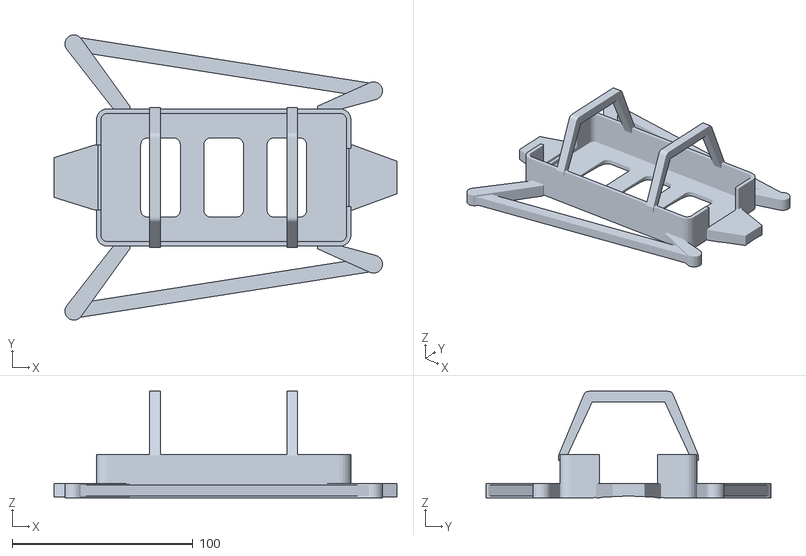
[picture p209: CAD file, 2026-09-06]
hardware/cad/stl/02_pod_base/cvo_st_undercowl_skeleton_dock.stl
190.0 x 158.0 x 59.0
