schmidtmt/openmotorbridge/hardware/cad/scad/01_main_box/00_lower_deck.scad

// =============================================================================
// OpenMotorBridge - Main Box: Complete Lower Case (Unterwanne)
// =============================================================================
// File: hardware/cad/scad/01_main_box/00_lower_deck.scad
// Description: Ready-to-print solid monocoque lower case tub with 4x M3 corner
//              clamping posts, 4x M2.5 PCB standoffs (77 x 47 mm pitch for PCBA 01),
//              internal UWB antenna floor pocket (Taoglas FXUWB10), 4x M4 silentblock
//              mounting ears, and perimeter sealing groove (100% solid leak-free floor).
// =============================================================================

include <../00_common/parameters.scad>;
include <../00_common/screw_bosses.scad>;
use <parts/000_lower_base.scad>;
use <parts/001_lower_screws_enclosure.scad>;
use <parts/002_pcb_standoffs.scad>;
use <parts/004_mounting_ears.scad>;
use <parts/005_sealing_groove.scad>;

module main_box_lower_case() {
    difference() {
        union() {
            // 1. Base Enclosure Tub (100% Solid, Homogeneous PA12 Floor)
            main_box_lower_base(
                length=MAIN_BOX_OUTER_L,
                width=MAIN_BOX_OUTER_W,
                height=MAIN_BOX_LOWER_H,
                wall=MAIN_BOX_WALL
            );

            // 2. 4x M3 Corner Clamping Posts
            main_box_corner_posts(
                length=MAIN_BOX_OUTER_L,
                width=MAIN_BOX_OUTER_W,
                height=MAIN_BOX_LOWER_H,
                post_size=MAIN_BOX_CORNER_POST,
                hole_r=M3_SCREW_HOLE_R
            );

            // 3. 4x M2.5 Mainboard PCB Screw Standoffs (85 x 55 mm PCBA 01 with 77 x 47 mm pitch)
            main_box_pcb_standoffs(
                pcb_x_offset=12.5,
                pcb_y_offset=9.5,
                h=3.5
            );

            // 4. 4x Outer M4 Silentblock Mounting Ears
            main_box_mounting_ears(
                length=MAIN_BOX_OUTER_L,
                width=MAIN_BOX_OUTER_W
            );
        }

        // 5. Perimeter Sealing Groove (Nut for Shore 40A Ø 1.5 mm O-Ring Gasket)
        main_box_sealing_groove_tool(
            length=MAIN_BOX_OUTER_L,
            width=MAIN_BOX_OUTER_W,
            z_top=MAIN_BOX_LOWER_H
        );

        // 6. 4x Captive DIN 934 / DIN 985 M3 Hex Nut Pockets (Underside z=0)
        main_box_corner_nut_pockets(
            length=MAIN_BOX_OUTER_L,
            width=MAIN_BOX_OUTER_W,
            post_size=MAIN_BOX_CORNER_POST,
            sw=NUT_M3_SW,
            h=NUT_M3_H,
            screw_r=M3_SCREW_HOLE_R
        );

        // 7. Internal UWB Antenna Floor Pocket (Taoglas FXUWB10: 12.0 x 12.0 x 0.8 mm)
        // Positioned directly below Qorvo DW3110 / ANT2 U.FL on PCBA 01 B.Cu (X=66.5, Y=37.4)
        translate([66.5, 37.4, MAIN_BOX_WALL - 0.4]) {
            cube([12.0, 12.0, 1.0], center=true);
            // U.FL Cable Relief Channel leading to ANT2
            translate([-6.0, 0, 0])
                cube([8.0, 3.5, 1.0], center=true);
        }
    }
}

// Render complete lower case
main_box_lower_case();
