schmidtmt/openmotorbridge/hardware/cad/scad/02_pod_base/97_pod_xray_assembly.scad

// =============================================================================
// OpenMotorBridge - Satellite Pod: Translucent 3D X-Ray Inspection Scene
// =============================================================================
// File: hardware/cad/scad/02_pod_base/97_pod_xray_assembly.scad
// Description: Translucent Ghosted X-Ray inspection assembly of the closed Pod
//              with inserted cartridge. Highlights internal guide rails, 6-pin
//              piston mating inside the shroud, bulkhead, and frame tube saddle.
// =============================================================================

include <../00_common/parameters.scad>;
include <../00_common/dummies/dummy_m8_connector.scad>;
include <pod_base_housing.scad>;
use <parts/008_pod_base_usbc_cap_tpu.scad>;
include <../03_pod_cartridges/00_base_sled.scad>;
include <../03_pod_cartridges/cartridge_sena.scad>;

module pod_xray_inspection_assembly() {
    // 1. Pod Base Outer Housing (Translucent Blue-Gray Glass / Ghosted Shell)
    color([0.2, 0.35, 0.55, 0.32])
        pod_base_housing();

    // 2a. Port A: M8 6-Pin IP67 Metal Connector (Rear Left, Y = 27 mm)
    translate([0, POD_OUTER_W/2.0 - 8.0, POD_OUTER_H/2.0])
        rotate([0, 180, 0])
            dummy_m8_connector();

    // 2b. Port B: USB-C Waterproof TPU Sealing Cap (Rear Right, Y = 43 mm)
    translate([0.5, POD_OUTER_W/2.0 + 8.0, POD_OUTER_H/2.0])
        rotate([0, 90, 90])
            pod_base_usbc_cap_tpu();

    // 3. 2x V4A Auto-Eject Coil Springs
    color("gold", 1.0) {
        translate([POD_BULKHEAD_X + 2.0, 16.0, POD_OUTER_H/2.0])
            rotate([0, 90, 0])
                cylinder(r=2.5, h=10.0, $fn=16);
        translate([POD_BULKHEAD_X + 2.0, POD_OUTER_W - 16.0, POD_OUTER_H/2.0])
            rotate([0, 90, 0])
                cylinder(r=2.5, h=10.0, $fn=16);
    }

    // 4. Fully Inserted Cartridge Sled (Opaque Royal Blue / Gold)
    translate([POD_BULKHEAD_X + 1.0, (POD_OUTER_W - CARTRIDGE_BASE_W)/2.0, POD_WALL]) {
        color("dodgerblue", 0.95)
            cartridge_base_sled();
    }
}

// Render complete X-Ray inspection
pod_xray_inspection_assembly();
