schmidtmt/openmotorbridge/hardware/cad/scad/02_pod_base/99_pod3_rear_assembly.scad

// =============================================================================
// OpenMotorBridge - Satellite Pod 3: Rear Transceiver Assembly
// =============================================================================
// File: hardware/cad/scad/02_pod_base/99_pod3_rear_assembly.scad
// Description: Full 3D assembly inspection of Pod 3 (Heckbürzel / Gepäckträger)
//              demonstrating that NO intermediary adapter PCB is needed: The
//              openmotorbridge_rear_transceiver PCB with GPS patch antenna and LoRa
//              sits directly inside the cartridge sled and plugs into the pod bulkhead.
// =============================================================================

include <../00_common/parameters.scad>;
include <pod_base_housing.scad>;
use <parts/008_pod_base_usbc_cap_tpu.scad>;
include <../03_pod_cartridges/cartridge_omm_transceiver.scad>;
include <../00_common/dummies/dummy_m8_connector.scad>;

// View Mode: Set to true for slide-out exploded view
EXPLODED_VIEW = true;
SLIDE_X      = EXPLODED_VIEW ? 65.0 : POD_BULKHEAD_X + 1.0;

module pod3_rear_assembly() {
    // 1. Pod Base Housing (Translucent Slate Grey)
    color("darkslategray", 0.75)
        pod_base_housing();

    // 2a. Port A: M8 6-Pin IP67 Metal Connector (Connected at rear left, Y = 27 mm)
    translate([0, POD_OUTER_W/2.0 - 8.0, POD_OUTER_H/2.0])
        rotate([0, 180, 0])
            dummy_m8_connector();

    // 2b. Port B: USB-C Waterproof TPU Sealing Cap (Connected at rear right, Y = 43 mm)
    translate([0.5, POD_OUTER_W/2.0 + 8.0, POD_OUTER_H/2.0])
        rotate([0, 90, 90])
            pod_base_usbc_cap_tpu();

    // 3. OMM Transceiver Cartridge Assembly (Slides into the Pod Base Tunnel)
    translate([SLIDE_X, (POD_OUTER_W - CARTRIDGE_BASE_W)/2.0, POD_WALL])
        cartridge_omm_transceiver_assembly(exploded = EXPLODED_VIEW);
}

// Render complete assembly
pod3_rear_assembly();
