schmidtmt/openmotorbridge/hardware/cad/scad/02_pod_base/pod_poka_yoke_cross_section.scad

// =============================================================================
// OpenMotorBridge - Satellite Pod: Poka-Yoke Asymmetrical Guide Cross-Section
// =============================================================================
// File: hardware/cad/scad/02_pod_base/pod_poka_yoke_cross_section.scad
// Description: 3D cross-sectional inspection model demonstrating the asymmetrical
//              Poka-Yoke tongue & groove linear rail mating (Left Z=10.0mm, Right Z=18.0mm).
//              Slices the pod at X=55mm, looking directly into the cross-section
//              with the inserted cartridge sled, guide rails, V-tube saddle,
//              and interior bulkhead with Auto-Eject springs.
// =============================================================================

include <../00_common/parameters.scad>;
use <pod_base_housing.scad>;
use <../03_pod_cartridges/00_base_sled.scad>;

CUT_X = 55.0;

module poka_yoke_cross_section_demo() {
    difference() {
        union() {
            // 1. Pod Base Housing Cross-Section (Sliced at X = CUT_X)
            color("darkslategray", 0.90)
                pod_base_housing();

            // 2. Correctly Inserted Cartridge Sled (Vibrant Royal Blue)
            translate([POD_BULKHEAD_X + 1.0, (POD_OUTER_W - CARTRIDGE_BASE_W)/2.0, POD_WALL])
                color("dodgerblue", 0.95)
                    cartridge_base_sled(
                        sled_l = CARTRIDGE_BASE_L,
                        sled_w = CARTRIDGE_BASE_W,
                        sled_h = CARTRIDGE_BASE_H,
                        wall   = 2.5,
                        show_latch = true
                    );
        }
        // Slice at X = CUT_X
        translate([CUT_X, -50.0, -50.0])
            cube(size=[200.0, 200.0, 200.0], center=false);
    }

    // 3. Highlight Markers / Dimension Indicators for Asymmetrical Rail Heights
    // Left Groove Indicator Pin (Bright Crimson, Z=10.0mm)
    color("crimson")
        translate([CUT_X - 1.0, 1.0, POD_GROOVE_LEFT_Z])
            rotate([0, 90, 0])
                cylinder(r=2.0, h=3.0, center=false, $fn=24);

    // Right Groove Indicator Pin (Bright Crimson, Z=18.0mm)
    color("crimson")
        translate([CUT_X - 1.0, POD_OUTER_W - 4.0, POD_GROOVE_RIGHT_Z])
            rotate([0, 90, 0])
                cylinder(r=2.0, h=3.0, center=false, $fn=24);

    // 4. Golden Auto-Eject Compression Springs in Bulkhead
    color("gold") {
        translate([POD_BULKHEAD_X + 2.0, 16.0, POD_OUTER_H/2.0])
            rotate([0, 90, 0])
                cylinder(r=2.5, h=7.0, $fn=16);
        translate([POD_BULKHEAD_X + 2.0, POD_OUTER_W - 16.0, POD_OUTER_H/2.0])
            rotate([0, 90, 0])
                cylinder(r=2.5, h=7.0, $fn=16);
    }
}

poka_yoke_cross_section_demo();
