schmidtmt/openmotorbridge/hardware/cad/scad/03_pod_cartridges/00_base_sled.scad

// =============================================================================
// OpenMotorBridge - Satellite Pod: Universal Cartridge Base Sled (Grundschlitten)
// =============================================================================
// File: hardware/cad/scad/03_pod_cartridges/00_base_sled.scad
// Description: Shared parametric base sled for all interchangeable cartridges.
//              Includes sled floor, side walls, asymmetrical Poka-Yoke guide ribs
//              with 30° lead-in chamfer, dual spring-loaded snap-fit cantilever
//              arms with squeeze release buttons and 85° latch teeth, front
//              faceplate with sealing collar, and ePTFE membrane boss.
// =============================================================================

include <../00_common/parameters.scad>;
include <../00_common/screw_bosses.scad>;
use <parts/05_magnetic_lock_latch.scad>;

module cartridge_base_sled(
    sled_l        = CARTRIDGE_BASE_L,
    sled_w        = CARTRIDGE_BASE_W,
    sled_h        = CARTRIDGE_BASE_H,
    wall          = 2.5,
    magnetic_lock = true,
    show_latch    = false,
    has_sma_port  = false,
    has_front_vent= false
) {
    y_pcb_c = sled_w / 2.0;

    difference() {
        union() {
            // 1. Sled Floor (75.0 x 54.0 x 2.5 mm)
            cube(size=[sled_l, sled_w, wall], center=false);

            // 2. Left Side Wall (75.0 x 2.5 x sled_h mm)
            cube(size=[sled_l, wall, sled_h + wall], center=false);

            // 3. Right Side Wall (75.0 x 2.5 x sled_h mm)
            translate([0, sled_w - wall, 0])
                cube(size=[sled_l, wall, sled_h + wall], center=false);

            // 4. 4x M2 PCBA 03 Mounting Standoffs (35.0 x 25.0 mm board with 29.0 x 19.0 mm pitch)
            // 100% Soldering-Iron Free PA12 self-tapping pilot holes (inner_r=0.825 for M2)
            translate([4.5, y_pcb_c - 9.5, wall])
                screw_boss(outer_r=2.4, inner_r=0.825, h=2.5);
            translate([33.5, y_pcb_c - 9.5, wall])
                screw_boss(outer_r=2.4, inner_r=0.825, h=2.5);
            translate([4.5, y_pcb_c + 9.5, wall])
                screw_boss(outer_r=2.4, inner_r=0.825, h=2.5);
            translate([33.5, y_pcb_c + 9.5, wall])
                screw_boss(outer_r=2.4, inner_r=0.825, h=2.5);

            // 5. 4x M2 Insert Fastening Corner Posts (h = 5.5 mm, z = wall .. wall + 5.5 mm)
            // Secures interchangeable modular OEM inserts (Sena, Cardo, Blindkassette) at outer perimeter
            translate([6.0, 6.0, wall])
                screw_boss(outer_r=2.8, inner_r=M2_SCREW_HOLE_R, h=5.5);
            translate([sled_l - 7.0, 6.0, wall])
                screw_boss(outer_r=2.8, inner_r=M2_SCREW_HOLE_R, h=5.5);
            translate([6.0, sled_w - 6.0, wall])
                screw_boss(outer_r=2.8, inner_r=M2_SCREW_HOLE_R, h=5.5);
            translate([sled_l - 7.0, sled_w - 6.0, wall])
                screw_boss(outer_r=2.8, inner_r=M2_SCREW_HOLE_R, h=5.5);

            // 7. Lateral Support Ledges / Shoulders (Auflagestufen at z = wall .. wall + 5.5 mm)
            // Provides continuous rigid shelf for the OEM insert and maintains 1.8 mm clearance over Carrier PCB
            translate([10.0, wall, wall])
                cube(size=[sled_l - 20.0, 1.2, 5.5], center=false);
            translate([10.0, sled_w - wall - 1.2, wall])
                cube(size=[sled_l - 20.0, 1.2, 5.5], center=false);

            // 8. Front Faceplate (4.0 x CARTRIDGE_FACE_W x CARTRIDGE_FACE_H at x = sled_l)
            translate([sled_l, -(CARTRIDGE_FACE_W - sled_w)/2.0, -(CARTRIDGE_FACE_H - sled_h)/2.0])
                cube(size=[CARTRIDGE_FACE_L, CARTRIDGE_FACE_W, CARTRIDGE_FACE_H], center=false);

            // 5. Continuous 360° Perimeter Sealing Collar (Flansch-Dichtsitz für Silikondichtung)
            // Sits at x = sled_l - 2.5 .. sled_l, completely unobstructed all around
            translate([sled_l - 2.5, -1.0, -0.5]) {
                difference() {
                    cube(size=[2.5, sled_w + 2.0, sled_h + 3.0], center=false);
                    translate([-0.1, 1.8, 1.8])
                        cube(size=[2.7, sled_w - 1.6, sled_h - 0.6], center=false);
                }
            }

            // 6. Asymmetrical Poka-Yoke Guide Ribs (Tongue Rails) with 30° Lead-in Nose
            // --- Left Guide Rib (z = POD_GROOVE_LEFT_Z center) ---
            translate([CARTRIDGE_CHAMFER_L, -CARTRIDGE_TONGUE_PROT, POD_GROOVE_LEFT_Z - CARTRIDGE_TONGUE_W/2.0])
                cube(size=[sled_l - CARTRIDGE_CHAMFER_L - 3.5, CARTRIDGE_TONGUE_PROT, CARTRIDGE_TONGUE_W], center=false);

            // Left 30° Lead-in Nose (x = 0 .. 4 mm)
            translate([0, -CARTRIDGE_TONGUE_PROT, POD_GROOVE_LEFT_Z - CARTRIDGE_TONGUE_W/2.0 + 0.3])
                cube(size=[CARTRIDGE_CHAMFER_L, CARTRIDGE_TONGUE_PROT, CARTRIDGE_TONGUE_W - 0.6], center=false);

            // --- Right Guide Rib (z = POD_GROOVE_RIGHT_Z center) ---
            translate([CARTRIDGE_CHAMFER_L, sled_w, POD_GROOVE_RIGHT_Z - CARTRIDGE_TONGUE_W/2.0])
                cube(size=[sled_l - CARTRIDGE_CHAMFER_L - 3.5, CARTRIDGE_TONGUE_PROT, CARTRIDGE_TONGUE_W], center=false);

            // Right 30° Lead-in Nose (x = 0 .. 4 mm)
            translate([0, sled_w, POD_GROOVE_RIGHT_Z - CARTRIDGE_TONGUE_W/2.0 + 0.3])
                cube(size=[CARTRIDGE_CHAMFER_L, CARTRIDGE_TONGUE_PROT, CARTRIDGE_TONGUE_W - 0.6], center=false);

            // 7. Snap-Fit Retention & Lock Mechanism
            if (magnetic_lock) {
                // --- Magnetic Anti-Theft Lock: Internal Rocker Pivot Boss & Pocket Enclosure ---
                translate([LATCH_PIVOT_X, wall + 1.5, wall])
                    screw_boss(outer_r=3.2, inner_r=M2_SCREW_HOLE_R, h=7.5);

                // Protective Enclosure Wall along inner edge of the rocker pocket
                translate([LATCH_MAGNET_X - 4.0, wall + 3.2, wall])
                    cube([LATCH_TOOTH_X - LATCH_MAGNET_X + 8.0, 1.6, 10.0]);
            } else {
                // --- Legacy Manual Quick-Release Cantilever Arms & Squeeze Buttons ---
                arm_x_start = sled_l - 24.0;
                // --- Left Arm (in side wall, clears sealing collar) ---
                translate([arm_x_start, -1.8, 6.0])
                    cube(size=[16.0, 1.8, 10.0], center=false);

                // Left Triangular Latch Tooth (retention undercut)
                translate([arm_x_start + 4.0, -3.4, 6.5]) {
                    polyhedron(
                        points=[
                            [0, 1.6, 0], [4.0, 1.6, 0], [4.0, 0, 0], [0, 1.6, 9.0], [4.0, 1.6, 9.0], [4.0, 0, 9.0]
                        ],
                        faces=[
                            [0,1,2], [3,5,4], [0,2,5,3], [1,4,5,2], [0,3,4,1]
                        ]
                    );
                }

                // Left Textured Quick-Release Squeeze Button Pad (on Faceplate Flank)
                translate([sled_l - 0.5, -4.0, 5.0]) {
                    cube(size=[CARTRIDGE_FACE_L + 1.5, 2.0, 12.0], center=false);
                    for (rz = [2.0, 6.0, 10.0]) {
                        translate([0.5, -0.6, rz])
                            cube(size=[CARTRIDGE_FACE_L, 0.6, 1.2], center=false);
                    }
                }

                // Left Flexure Link between arm and button
                translate([arm_x_start + 16.0, -3.0, 8.0])
                    cube(size=[sled_l - (arm_x_start + 16.0), 1.4, 6.0], center=false);

                // --- Right Arm (in side wall) ---
                translate([arm_x_start, sled_w, 6.0])
                    cube(size=[16.0, 1.8, 10.0], center=false);

                // Right Triangular Latch Tooth
                translate([arm_x_start + 4.0, sled_w + 1.8, 6.5]) {
                    polyhedron(
                        points=[
                            [0, 0, 0], [4.0, 0, 0], [4.0, 1.6, 0], [0, 0, 9.0], [4.0, 0, 9.0], [4.0, 1.6, 9.0]
                        ],
                        faces=[
                            [0,2,1], [3,4,5], [0,3,5,2], [1,2,5,4], [0,1,4,3]
                        ]
                    );
                }

                // Right Textured Quick-Release Squeeze Button Pad (on Faceplate Flank)
                translate([sled_l - 0.5, sled_w + 2.0, 5.0]) {
                    cube(size=[CARTRIDGE_FACE_L + 1.5, 2.0, 12.0], center=false);
                    for (rz = [2.0, 6.0, 10.0]) {
                        translate([0.5, 2.0, rz])
                            cube(size=[CARTRIDGE_FACE_L, 0.6, 1.2], center=false);
                    }
                }

                // Right Flexure Link between arm and button
                translate([arm_x_start + 16.0, sled_w + 1.6, 8.0])
                    cube(size=[sled_l - (arm_x_start + 16.0), 1.4, 6.0], center=false);
            }

            // 8. Optional Front ePTFE Gore Vent Boss on Faceplate
            if (has_front_vent) {
                translate([sled_l + 2.0, sled_w/2.0 + 12.0, sled_h/2.0])
                    rotate([0, 90, 0])
                        cylinder(r=3.0, h=2.0, center=false);
            }

            // 9. Optional Front SMA Bulkhead Flange Reinforcement Boss
            if (has_sma_port) {
                translate([sled_l, sled_w/2.0 - 12.0, sled_h/2.0])
                    rotate([0, 90, 0])
                        cylinder(r=5.5, h=2.0, center=false);
            }
        }

        // 10. Side Wall Clearance Slots / Magnetic Latch Pocket
        if (magnetic_lock) {
            // Magnetic Anti-Theft Lock: Rocker Lever Cavity & Tongue Exit Slot
            magnetic_lock_sled_pocket_tool(wall=wall, z_center=POD_GROOVE_LEFT_Z);
        } else {
            arm_x_start = sled_l - 24.0;
            // Left Arm Clearance Slots
            translate([arm_x_start - 2.0, -2.5, 4.8])
                cube(size=[19.0, wall + 3.0, 1.0], center=false);
            translate([arm_x_start - 2.0, -2.5, 16.2])
                cube(size=[19.0, wall + 3.0, 1.0], center=false);
            translate([arm_x_start - 2.0, -2.5, 4.8])
                cube(size=[2.0, wall + 3.0, 12.4], center=false);

            // Right Arm Clearance Slots
            translate([arm_x_start - 2.0, sled_w - wall - 0.5, 4.8])
                cube(size=[19.0, wall + 3.0, 1.0], center=false);
            translate([arm_x_start - 2.0, sled_w - wall - 0.5, 16.2])
                cube(size=[19.0, wall + 3.0, 1.0], center=false);
            translate([arm_x_start - 2.0, sled_w - wall - 0.5, 4.8])
                cube(size=[2.0, wall + 3.0, 12.4], center=false);
        }

        // 11. Optional Front ePTFE Breather Through-Hole (Ø 2.0 mm)
        if (has_front_vent) {
            translate([sled_l - 3.0, sled_w/2.0 + 12.0, sled_h/2.0])
                rotate([0, 90, 0])
                    cylinder(r=1.0, h=CARTRIDGE_FACE_L + 6.0, center=false);
        }

        // 12. Optional Front SMA Bulkhead Flange Bore (Ø 6.5 mm through-hole + O-Ring Recess)
        if (has_sma_port) {
            translate([sled_l - 3.0, sled_w/2.0 - 12.0, sled_h/2.0])
                rotate([0, 90, 0])
                    cylinder(r=SMA_BORE_R, h=CARTRIDGE_FACE_L + 6.0, center=false);

            // SMA Bulkhead O-Ring Recess (Ø 9.5 mm x 1.2 mm deep on outer face)
            translate([sled_l + CARTRIDGE_FACE_L - SMA_ORECESS_DEPTH + 0.01, sled_w/2.0 - 12.0, sled_h/2.0])
                rotate([0, 90, 0])
                    cylinder(r=SMA_ORECESS_R, h=SMA_ORECESS_DEPTH + 0.5, center=false);
        }

        // 13. Floor Convective Breathing Slots (4x 16 x 2.5 mm)
        translate([20.0, 10.0, -0.5]) cube(size=[16.0, 2.5, wall + 1.0], center=false);
        translate([20.0, sled_w - 12.5, -0.5]) cube(size=[16.0, 2.5, wall + 1.0], center=false);
        translate([65.0, 10.0, -0.5]) cube(size=[16.0, 2.5, wall + 1.0], center=false);
        translate([65.0, sled_w - 12.5, -0.5]) cube(size=[16.0, 2.5, wall + 1.0], center=false);

        // 14. 2x Side Wall U-Notches / Freistellungen for Rubber Strap (at x = 45 .. 65 mm)
        translate([45.0, -1.5, 11.5])
            cube(size=[20.0, wall + 3.0, sled_h + 8.0], center=false);
        translate([45.0, sled_w - wall - 1.5, 11.5])
            cube(size=[20.0, wall + 3.0, sled_h + 8.0], center=false);

        // 15. Taoglas FXUWB10 UWB 6.5 GHz Flex Antenna Pocket in Sled Floor (12 x 12 x 0.8 mm)
        // Positioned directly below ANT_UWB of PCBA 03 (X = 12.5, Y = y_pcb_c - 3.0)
        translate([12.5 - 6.0, y_pcb_c - 3.0 - 6.0, wall - 0.8])
            cube([12.0, 12.0, 0.9], center=false);
        // U.FL coaxial cable routing channel (2.0 mm wide)
        translate([12.5 - 6.0, y_pcb_c - 3.0 - 1.0, wall - 0.8])
            cube([12.0, 2.0, 0.9], center=false);

        // 16. Rear DC Contact Access Window for Pod Base Mill-Max Spring Pins
        // Gives unobstructed physical contact to PAD1 (+12V/5V) and PAD2 (GND) on B.Cu of PCBA 03
        translate([-0.5, y_pcb_c - 7.5, -0.1])
            cube([4.0, 15.0, wall + 3.5], center=false);

        // 17. 2x Auto-Eject Spring Retention Counter-Bores (Ø 5.2 mm x 2.5 mm deep)
        // Sits at Y = 10.0 mm and Y = 48.0 mm (matching guide posts in pod bulkhead)
        translate([-0.1, 10.0, 15.5])
            rotate([0, 90, 0])
                cylinder(r=2.6, h=3.0, center=false, $fn=24);
        translate([-0.1, 48.0, 15.5])
            rotate([0, 90, 0])
                cylinder(r=2.6, h=3.0, center=false, $fn=24);
    }

    // 15. Optional Kinematic Anti-Theft Latch Mechanism (Visible in Assembly Previews)
    if (magnetic_lock && show_latch) {
        translate([0, 0, POD_GROOVE_LEFT_Z - CARTRIDGE_TONGUE_W/2.0 + 3.0]) {
            translate([LATCH_PIVOT_X, 1.25, 0]) {
                translate([-LATCH_PIVOT_X, -1.25, 0]) {
                    // Rocker Lever (Lime Green PA12-CF)
                    color("#30d158", 1.0)
                        magnetic_lock_rocker_lever();
                    // Ferromagnetic Steel Dowel Pin (Ø 6 x 8 mm)
                    color("silver", 1.0)
                        translate([LATCH_MAGNET_X, 0, 0])
                            rotate([90, 0, 0])
                                cylinder(r=3.0, h=8.0, center=true, $fn=24);
                    // Return Compression Spring (Ø 3.5 x 8 mm)
                    color("gold", 1.0)
                        translate([LATCH_MAGNET_X, 2.0, 0])
                            rotate([-90, 0, 0])
                                cylinder(r=1.75, h=6.0, center=false, $fn=16);
                }
            }
        }
    }
}

// Standalone preview
cartridge_base_sled(show_latch = true);
