schmidtmt/openmotorbridge/docs/images/cad/pod3_assembly_cross_section.png

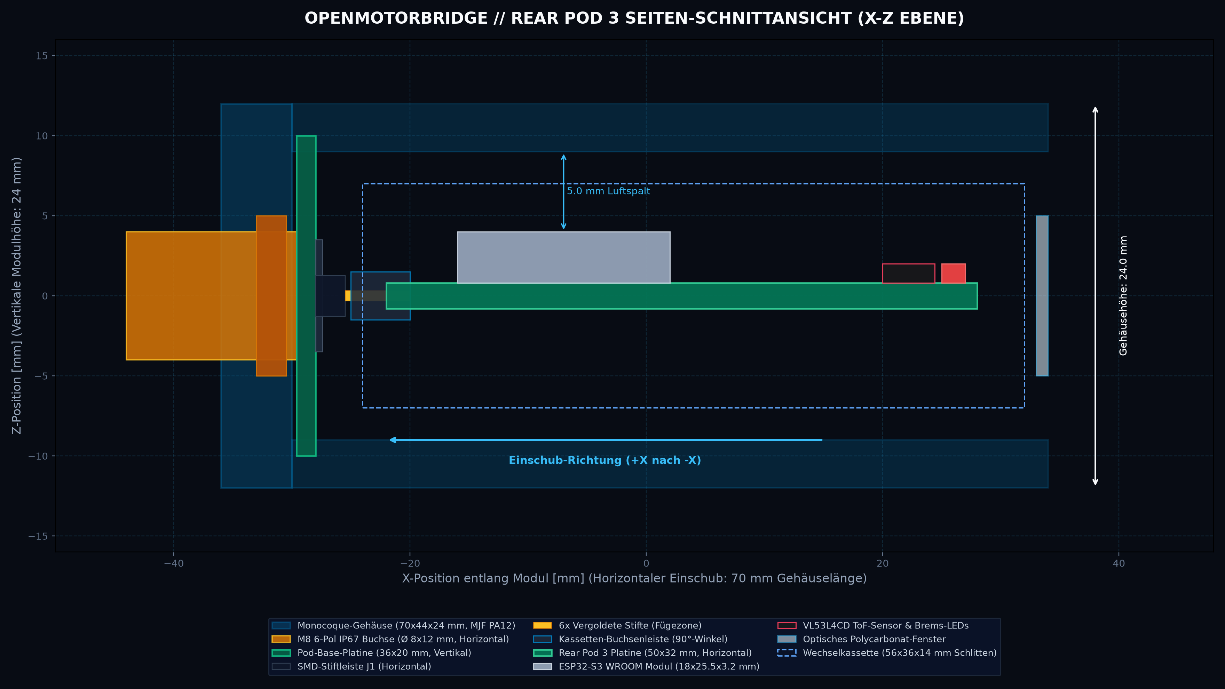
docs/images/cad/pod3_assembly_cross_section.png
