schmidtmt/openmotorbridge/docs/images/cad/pod3_assembly_mated_closeup.png

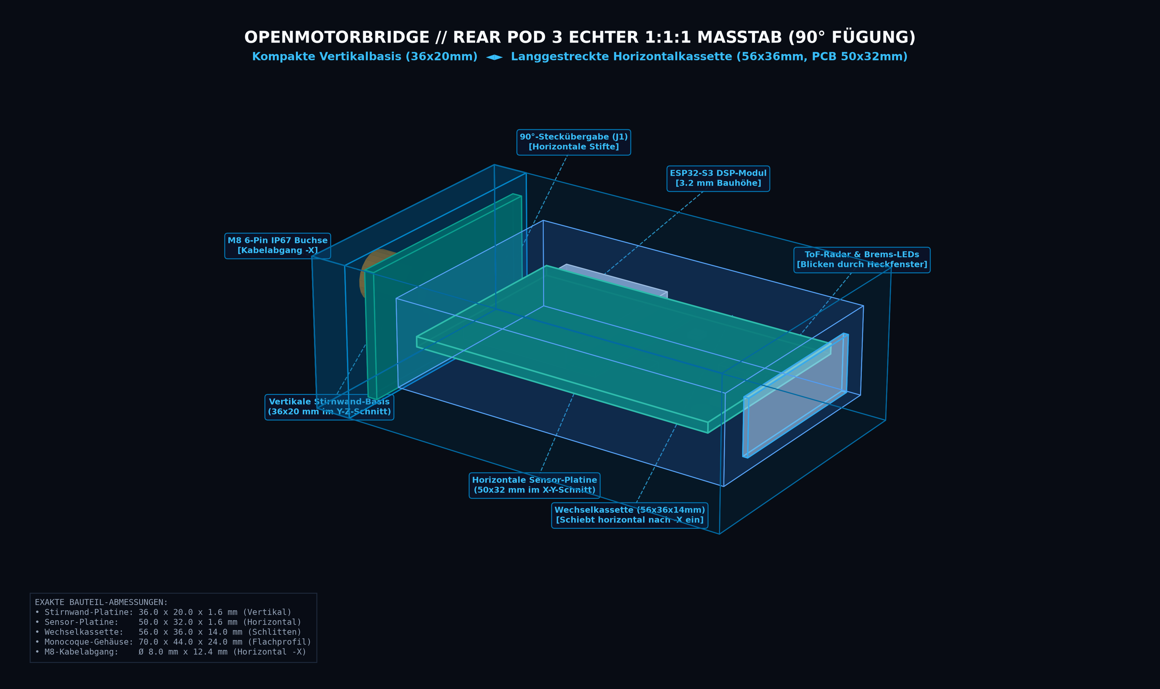
docs/images/cad/pod3_assembly_mated_closeup.png
