schmidtmt/openmotorbridge/docs/images/cad/pod3_fender_assembly_st_3d.png

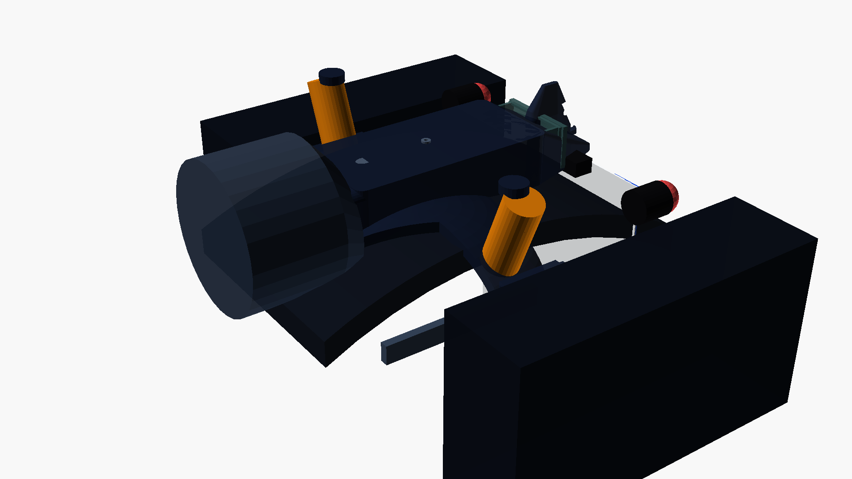
docs/images/cad/pod3_fender_assembly_st_3d.png
