schmidtmt/openmotorbridge/docs/images/cad/pod3_fender_assembly_touring_3d.png

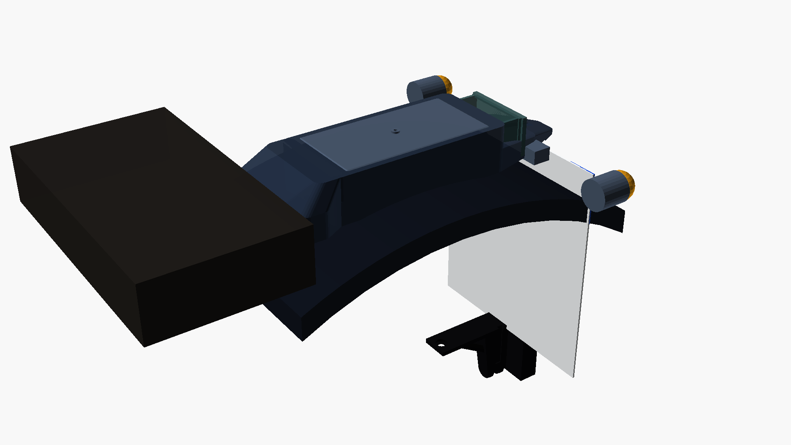
docs/images/cad/pod3_fender_assembly_touring_3d.png
