schmidtmt/openmotorbridge/docs/images/cad/pod3_full_assembly_exploded_3d.png

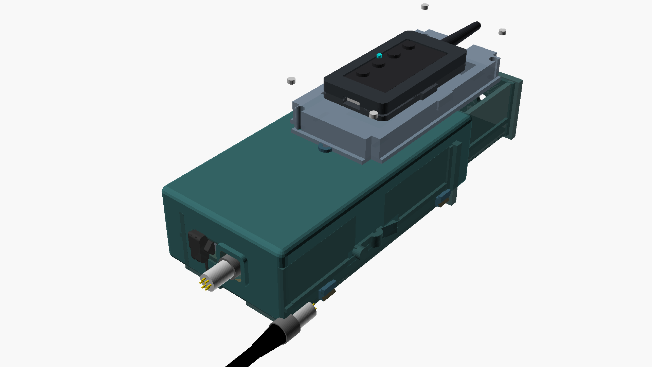
docs/images/cad/pod3_full_assembly_exploded_3d.png
