schmidtmt/openmotorbridge/hardware/cad/main_box_assembly_mated_3d.png

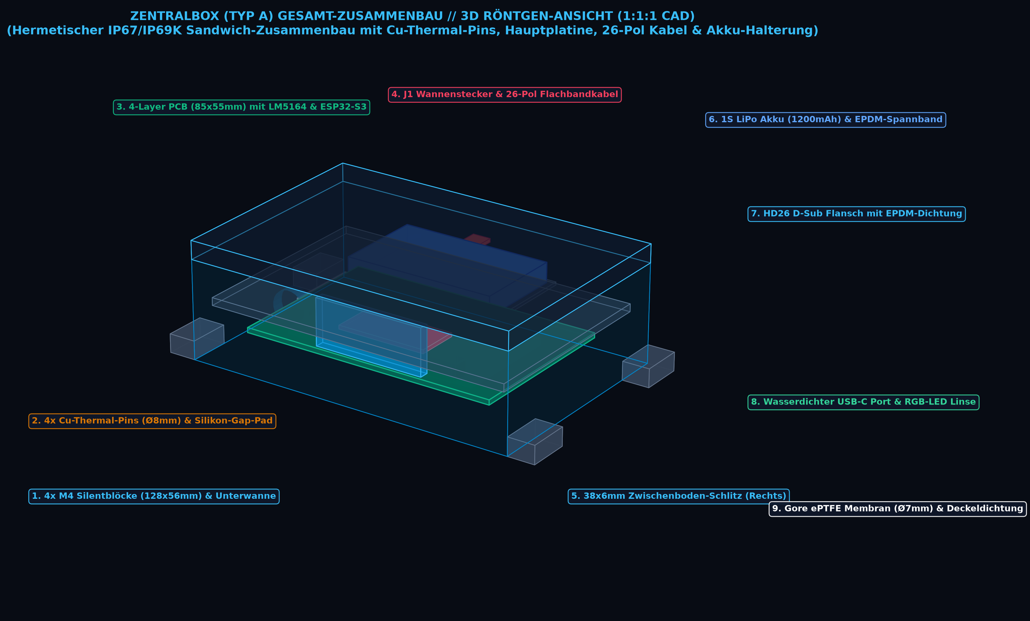
hardware/cad/main_box_assembly_mated_3d.png
