schmidtmt/openmotorbridge/hardware/cad/main_box_full_assembly_exploded_3d.png

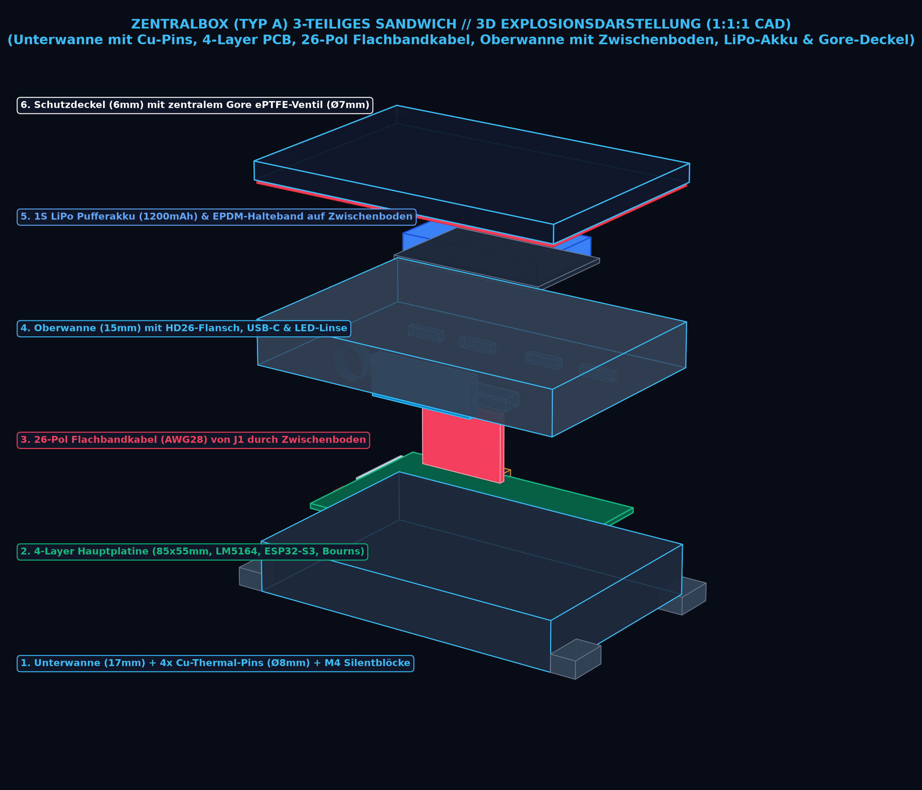
hardware/cad/main_box_full_assembly_exploded_3d.png
