schmidtmt/openmotorbridge/hardware/cad/pod3_fender_assembly_st_3d.png

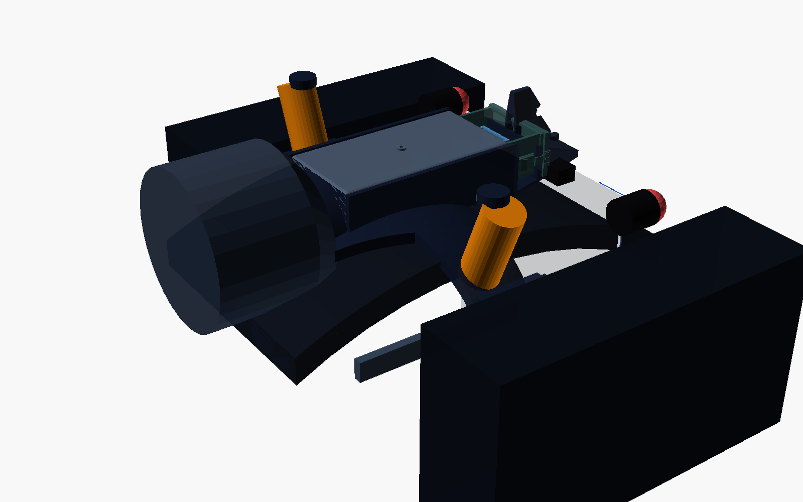
hardware/cad/pod3_fender_assembly_st_3d.png
