schmidtmt/openmotorbridge/tools/audio_testbench/index.html

OMB-DSP

# Live Audio DSP Studio & Real-Time Testbench

TRANSPARENZ: 100%

DUCKING: 0 dB

VAD: IDLE

PTT: OFF

Testton STUDIO STARTEN

1. Headset & Mikrofon

Audio-Eingabegerät

Mikrofon-Gain 1.00x

VAD-Schwellwert (Spracherkennung) 0.04

PTT DRÜCKEN

[LEERTASTE] gedrückt halten = Lenkertaste

2. Musik-Zuspielung

Riding-Synthwave (Demo)

Oder eigene MP3 / Audio-Datei:

Musik-Lautstärke 80 %

Echtzeit-Audioanalysator & Ducking-Oszilloskop Latenz: 5.3 ms

Ducking-Gain-Verlauf (15 ms Attack / 800 ms Raised-Cosine Release) 100 % (0.0 dB)

Ducking Gain Reduction (Absenkung) 0.0 dB

MIC IN -∞ dB

AMBIENT -∞ dB

MUSIK -∞ dB

HELM MASTER -∞ dB

3. Fahrzustand & Akustik

0

KM/H

N

GANG

1150

U/MIN

0 km/h (Ampel) 25 km/h (Stadt) 80 km/h (Land) 130 km/h (BAB)

Motor-Sound (Akkustik-Simulator)

Motor Starten Gasgeben [W]

Motortyp BMW Boxer 1250

Sound-Routing Ziel

Motor-Lautstärke 40 %

Transparenzmodus (Front-Mikrofon)

Speed-Gating & Status 100 % (0.0 dB)

Außengeräusch- & Alarm-Simulation:

Verkehr Martinshorn 🚨 Radar-Ping

Hardware-AGC Boost +0 dB

Stimmfilter (350 Hz - 3.2 kHz)

Ducking-Tiefe (Absenkung) -12 dB

4. Kassetten-Hot-Swap

Sena 60S

+2.5 dB / Wave EQ

Cardo Pro

Natural Voice Comp

OMM LoRa

24k Opus / 868MHz

Blindkassette

Slot Mute (-96 dB)

OpenMotorBridge Acoustic DSP Emulator v8.1 48.000 Hz / 16-Bit Stereo DMA Emulation Firmware-Ref: firmware/main_controller/src/audio_dsp_pipeline.cpp
