schmidtmt/openmotorbridge/firmware/main_controller/src/ble_service_server.cpp

#include "ble_service_server.h"
#include <stdio.h>
#include <string.h>
#include "freertos/FreeRTOS.h"
#include "freertos/task.h"
#include "esp_log.h"
#include "nimble/nimble_port.h"
#include "nimble/nimble_port_freertos.h"
#include "host/ble_hs.h"
#include "services/gap/ble_svc_gap.h"
#include "services/gatt/ble_svc_gatt.h"
#include "audio_dsp_pipeline.h"
#include "opto_pulse_sequencer.h"
#include "cartridge_onewire.h"
#include "omm_flasher.h"
#include "esp_now_front_node_client.h"
#include "gnss_omm_bridge.h"
#include "tpms_ble_scanner.h"
#include "bluetooth_audio_manager.h"
#include "radar_processor.h"
#include "hardware_inventory.h"

static const char *TAG = "BLE_SERVER";

// GATT Service & Characteristic UUIDs
// Main Service: 23d113ef-5f78-2315-deef-121200a00000
static const ble_uuid128_t gatt_svr_svc_omb_uuid =
    BLE_UUID128_INIT(0x00, 0x00, 0xA0, 0x00, 0x12, 0x12, 0xEF, 0xDE, 0x15, 0x23, 0x78, 0x5F, 0xEF, 0x13, 0xD1, 0x23);

// Telemetry Characteristic: 23d113ef-5f78-2315-deef-121200a00001
static const ble_uuid128_t gatt_svr_chr_telemetry_uuid =
    BLE_UUID128_INIT(0x01, 0x00, 0xA0, 0x00, 0x12, 0x12, 0xEF, 0xDE, 0x15, 0x23, 0x78, 0x5F, 0xEF, 0x13, 0xD1, 0x23);

// Control Characteristic: 23d113ef-5f78-2315-deef-121200a00002
static const ble_uuid128_t gatt_svr_chr_control_uuid =
    BLE_UUID128_INIT(0x02, 0x00, 0xA0, 0x00, 0x12, 0x12, 0xEF, 0xDE, 0x15, 0x23, 0x78, 0x5F, 0xEF, 0x13, 0xD1, 0x23);

static uint16_t telemetry_val_handle = 0;
static uint16_t conn_handle_pwa = BLE_HS_CONN_HANDLE_NONE;

static int gatt_svr_chr_access_omb(uint16_t conn_handle, uint16_t attr_handle,
                                   struct ble_gatt_access_ctxt *ctxt, void *arg) {
    if (ctxt->op == BLE_GATT_ACCESS_OP_WRITE_CHR) {
        uint8_t cmd[32] = {0};
        uint16_t len = OS_MBUF_PKTLEN(ctxt->om);
        if (len > sizeof(cmd)) len = sizeof(cmd);
        os_mbuf_copydata(ctxt->om, 0, len, cmd);

        ESP_LOGI(TAG, "GATT Control Command received: 0x%02X 0x%02X", cmd[0], cmd[1]);
        if (cmd[0] == 0x01) { // Change Audio Mode
            audio_set_operation_mode((AudioOperationMode)cmd[1]);
        } else if (cmd[0] == 0x02) { // Trigger Port 1 Mesh Toggle
            opto_port1_toggle_mesh();
        } else if (cmd[0] == 0x03) { // Trigger Port 1 Channel Next
            opto_port1_channel_next();
        } else if (cmd[0] == 0x04) { // Trigger Port 2 Channel Next
            opto_port2_channel_next();
        } else if (cmd[0] == 0x05) { // Trigger OEM Auto-Pairing (5s Opto Hold)
            opto_port_pairing_mode(cmd[1]);
        } else if (cmd[0] == 0x06) { // Trigger OMM High-Speed UART Push
            omm_flasher_push_from_storage("/spiffs/omm_rear.bin");
        } else if (cmd[0] == 0x07) { // Trigger Profile Merge & Hot-Reload
            cartridge_apply_profile_merge(cmd[1], (cmd[1] == 1) ? "sena_spider_x" : "cardo_dmc_gen2", 0.0f);
        } else if (cmd[0] == 0x08) { // Trigger Port 1 Group Mesh Toggle (3s Hold, S. 29)
            opto_port1_toggle_group_mesh();
        } else if (cmd[0] == 0x09) { // Smart Cartridge Opcode Dispatch (cmd[1] = port, cmd[2] = opcode)
            smart_cartridge_send_cmd(cmd[1], cmd[2]);
        } else if (cmd[0] == 0x10) { // Action-Cam: REC Start/Stop Toggle
            esp_now_front_node_cam_toggle_rec();
        } else if (cmd[0] == 0x11) { // Action-Cam: HiLight Bookmark Tag
            esp_now_front_node_cam_hilight_tag();
        } else if (cmd[0] == 0x12) { // Action-Cam: Start BLE Camera Scan
            esp_now_front_node_cam_start_scan();
        } else if (cmd[0] == 0x13) { // Action-Cam: Pair Specific Camera
            if (len >= 8) {
                esp_now_front_node_cam_pair(&cmd[1], cmd[7], (len > 8) ? reinterpret_cast<const char*>(&cmd[8]) : nullptr);
            }
        } else if (cmd[0] == 0x14) { // Action-Cam: Unpair Camera
            esp_now_front_node_cam_unpair();
        } else if (cmd[0] == 0x15) { // Action-Cam: Set Autoconnect
            esp_now_front_node_cam_set_autoconnect(cmd[1] != 0);
        } else if (cmd[0] == 0x16) { // Action-Cam: Set KL15 Fuel-Stop Filter
            esp_now_front_node_cam_set_fuel_filter(cmd[1] != 0);
        } else if (cmd[0] == 0x17) { // Front Node: 1-Click Ottocast Cold Reboot
            esp_now_front_node_reboot_ottocast();
        } else if (cmd[0] == 0x18) { // Front Node: Start Pairing / Proximity-Rescue Beacon
            esp_now_front_node_start_pairing();
        } else if (cmd[0] == 0x19) { // Front Node: Unbind & Clear NVS
            esp_now_front_node_unbind();
        } else if (cmd[0] == 0x20) { // Bike Alarm: Arm / Disarm
            bool arm = (cmd[1] != 0);
            ESP_LOGI(TAG, "Bike Alarm Guard set: %s", arm ? "ARMED" : "DISARMED");
        } else if (cmd[0] == 0x21) { // Bike Alarm: Manual Trigger Test Alert
            omm_broadcast_bike_alarm(0x02, 0.0f, 0.0f); // 0x02 = IMU shock
        } else if (cmd[0] == 0x22) { // Front Node Aux Light Mode
            esp_now_front_node_set_aux_light(cmd[1]);
        } else if (cmd[0] == 0x23) { // Front Node CAN Term Relais Mode
            esp_now_front_node_set_can_term(cmd[1] != 0);
        } else if (cmd[0] == 0x24) { // Privacy Mute Enable/Disable
            audio_set_privacy_mute_config(cmd[1] != 0);
        } else if (cmd[0] == 0x25) { // Headset Scan Start
            ESP_LOGI(TAG, "GATT: Headset Scan requested (Role: %d)", cmd[1]);
            bt_audio_start_scan(cmd[1], 10);
        } else if (cmd[0] == 0x26) { // Headset Pair
            ESP_LOGI(TAG, "GATT: Headset Pair MAC requested");
            if (rc > 7) {
                bt_audio_pair_device(cmd[1], &cmd[2]);
            }
        } else if (cmd[0] == 0x27) { // Headset Disconnect
            ESP_LOGI(TAG, "GATT: Headset Disconnect requested (Role: %d)", cmd[1]);
            bt_audio_disconnect(cmd[1]);
        } else if (cmd[0] == 0x28) { // TPMS Learn Sensor
            tpms_wheel_pos_t pos = (cmd[1] == 1) ? TPMS_WHEEL_REAR : TPMS_WHEEL_FRONT;
            tpms_ble_scanner_start_learn(pos);
        } else if (cmd[0] == 0x29) { // Radar Power Toggle
            ESP_LOGI(TAG, "GATT: Radar Power set to %s", (cmd[1] != 0) ? "ACTIVE" : "STANDBY");
        } else if (cmd[0] == 0x2A) { // Mirror BSD LEDs Toggle & Test Flash
            ESP_LOGI(TAG, "GATT: Mirror BSD LEDs set to %s (Test: %d)", (cmd[1] != 0) ? "ENABLED" : "DISABLED", cmd[2]);
        } else if (cmd[0] == 0x2B) { // Smart-Keyfob: Pair & Key Exchange
            ESP_LOGI(TAG, "GATT: Smart-Keyfob Pair command received");
            if (len >= 7) {
                smart_keyfob_pair(&cmd[1], (len >= 23) ? &cmd[7] : nullptr);
            }
        } else if (cmd[0] == 0x2C) { // Smart-Keyfob: Trigger Test Alert (Haptic/Chime)
            ESP_LOGI(TAG, "GATT: Smart-Keyfob Test Alert requested");
            smart_keyfob_send_test_alert();
        } else if (cmd[0] == 0x2D) { // Smart-Keyfob: Set Buddy Mesh Relay
            ESP_LOGI(TAG, "GATT: Smart-Keyfob Buddy Relay set to %d", cmd[1]);
            smart_keyfob_set_buddy_relay(cmd[1] != 0);
        } else if (cmd[0] == 0x2E) { // Safety Lighting: ESS Emergency Stop Signal Config
            bool ess_enable = (cmd[1] != 0);
            float threshold_g = ((int8_t)cmd[2] < 0) ? ((int8_t)cmd[2] / 100.0f) : -0.60f;
            radar_set_ess_config(ess_enable, threshold_g);
            if (cmd[3] != 0) { // Bit/byte 3 = Test Strobe Trigger
                radar_trigger_ess_test();
            }
        } else if (cmd[0] == 0x2F) { // Safety Lighting: Front Aux Light Mode
            ESP_LOGI(TAG, "GATT: Front Aux Light Mode set to %d", cmd[1]);
            esp_now_front_node_set_aux_light(cmd[1]);
        } else if (cmd[0] == 0x40) { // Safety Lighting: Radar 2.0 Macro Configuration (Persistent in NVS)
            if (len >= 3) {
                uint16_t mask = (uint16_t)cmd[1] | ((uint16_t)cmd[2] << 8);
                radar_set_macro_config(mask);
                ESP_LOGI(TAG, "GATT: Radar 2.0 Macro Config updated & saved to NVS: 0x%04X", mask);
            }
        } else if (cmd[0] == 0x41) { // Hardware Inventory Management (Baseline & Loss Acknowledgment)
            if (len >= 2) {
                uint8_t sub_cmd = cmd[1];
                if (sub_cmd == 0x01) { // Adopt current state as new baseline
                    hw_inventory_adopt_current_as_baseline();
                    ESP_LOGI(TAG, "GATT: Adopted current hardware state as new baseline");
                } else if (sub_cmd == 0x02 && len >= 4) { // Confirm removal of specific mask
                    uint16_t mask = (uint16_t)cmd[2] | ((uint16_t)cmd[3] << 8);
                    hw_inventory_confirm_removal(mask);
                    ESP_LOGI(TAG, "GATT: Confirmed removal of hardware mask 0x%04X", mask);
                } else if (sub_cmd == 0x03) { // Trigger manual re-scan
                    hw_inventory_scan_and_evaluate();
                    ESP_LOGI(TAG, "GATT: Re-scan of hardware inventory requested");
                }
            }
        }
        return 0;
    }
    return 0;
}

static TpmsData_t s_tpms_data = {
    .front_bar = 2.45f,
    .rear_bar = 2.80f,
    .front_temp_c = 24,
    .rear_temp_c = 26,
    .front_valid = true,
    .rear_valid = true,
    .is_ble_source = false
};

void ble_tpms_update(float front_bar, float rear_bar, int8_t front_temp_c, int8_t rear_temp_c) {
    s_tpms_data.front_bar = front_bar;
    s_tpms_data.rear_bar = rear_bar;
    s_tpms_data.front_temp_c = front_temp_c;
    s_tpms_data.rear_temp_c = rear_temp_c;
    s_tpms_data.front_valid = true;
    s_tpms_data.rear_valid = true;
    s_tpms_data.is_ble_source = true;
}

TpmsData_t ble_tpms_get_data(void) {
    return s_tpms_data;
}

static const struct ble_gatt_svc_def gatt_svr_svcs[] = {
    {
        .type = BLE_GATT_SVC_TYPE_PRIMARY,
        .uuid = &gatt_svr_svc_omb_uuid.u,
        .characteristics = (struct ble_gatt_chr_def[]) {
            {
                .uuid = &gatt_svr_chr_telemetry_uuid.u,
                .access_cb = gatt_svr_chr_access_omb,
                .flags = BLE_GATT_CHR_F_READ | BLE_GATT_CHR_F_NOTIFY,
                .val_handle = &telemetry_val_handle,
            },
            {
                .uuid = &gatt_svr_chr_control_uuid.u,
                .access_cb = gatt_svr_chr_access_omb,
                .flags = BLE_GATT_CHR_F_WRITE,
            },
            { 0 }
        },
    },
    { 0 }
};

static int ble_gap_event(struct ble_gap_event *event, void *arg) {
    switch (event->type) {
        case BLE_GAP_EVENT_CONNECT:
            if (event->connect.status == 0) {
                conn_handle_pwa = event->connect.conn_handle;
                ESP_LOGI(TAG, "PWA Client connected (conn_handle=%d)", conn_handle_pwa);
            }
            break;

        case BLE_GAP_EVENT_DISCONNECT:
            ESP_LOGI(TAG, "PWA Client disconnected.");
            conn_handle_pwa = BLE_HS_CONN_HANDLE_NONE;
            break;

        default:
            break;
    }
    return 0;
}

esp_err_t ble_server_init(void) {
    ESP_LOGI(TAG, "Initializing NimBLE GATT Server for WebBLE PWA...");

    nimble_port_init();
    ble_svc_gap_init();
    ble_svc_gatt_init();

    ble_svc_gap_device_name_set("OpenMotorBridge-v8");
    ble_gatts_count_cfg(gatt_svr_svcs);
    ble_gatts_add_svcs(gatt_svr_svcs);

    return ESP_OK;
}

void ble_server_notify_telemetry(const SystemTelemetry_t *telemetry) {
    if (conn_handle_pwa != BLE_HS_CONN_HANDLE_NONE && telemetry_val_handle != 0) {
        struct os_mbuf *om = ble_hs_mbuf_from_flat(telemetry, sizeof(SystemTelemetry_t));
        if (om) {
            ble_gatts_notify_custom(conn_handle_pwa, telemetry_val_handle, om);
        }
    }
}

static void ble_host_task(void *param) {
    ESP_LOGI(TAG, "NimBLE Host Task running on Core 0.");
    nimble_port_run();
    nimble_port_freertos_deinit();
}

void task_ble_services(void *pvParameters) {
    nimble_port_freertos_init(ble_host_task);

    struct ble_gap_adv_params adv_params = {};
    adv_params.conn_mode = BLE_GAP_CONN_MODE_UND;
    adv_params.disc_mode = BLE_GAP_DISC_MODE_GEN;
    ble_gap_adv_start(BLE_OWN_ADDR_PUBLIC, NULL, BLE_HS_FOREVER, &adv_params, ble_gap_event, NULL);

    while (true) {
        bt_audio_update(1000);
        vTaskDelay(pdMS_TO_TICKS(1000));
    }
}
