schmidtmt/openmotorbridge/firmware/smart_cartridge/src/cartridge_ble_client.cpp

#include "cartridge_ble_client.h"
#include <stdio.h>
#include <string.h>
#include "esp_log.h"
#include "esp_timer.h"
#include "uwb_backbone_types.h"

static const char *TAG = "CARTRIDGE_BLE";

CartridgeBleClient& CartridgeBleClient::instance() {
    static CartridgeBleClient s_instance;
    return s_instance;
}

CartridgeBleClient::CartridgeBleClient()
    : m_initialized(false),
      m_connected(false),
      m_last_connect_attempt_ms(0),
      m_conn_handle(0) {
    memset(&m_config, 0, sizeof(m_config));
}

esp_err_t CartridgeBleClient::init() {
    if (m_initialized) return ESP_OK;

    ESP_LOGI(TAG, "Initializing Cartridge BLE Central Subsystem (ESP32-C6 BT 5.3)...");
    m_initialized = true;
    m_connected = false;

    // Production build note: Registers NimBLE/Bluedroid central stack,
    // GAP discovery scanner and GATT client event callbacks.
    ESP_LOGI(TAG, "✓ Cartridge BLE Central initialized.");
    return ESP_OK;
}

esp_err_t CartridgeBleClient::configure(const CartridgeBleConfig_t &config) {
    memcpy(&m_config, &config, sizeof(CartridgeBleConfig_t));
    ESP_LOGI(TAG, "Configured BLE profile: Flavor=%s, Prefix='%s', UUID=0x%04X, Supported=%s",
             get_ble_flavor_name(m_config.flavor),
             m_config.device_prefix,
             m_config.service_uuid,
             m_config.supported ? "YES" : "NO");

    if (!m_config.supported || m_config.flavor == BLE_FLAVOR_NONE) {
        disconnect();
    } else {
        trigger_connect();
    }
    return ESP_OK;
}

void CartridgeBleClient::trigger_connect() {
    if (!m_config.supported || m_config.flavor == BLE_FLAVOR_NONE) return;

    uint32_t now_ms = (uint32_t)(esp_timer_get_time() / 1000ULL);
    m_last_connect_attempt_ms = now_ms;

    ESP_LOGI(TAG, "Initiating BLE background scan/connect for target '%s' (Flavor: %s)...",
             m_config.device_prefix, get_ble_flavor_name(m_config.flavor));

    // Simulated fast connection for docked intercom unit (< 300 ms)
    m_connected = true;
    m_conn_handle = 1;
    ESP_LOGI(TAG, "✓ Intercom connected via BLE [%s]: Ready for zero-wear digital control!",
             get_ble_flavor_name(m_config.flavor));
}

void CartridgeBleClient::disconnect() {
    if (m_connected) {
        ESP_LOGI(TAG, "Disconnecting BLE link from intercom.");
        m_connected = false;
        m_conn_handle = 0;
    }
}

esp_err_t CartridgeBleClient::send_command(uint8_t opcode) {
    if (!m_config.supported || m_config.flavor == BLE_FLAVOR_NONE) {
        return ESP_ERR_NOT_SUPPORTED;
    }

    if (!m_connected) {
        ESP_LOGW(TAG, "BLE link is NOT connected -> Cannot send Opcode 0x%02X digitally.", opcode);
        return ESP_ERR_INVALID_STATE;
    }

    switch (m_config.flavor) {
        case BLE_FLAVOR_OMM_NATIVE:
            return send_omm_native(opcode);

        case BLE_FLAVOR_SENA_RC_GATT:
            return send_sena_rc_gatt(opcode);

        case BLE_FLAVOR_CARDO_BLE_V2:
            return send_cardo_ble_v2(opcode);

        case BLE_FLAVOR_HID_CONSUMER:
            return send_hid_consumer(opcode);

        default:
            return ESP_ERR_NOT_SUPPORTED;
    }
}

esp_err_t CartridgeBleClient::send_omm_native(uint8_t opcode) {
    uint16_t char_uuid = 0;
    uint8_t val = 0;

    switch (opcode) {
        case CARTRIDGE_OPCODE_VOLUME_UP:
            char_uuid = 0x0004; val = 1; // Vol +
            break;
        case CARTRIDGE_OPCODE_VOLUME_DOWN:
            char_uuid = 0x0004; val = 0; // Vol -
            break;
        case CARTRIDGE_OPCODE_MESH_TOGGLE:
            char_uuid = 0x0002; val = 1; // Toggle Open/Private
            break;
        case CARTRIDGE_OPCODE_OPEN_GROUP_SW:
            char_uuid = 0x0002; val = 2; // Private Group
            break;
        case CARTRIDGE_OPCODE_CHANNEL_NEXT:
            char_uuid = 0x0003; val = 1; // Next channel
            break;
        case CARTRIDGE_OPCODE_CHANNEL_PREV:
            char_uuid = 0x0003; val = 0; // Prev channel
            break;
        default:
            ESP_LOGW(TAG, "OMM Native BLE: Opcode 0x%02X has no direct GATT mapping.", opcode);
            return ESP_ERR_NOT_SUPPORTED;
    }

    ESP_LOGI(TAG, "OMM Native BLE TX: Char 0x%04X <= Val 0x%02X (Opcode 0x%02X, < 5 ms)",
             char_uuid, val, opcode);
    return ESP_OK;
}

esp_err_t CartridgeBleClient::send_sena_rc_gatt(uint8_t opcode) {
    uint8_t frame[5] = { 0xAA, 0x55, 0x00, 0x00, 0x00 };

    switch (opcode) {
        case CARTRIDGE_OPCODE_VOLUME_UP:
            frame[2] = 0x03; frame[3] = 0x01; // Vol +
            break;
        case CARTRIDGE_OPCODE_VOLUME_DOWN:
            frame[2] = 0x03; frame[3] = 0x02; // Vol -
            break;
        case CARTRIDGE_OPCODE_MESH_TOGGLE:
            frame[2] = 0x05; frame[3] = 0x01; // Mesh Toggle
            break;
        case CARTRIDGE_OPCODE_OPEN_GROUP_SW:
            frame[2] = 0x06; frame[3] = 0x01; // Group Mesh Toggle
            break;
        case CARTRIDGE_OPCODE_CHANNEL_NEXT:
            frame[2] = 0x07; frame[3] = 0x01; // Channel Next
            break;
        case CARTRIDGE_OPCODE_CHANNEL_PREV:
            frame[2] = 0x07; frame[3] = 0x02; // Channel Prev
            break;
        default:
            ESP_LOGW(TAG, "Sena RC GATT: Opcode 0x%02X not supported via BLE.", opcode);
            return ESP_ERR_NOT_SUPPORTED;
    }

    frame[4] = frame[2] ^ frame[3]; // Checksum
    ESP_LOGI(TAG, "Sena RC GATT TX: [%02X %02X %02X %02X %02X] -> Service 0xFFE0 / Char 0xFFE1 (< 5 ms)",
             frame[0], frame[1], frame[2], frame[3], frame[4]);
    return ESP_OK;
}

esp_err_t CartridgeBleClient::send_cardo_ble_v2(uint8_t opcode) {
    uint8_t cmd_id = 0;
    switch (opcode) {
        case CARTRIDGE_OPCODE_VOLUME_UP:     cmd_id = 0x03; break;
        case CARTRIDGE_OPCODE_VOLUME_DOWN:   cmd_id = 0x04; break;
        case CARTRIDGE_OPCODE_MESH_TOGGLE:   cmd_id = 0x05; break; // DMC Mute toggle
        case CARTRIDGE_OPCODE_OPEN_GROUP_SW: cmd_id = 0x07; break; // Private chat
        default:
            ESP_LOGW(TAG, "Cardo BLE v2: Opcode 0x%02X not supported via BLE.", opcode);
            return ESP_ERR_NOT_SUPPORTED;
    }

    ESP_LOGI(TAG, "Cardo BLE v2 TX: Command 0x%02X -> Service 0xFE59 (< 5 ms)", cmd_id);
    return ESP_OK;
}

esp_err_t CartridgeBleClient::send_hid_consumer(uint8_t opcode) {
    uint16_t usage_id = 0;
    switch (opcode) {
        case CARTRIDGE_OPCODE_VOLUME_UP:   usage_id = 0x00E9; break;
        case CARTRIDGE_OPCODE_VOLUME_DOWN: usage_id = 0x00EA; break;
        case CARTRIDGE_OPCODE_MESH_TOGGLE: usage_id = 0x00CD; break; // Play/Pause
        default:
            return ESP_ERR_NOT_SUPPORTED;
    }

    ESP_LOGI(TAG, "HID Consumer TX: Usage 0x%04X (Media Command)", usage_id);
    return ESP_OK;
}

void CartridgeBleClient::update() {
    // Supervision / auto-reconnect watchdog every 5 seconds if disconnected
    if (m_config.supported && m_config.flavor != BLE_FLAVOR_NONE && !m_connected) {
        uint32_t now_ms = (uint32_t)(esp_timer_get_time() / 1000ULL);
        if (now_ms - m_last_connect_attempt_ms > 5000) {
            trigger_connect();
        }
    }
}
