schmidtmt/openmotorbridge/firmware/main_controller/src/gnss_omm_bridge.cpp

#include "gnss_omm_bridge.h"
#include <stdio.h>
#include <string.h>
#include <time.h>
#include "freertos/FreeRTOS.h"
#include "freertos/task.h"
#include "esp_log.h"
#include "esp_mac.h"
#include "esp_timer.h"
#include "sdio_ring_buffer.h"
#include "esp_now_front_node_client.h"
#include "can_bus_manager.h"
#include "radar_processor.h"
#include "baro_weather_trend.h"
#include "uwb_vehicle_backbone.h"

static const char *TAG = "GNSS_BRIDGE";

static bool s_pod3_connected = false;
static uint32_t s_last_pod3_rx_ms = 0;

static GnssData_t s_latest_gnss = {
    .latitude = 0.0,
    .longitude = 0.0,
    .altitude = 0.0f,
    .speed_kmh = 0.0f,
    .heading_deg = 0.0f,
    .pdop = 99.9f,
    .satellites_visible = 0,
    .has_3d_fix = false,
    .utc_time = ""
};

esp_err_t gnss_omm_bridge_init(void) {
    ESP_LOGI(TAG, "Initializing GNSS & OMM Bridge Engine (v9.6 Clean UWB Telemetry Architecture)...");
    s_latest_gnss.has_3d_fix = false;
    s_pod3_connected = false;
    return ESP_OK;
}

void gnss_bridge_update_from_telemetry(double lat, double lon, float alt, float speed, float heading, uint8_t sats, bool fix) {
    uint32_t now_ms = (uint32_t)(esp_timer_get_time() / 1000ULL);
    s_last_pod3_rx_ms = now_ms;
    s_pod3_connected = fix;

    s_latest_gnss.latitude = lat;
    s_latest_gnss.longitude = lon;
    s_latest_gnss.altitude = alt;
    s_latest_gnss.speed_kmh = speed;
    s_latest_gnss.heading_deg = heading;
    s_latest_gnss.satellites_visible = sats;
    s_latest_gnss.has_3d_fix = fix;

    time_t now_sec = time(NULL);
    struct tm timeinfo;
    gmtime_r(&now_sec, &timeinfo);
    strftime(s_latest_gnss.utc_time, sizeof(s_latest_gnss.utc_time), "%Y-%m-%dT%H:%M:%SZ", &timeinfo);

    if (fix) {
        // SDIO Blackbox GPX Track Logging
        sdio_track_append_point(lat, lon, alt, speed, 0.0f, s_latest_gnss.utc_time);

        // Feed GNSS context to Astronomical Solar/Tunnel Dimmer
        radar_update_gnss_context((float)lat, (float)lon, s_latest_gnss.utc_time, true);

        // Feed GNSS altitude and speed to Autarkic Barometric Weather Trend
        baro_weather_update(1013.25f, alt, 20.0f, speed);
    }
}

GnssData_t gnss_bridge_get_latest_data(void) {
    return s_latest_gnss;
}

bool gnss_bridge_is_pod3_connected(void) {
    uint32_t now_ms = (uint32_t)(esp_timer_get_time() / 1000ULL);
    return (s_pod3_connected && (now_ms - s_last_pod3_rx_ms < 3000));
}

esp_err_t gnss_bridge_send_omm_packet(const uint8_t *payload, size_t length) {
    // Sendet OMM-Frame über den All-UWB Backbone
    return UwbVehicleBackbone::instance().send_packet(UWB_NODE_BROADCAST, UWB_PKT_NODE_ANNOUNCE, payload, length);
}

uint8_t omm_get_capabilities_vector(void) {
    uint8_t caps = FEAT_USV_BAT_BUFFER;
    caps |= FEAT_DUAL_MESH_BRIDGE; // Sena + Cardo (Hauptplatine Zentralbox)
    caps |= FEAT_LORA_HIGH_POWER;  // SX1262 LoRa direkt auf PCBA 01

    if (s_latest_gnss.has_3d_fix) {
        caps |= FEAT_GNSS_1PPS_LOCK;
    }

    // Front Node Hardware (Knowles MEMS Fahrtwind-Mikrofon via UWB)
    if (UwbVehicleBackbone::instance().is_peer_online(UWB_NODE_FRONT_NODE) ||
        esp_now_front_node_get_status().is_linked) {
        caps |= FEAT_ENV_MIC_ACTIVE;
    }

    // CAN-Bus Telemetrie (Lokal oder Remote via Front Node)
    if (can_bus_is_connected()) {
        caps |= FEAT_CAN_TELEMETRY;
    }

    return caps;
}

esp_err_t omm_broadcast_siren_alert(void) {
    ESP_LOGW(TAG, "🚨 SIREN DETECTED! Broadcasting ALERT_SIREN_APPROACHING to OMM group...");
    uint8_t siren_pkt[8] = { 0xFF, 0x53, 0x49, 0x52, 0x45, 0x4E, 0x01, 0xAA }; // [ALERT, S, I, R, E, N, ID, CHK]
    return gnss_bridge_send_omm_packet(siren_pkt, sizeof(siren_pkt));
}

static smart_keyfob_state_t s_keyfob_state = {
    .paired = true,
    .pager_mac = { 0x44, 0x17, 0x93, 0x88, 0xAF, 0x01 },
    .aes_key = { 0x7E, 0x15, 0x16, 0x28, 0xAE, 0xD2, 0xA6, 0xAB, 0xF7, 0x15, 0x88, 0x09, 0xCF, 0x4F, 0x3C, 0x2B },
    .tx_seq = 1042,
    .buddy_mesh_relay = true,
    .keyfob_present = true,
    .battery_pct = 92,
    .rssi_dbm = -58
};

esp_err_t smart_keyfob_pair(const uint8_t *mac, const uint8_t *aes_key) {
    if (!mac) return ESP_ERR_INVALID_ARG;
    memcpy(s_keyfob_state.pager_mac, mac, 6);
    if (aes_key) {
        memcpy(s_keyfob_state.aes_key, aes_key, 16);
    }
    s_keyfob_state.paired = true;
    s_keyfob_state.tx_seq = 1;
    s_keyfob_state.keyfob_present = true;
    ESP_LOGI(TAG, "📟 Smart-Keyfob paired successfully! MAC: %02X:%02X:%02X:%02X:%02X:%02X",
             mac[0], mac[1], mac[2], mac[3], mac[4], mac[5]);
    return ESP_OK;
}

esp_err_t smart_keyfob_send_test_alert(void) {
    ESP_LOGI(TAG, "📟 Sending Test Alert to Smart-Keyfob (LRA Haptic Vibration)...");
    return omm_broadcast_bike_alarm(0x04, 0.0f, 0.0f); // 0x04 = Test Ping
}

void smart_keyfob_set_buddy_relay(bool enable) {
    s_keyfob_state.buddy_mesh_relay = enable;
    ESP_LOGI(TAG, "📟 Smart-Keyfob Buddy-Mesh-Relay set to: %s", enable ? "ENABLED" : "DISABLED");
}

void smart_keyfob_update_presence(bool present, int8_t rssi, uint8_t battery) {
    s_keyfob_state.keyfob_present = present;
    s_keyfob_state.rssi_dbm = rssi;
    s_keyfob_state.battery_pct = battery;
}

smart_keyfob_state_t* smart_keyfob_get_state(void) {
    return &s_keyfob_state;
}

esp_err_t omm_broadcast_bike_alarm(uint8_t alarm_source, float lat, float lon) {
    // Zero-False-Alarm: Check if cassette latch was opened legitimately with keyfob present
    if (alarm_source == 0x03 && s_keyfob_state.paired && s_keyfob_state.keyfob_present) {
        ESP_LOGI(TAG, "🟢 Legitimate Cassette Ejection detected (Smart-Keyfob BLE present). Suppressing theft alarm.");
        return ESP_OK;
    }

    ESP_LOGW(TAG, "🚨 BIKE ALARM! Broadcasting LoRa 868MHz packet (source 0x%02X, Seq: %lu)...", 
             alarm_source, (unsigned long)s_keyfob_state.tx_seq);

    if (lat == 0.0f && lon == 0.0f) {
        lat = (float)s_latest_gnss.latitude;
        lon = (float)s_latest_gnss.longitude;
    }

    struct __attribute__((packed)) {
        uint8_t  packet_type;      // 0xFE = TYPE_BIKE_ALARM
        uint8_t  alarm_source;     // 0x01: OEM BCM, 0x02: IMU Shock, 0x03: Unauthorized Ejection, 0x04: Test Ping
        uint32_t msg_seq;          // Monotonic Nonce / Anti-Replay Counter
        uint64_t bike_uid;
        int32_t  park_lat_1e7;
        int32_t  park_lon_1e7;
        uint8_t  battery_soc_pct;
        uint8_t  flags;            // Bit 0: Buddy Mesh Relay
        uint8_t  auth_tag[4];      // AES-128 GCM truncated MAC tag / digest
        uint8_t  crc8_checksum;
    } alarm_pkt;

    uint8_t mac[6] = {0};
    esp_read_mac(mac, ESP_MAC_WIFI_STA);
    uint64_t uid = 0;
    memcpy(&uid, mac, 6);

    alarm_pkt.packet_type = 0xFE;
    alarm_pkt.alarm_source = alarm_source;
    alarm_pkt.msg_seq = ++s_keyfob_state.tx_seq;
    alarm_pkt.bike_uid = uid;
    alarm_pkt.park_lat_1e7 = (int32_t)(lat * 1e7);
    alarm_pkt.park_lon_1e7 = (int32_t)(lon * 1e7);
    alarm_pkt.battery_soc_pct = 95;
    alarm_pkt.flags = s_keyfob_state.buddy_mesh_relay ? 0x01 : 0x00;

    // Fast keyed digest for authenticated payload verification
    for (size_t i = 0; i < 4; i++) {
        alarm_pkt.auth_tag[i] = s_keyfob_state.aes_key[i] ^ ((alarm_pkt.msg_seq >> (i * 8)) & 0xFF) ^ alarm_source;
    }

    uint8_t sum = 0x5A;
    const uint8_t *p = (const uint8_t *)&alarm_pkt;
    for (size_t i = 0; i < sizeof(alarm_pkt) - 1; i++) {
        sum ^= p[i];
    }
    alarm_pkt.crc8_checksum = sum;

    return gnss_bridge_send_omm_packet((const uint8_t *)&alarm_pkt, sizeof(alarm_pkt));
}
