schmidtmt/openmotorbridge/firmware/front_node/src/ota_service_manager.cpp

#include "ota_service_manager.h"
#include "esp_log.h"
#include "esp_system.h"
#include "cockpit_can_manager.h"
#include "esp_now_bridge.h"

static const char* TAG = "OTA_MGR";

#define HEALTH_CHECK_TIMEOUT_MS 30000 // 30-second evaluation window

OtaServiceManager& OtaServiceManager::instance() {
    static OtaServiceManager inst;
    return inst;
}

OtaServiceManager::OtaServiceManager()
    : m_updating(false)
    , m_ota_handle(0)
    , m_update_partition(nullptr)
    , m_received_bytes(0)
    , m_total_bytes(0)
    , m_health_pending(false)
    , m_health_passed(false)
    , m_health_timer_ms(0)
    , m_can_frames_seen(0)
    , m_espnow_pings_seen(0)
{
}

bool OtaServiceManager::init() {
    const esp_partition_t* running = esp_ota_get_running_partition();
    if (running) {
        ESP_LOGI(TAG, "Current running partition: '%s' at offset 0x%08lX (type %d, subtype %d)",
                 running->label, running->address, running->type, running->subtype);
    }
    confirm_running_partition();
    return true;
}

void OtaServiceManager::confirm_running_partition() {
    esp_ota_img_states_t ota_state;
    const esp_partition_t* running = esp_ota_get_running_partition();

    if (esp_ota_get_state_partition(running, &ota_state) == ESP_OK) {
        if (ota_state == ESP_OTA_IMG_PENDING_VERIFY) {
            ESP_LOGW(TAG, "First boot after OTA! Entering 30s Self-Health Validation window before confirming app...");
            m_health_pending = true;
            m_health_passed = false;
            m_health_timer_ms = 0;
            m_can_frames_seen = 0;
            m_espnow_pings_seen = 0;
        } else {
            m_health_pending = false;
            m_health_passed = true;
        }
    } else {
        m_health_pending = false;
        m_health_passed = true;
    }
}

void OtaServiceManager::record_can_activity() {
    m_can_frames_seen++;
}

void OtaServiceManager::record_espnow_activity() {
    m_espnow_pings_seen++;
}

bool OtaServiceManager::is_health_check_pending() const {
    return m_health_pending;
}

bool OtaServiceManager::is_health_check_passed() const {
    return m_health_passed;
}

uint32_t OtaServiceManager::get_health_check_remaining_sec() const {
    if (!m_health_pending) return 0;
    if (m_health_timer_ms >= HEALTH_CHECK_TIMEOUT_MS) return 0;
    return (HEALTH_CHECK_TIMEOUT_MS - m_health_timer_ms) / 1000;
}

void OtaServiceManager::update_health_check(uint32_t delta_ms) {
    if (!m_health_pending || m_health_passed) {
        return;
    }

    m_health_timer_ms += delta_ms;

    // 1. Evaluate verification criteria:
    // Criteria A: CAN Bus communication functional (either recorded activity or manager has RX frames)
    bool can_ok = (m_can_frames_seen > 0) || (CockpitCanManager::instance().get_rx_frame_count() > 0);

    // Criteria B: ESP-NOW wireless bridge communication functional with Central Box
    bool espnow_ok = (m_espnow_pings_seen > 0) || 
                     (EspNowBridge::instance().get_binding_state() == BINDING_STATE_LINKED);

    // 2. If both core interfaces are alive, mark partition as permanently VALID
    if (can_ok && espnow_ok) {
        m_health_passed = true;
        m_health_pending = false;
        esp_err_t err = esp_ota_mark_app_valid_cancel_rollback();
        if (err == ESP_OK) {
            ESP_LOGI(TAG, "Self-Health Check PASSED after %lu ms! (CAN frames: %lu, ESP-NOW pings: %lu). App marked permanently VALID.",
                     m_health_timer_ms, m_can_frames_seen, m_espnow_pings_seen);
        } else {
            ESP_LOGE(TAG, "Failed to mark app valid: %s", esp_err_to_name(err));
        }
        return;
    }

    // 3. If timeout expires without passing health check -> Trigger Automatic Hardware Rollback
    if (m_health_timer_ms >= HEALTH_CHECK_TIMEOUT_MS) {
        ESP_LOGE(TAG, "Self-Health Check FAILED / TIMED OUT after 30s! (CAN OK: %d, ESP-NOW OK: %d). Triggering Rollback...",
                 can_ok, espnow_ok);
        m_health_pending = false;
        esp_ota_mark_app_invalid_rollback_and_reboot();
    }
}

bool OtaServiceManager::begin_update(size_t image_size) {
    if (m_updating) {
        ESP_LOGW(TAG, "OTA already in progress, aborting previous session.");
        abort_update();
    }

    const esp_partition_t* running = esp_ota_get_running_partition();
    m_update_partition = esp_ota_get_next_update_partition(NULL);

    if (!m_update_partition) {
        ESP_LOGE(TAG, "No valid target OTA partition found!");
        return false;
    }

    ESP_LOGI(TAG, "Beginning OTA update to partition '%s' at 0x%08lX (Expected size: %zu bytes)",
             m_update_partition->label, m_update_partition->address, image_size);

    esp_err_t err = esp_ota_begin(m_update_partition, image_size, &m_ota_handle);
    if (err != ESP_OK) {
        ESP_LOGE(TAG, "esp_ota_begin failed: %s", esp_err_to_name(err));
        return false;
    }

    m_updating = true;
    m_received_bytes = 0;
    m_total_bytes = image_size;
    return true;
}

bool OtaServiceManager::write_chunk(const uint8_t* data, size_t len) {
    if (!m_updating || !data || len == 0) return false;

    esp_err_t err = esp_ota_write(m_ota_handle, data, len);
    if (err != ESP_OK) {
        ESP_LOGE(TAG, "esp_ota_write failed at offset %zu: %s", m_received_bytes, esp_err_to_name(err));
        abort_update();
        return false;
    }

    m_received_bytes += len;
    return true;
}

bool OtaServiceManager::finalize_and_reboot() {
    if (!m_updating) return false;

    esp_err_t err = esp_ota_end(m_ota_handle);
    if (err != ESP_OK) {
        ESP_LOGE(TAG, "esp_ota_end failed: %s", esp_err_to_name(err));
        m_updating = false;
        return false;
    }

    err = esp_ota_set_boot_partition(m_update_partition);
    if (err != ESP_OK) {
        ESP_LOGE(TAG, "esp_ota_set_boot_partition failed: %s", esp_err_to_name(err));
        m_updating = false;
        return false;
    }

    ESP_LOGI(TAG, "OTA update SUCCESS! Transferred %zu bytes. Next boot target: '%s'. Restarting MCU...",
             m_received_bytes, m_update_partition->label);

    m_updating = false;
    esp_restart();
    return true;
}

void OtaServiceManager::abort_update() {
    if (m_updating) {
        esp_ota_abort(m_ota_handle);
        m_updating = false;
        m_received_bytes = 0;
        m_total_bytes = 0;
        ESP_LOGW(TAG, "OTA session aborted. Existing firmware retained intact.");
    }
}

bool OtaServiceManager::is_updating() const {
    return m_updating;
}

size_t OtaServiceManager::get_received_bytes() const {
    return m_received_bytes;
}

size_t OtaServiceManager::get_total_bytes() const {
    return m_total_bytes;
}
