schmidtmt/openmotorbridge/firmware/front_node/src/handlebar_ptt_handler.cpp

#include "handlebar_ptt_handler.h"
#include "front_node_config.h"
#include "esp_timer.h"
#include "esp_log.h"
#include "driver/gpio.h"

static const char* TAG = "PTT_HANDLER";

HandlebarPttHandler& HandlebarPttHandler::instance() {
    static HandlebarPttHandler inst;
    return inst;
}

HandlebarPttHandler::HandlebarPttHandler()
    : m_event_queue(nullptr)
    , m_is_pressed(false)
    , m_last_edge_us(0)
    , m_action_cb(nullptr)
    , m_press_start_us(0)
    , m_release_time_us(0)
    , m_click_count(0)
    , m_long_press_fired(false)
    , m_reset_hold_fired(false)
{
}

#include "ws2812b_led_manager.h"

void IRAM_ATTR HandlebarPttHandler::isr_handler(void* arg) {
    HandlebarPttHandler* self = static_cast<HandlebarPttHandler*>(arg);
    uint64_t now = esp_timer_get_time();
    
    // Hardware-assisted microsecond debounce check
    if ((now - self->m_last_edge_us) < (PTT_DEBOUNCE_MS * 1000ULL)) {
        return;
    }
    self->m_last_edge_us = now;

    // Read all 3 active-low inputs (0 = Pressed, 1 = Released)
    int lvl1 = gpio_get_level(PIN_PTT_IN1_N);
    int lvl2 = gpio_get_level(PIN_PTT_IN2_N);
    int lvl3 = gpio_get_level(PIN_PTT_IN3_N);

    uint8_t btn_id = BTN_INTERCOM_PTT;
    bool pressed = false;

    if (lvl1 == 0) {
        btn_id = BTN_INTERCOM_PTT;
        pressed = true;
    } else if (lvl2 == 0) {
        btn_id = BTN_CAM_HIGHLIGHT;
        pressed = true;
    } else if (lvl3 == 0) {
        btn_id = BTN_MEDIA_VOICE;
        pressed = true;
    } else {
        // All released
        pressed = false;
        btn_id = BTN_INTERCOM_PTT;
    }

    self->m_is_pressed = pressed;

    PttEvent evt = {
        .button_id = btn_id,
        .pressed = pressed,
        .timestamp_us = now
    };

    BaseType_t high_task_woken = pdFALSE;
    if (self->m_event_queue) {
        xQueueSendFromISR(self->m_event_queue, &evt, &high_task_woken);
    }

    if (high_task_woken == pdTRUE) {
        portYIELD_FROM_ISR();
    }
}

bool HandlebarPttHandler::init() {
    m_event_queue = xQueueCreate(16, sizeof(PttEvent));
    if (!m_event_queue) {
        ESP_LOGE(TAG, "Failed to allocate PTT event queue");
        return false;
    }

    uint64_t pin_mask = (1ULL << PIN_PTT_IN1_N) |
                        (1ULL << PIN_PTT_IN2_N) |
                        (1ULL << PIN_PTT_IN3_N);

    gpio_config_t io_conf = {
        .pin_bit_mask = pin_mask,
        .mode = GPIO_MODE_INPUT,
        .pull_up_en = GPIO_PULLUP_ENABLE, // Internal pullup backup to external 10k resistor
        .pull_down_en = GPIO_PULLDOWN_DISABLE,
        .intr_type = GPIO_INTR_ANYEDGE,    // Trigger on both press and release
    };

    esp_err_t err = gpio_config(&io_conf);
    if (err != ESP_OK) {
        ESP_LOGE(TAG, "gpio_config failed: %s", esp_err_to_name(err));
        return false;
    }

    // Read initial state
    m_is_pressed = (gpio_get_level(PIN_PTT_IN1_N) == 0) ||
                   (gpio_get_level(PIN_PTT_IN2_N) == 0) ||
                   (gpio_get_level(PIN_PTT_IN3_N) == 0);

    // Install ISR service if not already present
    gpio_install_isr_service(ESP_INTR_FLAG_IRAM);
    gpio_isr_handler_add(PIN_PTT_IN1_N, isr_handler, this);
    gpio_isr_handler_add(PIN_PTT_IN2_N, isr_handler, this);
    gpio_isr_handler_add(PIN_PTT_IN3_N, isr_handler, this);

    ESP_LOGI(TAG, "Handlebar Multi-Button driver initialized (GPIO15/16/17, Active-Low, Interrupt-Driven). Initial: %s",
             m_is_pressed ? "PRESSED" : "RELEASED");
    return true;
}

void HandlebarPttHandler::set_action_callback(PttActionCallback cb) {
    m_action_cb = cb;
}

bool HandlebarPttHandler::get_event(PttEvent* evt, TickType_t wait_ticks) {
    if (!m_event_queue || !evt) return false;
    bool received = (xQueueReceive(m_event_queue, evt, wait_ticks) == pdTRUE);
    if (received) {
        uint64_t now = evt->timestamp_us;
        if (evt->pressed) {
            // Key Down: Trigger white flash on WS2812B RGB light-pipe
            Ws2812bLedManager::instance().trigger_click_flash();
            m_press_start_us = now;
            m_long_press_fired = false;
            m_reset_hold_fired = false;
        } else {
            // Key Up
            m_reset_hold_fired = false;
            if (!m_long_press_fired) {
                uint64_t press_duration_ms = (now - m_press_start_us) / 1000ULL;
                if (press_duration_ms < 450) {
                    m_click_count++;
                    m_release_time_us = now;

                    if (m_click_count >= 2) {
                        ESP_LOGI(TAG, "⚡ PTT Double-Click Detected -> Triggering Action-Cam REC Toggle");
                        if (m_action_cb) {
                            m_action_cb(PTT_CLICK_DOUBLE);
                        }
                        m_click_count = 0;
                    }
                }
            }
        }
    }
    return received;
}

void HandlebarPttHandler::update() {
    uint64_t now = esp_timer_get_time();

    // 1. Long Press Detection while pressed (>800ms)
    if (m_is_pressed && !m_long_press_fired && m_press_start_us > 0) {
        if ((now - m_press_start_us) >= (PTT_LONG_PRESS_MS * 1000ULL)) {
            m_long_press_fired = true;
            m_click_count = 0;
            ESP_LOGI(TAG, "⚡ PTT Long-Press (>%d ms) Detected -> Triggering Action-Cam HiLight Marker", PTT_LONG_PRESS_MS);
            if (m_action_cb) {
                m_action_cb(PTT_CLICK_LONG);
            }
        }
    }

    // 1b. 10-Second Continuous Hold Detection for Binding Reset (10,000 ms)
    if (m_is_pressed && !m_reset_hold_fired && m_press_start_us > 0) {
        if ((now - m_press_start_us) >= (PTT_RESET_HOLD_MS * 1000ULL)) {
            m_reset_hold_fired = true;
            m_click_count = 0;
            ESP_LOGW(TAG, "⚡ PTT 10s Continuous Hold Detected -> Triggering Front Node Unpair / Pairing Reset");
            if (m_action_cb) {
                m_action_cb(PTT_CLICK_RESET_PAIRING);
            }
        }
    }

    // 2. Single-click expiration after release
    if (!m_is_pressed && m_click_count == 1 && m_release_time_us > 0) {
        if ((now - m_release_time_us) >= (PTT_DOUBLE_CLICK_MS * 1000ULL)) {
            m_click_count = 0;
            if (m_action_cb) {
                m_action_cb(PTT_CLICK_SINGLE);
            }
        }
    }
}

bool HandlebarPttHandler::is_pressed() const {
    return m_is_pressed;
}
